dotimothy/TheDoPro/Documentation/Images/Figure for Methodology.png

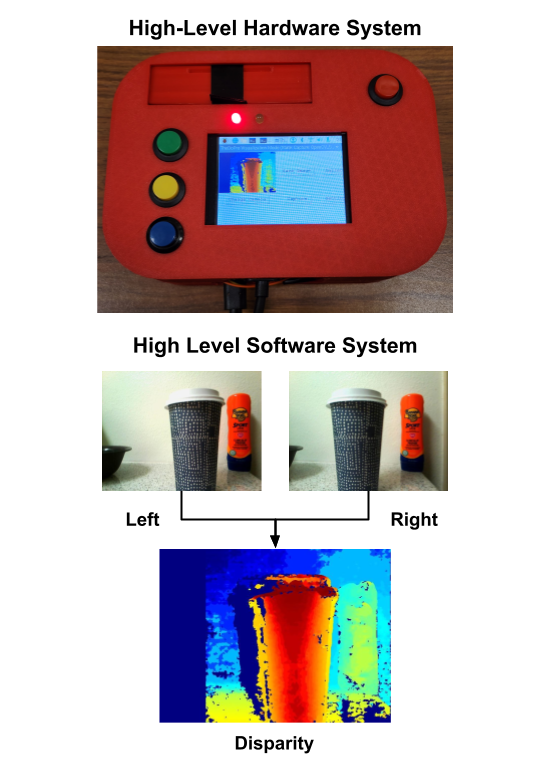
Documentation/Images/Figure for Methodology.png
