dotimothy/TheDoPro/Documentation/Images/pillow.jpg

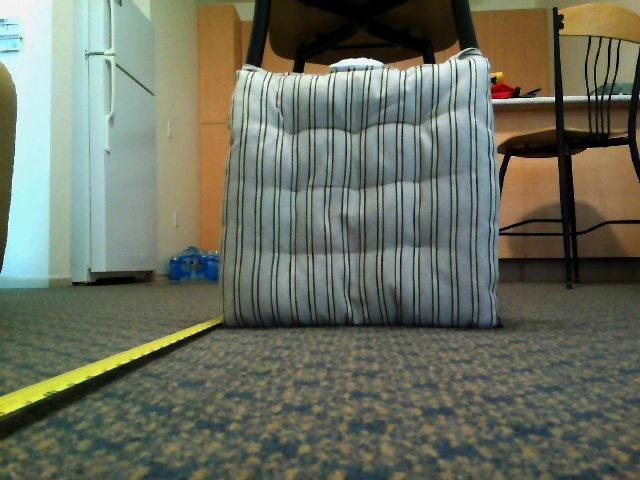
Documentation/Images/pillow.jpg
