dotimothy/TheDoPro/FSM/Stereovision CV FSM.png

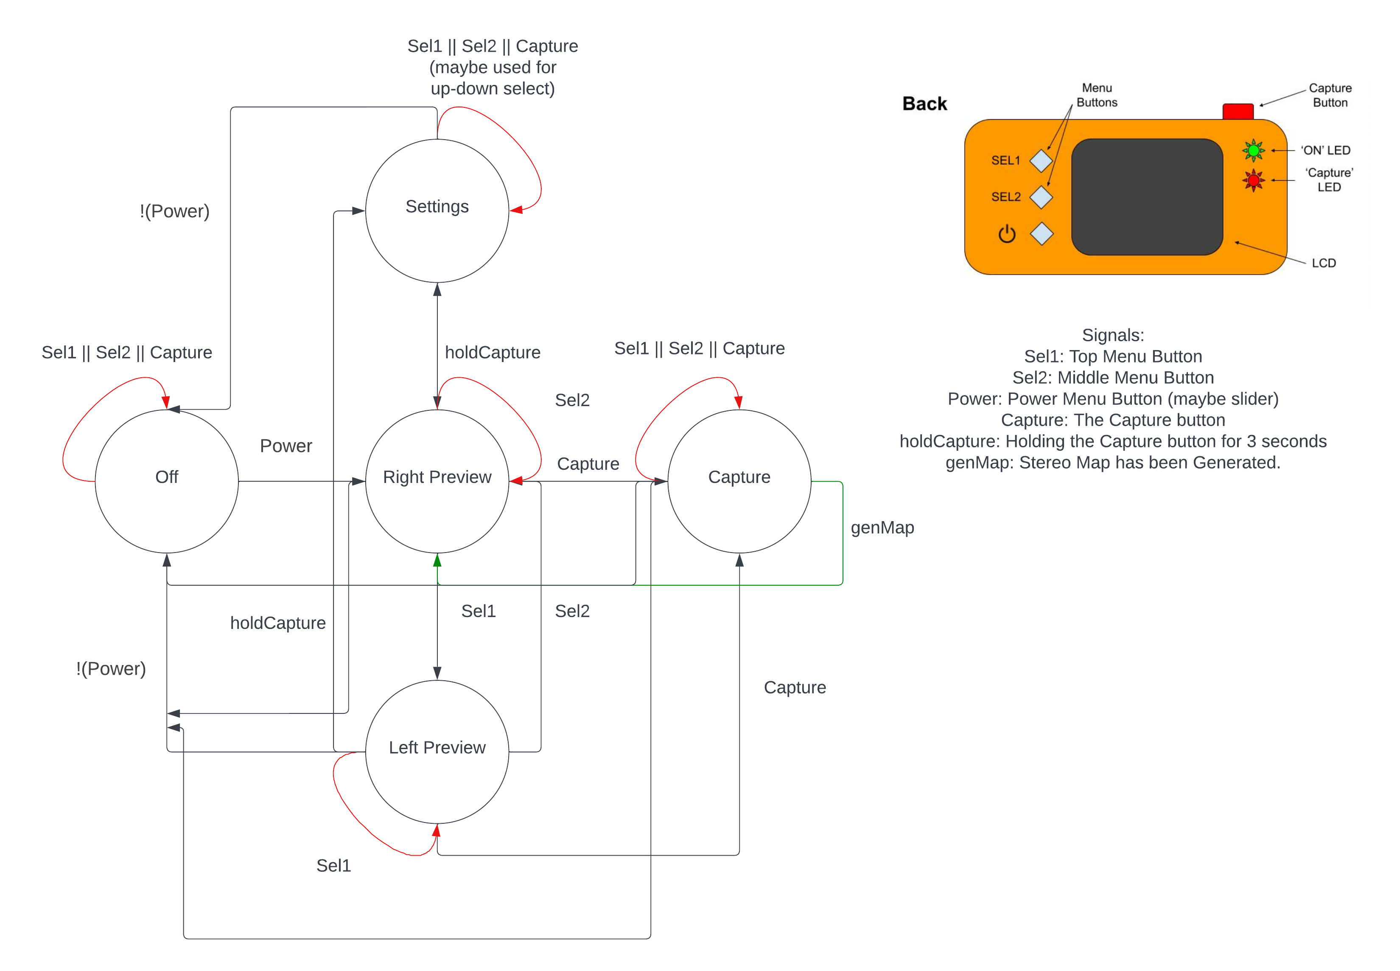
FSM/Stereovision CV FSM.png
