dotimothy/TheDoPro/Images/322023_20_57_38.jpg

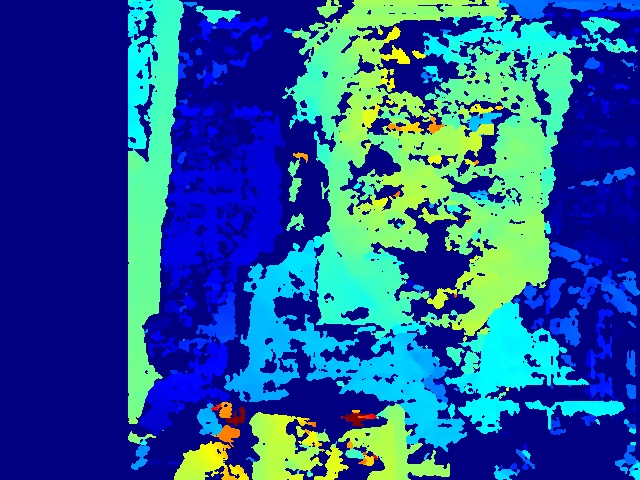
Images/322023_20_57_38.jpg
