dotimothy/TheDoPro/Images/322023_20_57_58.jpg

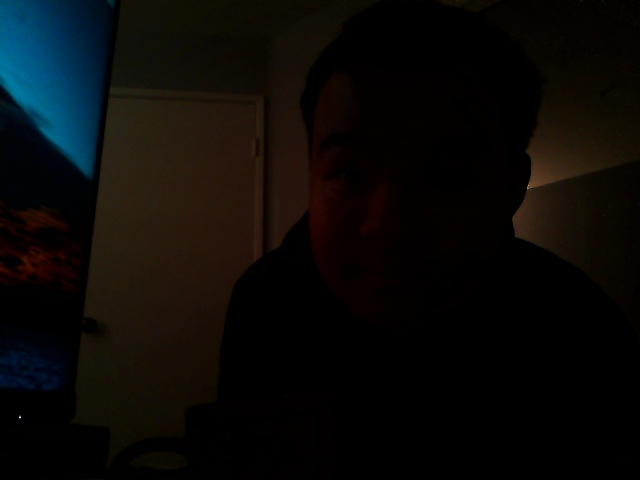
Images/322023_20_57_58.jpg
