dotimothy/TheDoPro/Images/cup_D.jpg

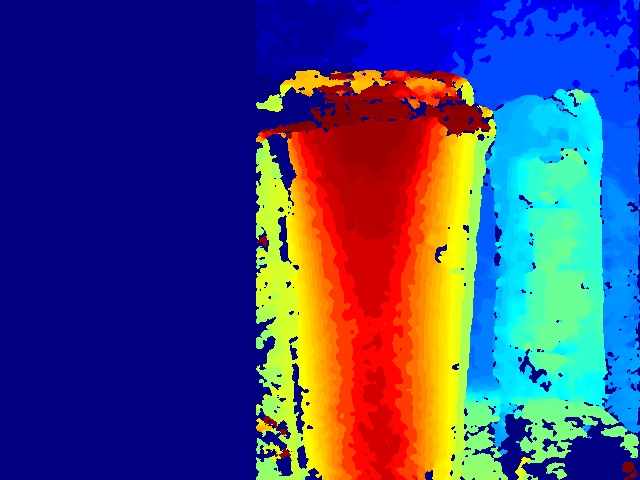
Images/cup_D.jpg
