dotimothy/TheDoPro/Images/cup_L.jpg

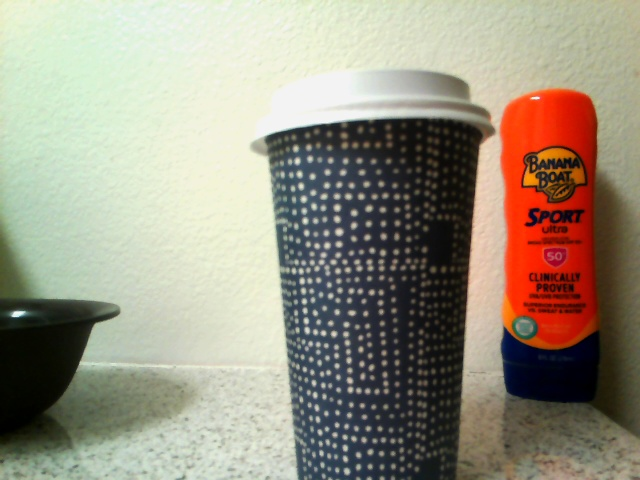
Images/cup_L.jpg
