dotimothy/TheDoPro/Images/cup_R.jpg

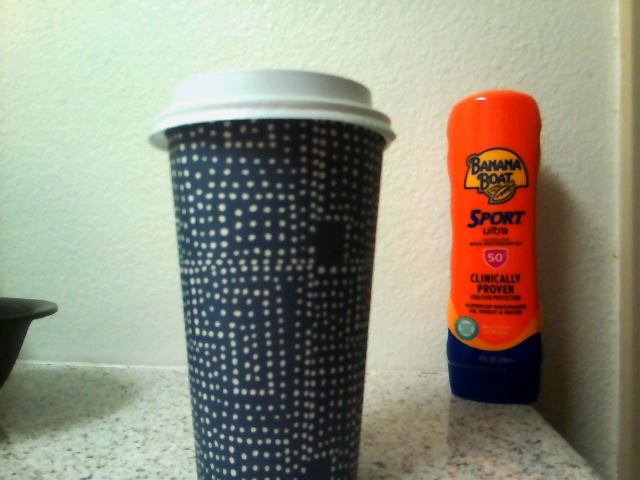
Images/cup_R.jpg
