dotimothy/TheDoPro/Images/cupandsalt_D.jpg

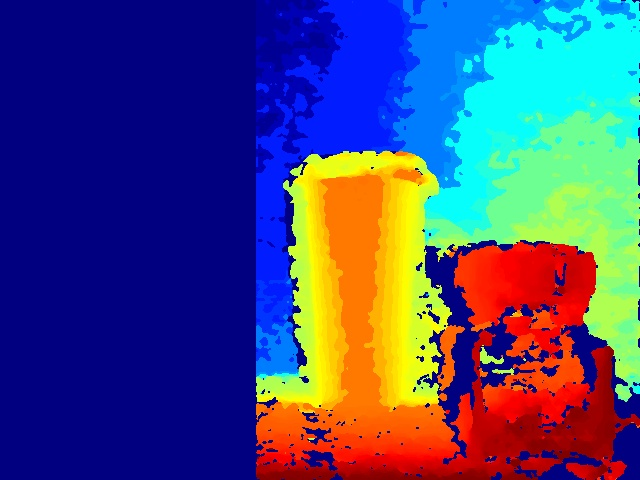
Images/cupandsalt_D.jpg
