dotimothy/TheDoPro/Images/cupandsalt_L.jpg

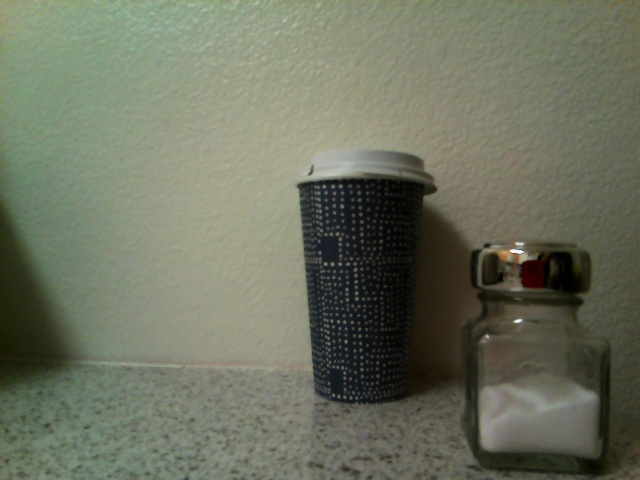
Images/cupandsalt_L.jpg
