dotimothy/TheDoPro/Images/cupandsalt_R.jpg

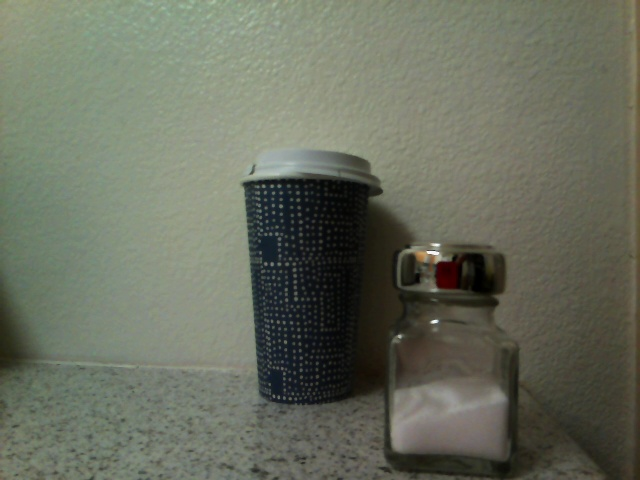
Images/cupandsalt_R.jpg
