dotimothy/TheDoPro/Images/daniel2_D.jpg

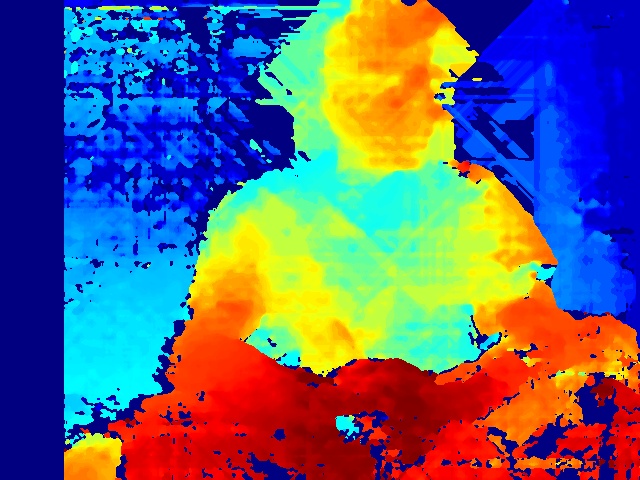
Images/daniel2_D.jpg
