dotimothy/TheDoPro/Images/daniel2_L.jpg

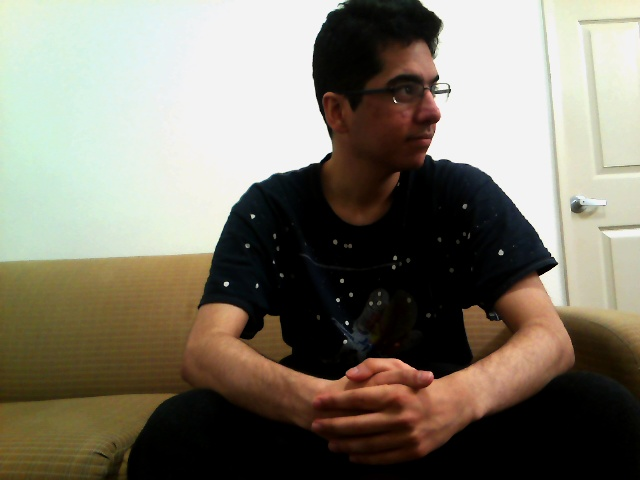
Images/daniel2_L.jpg
