dotimothy/TheDoPro/Images/daniel2_R.jpg

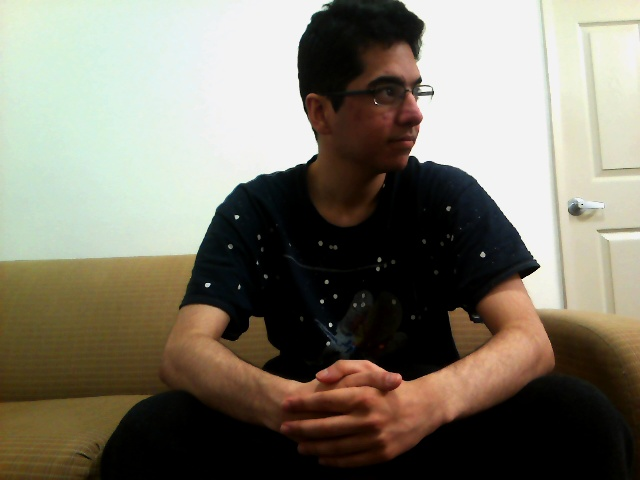
Images/daniel2_R.jpg
