dotimothy/TheDoPro/Images/daniel_D.jpg

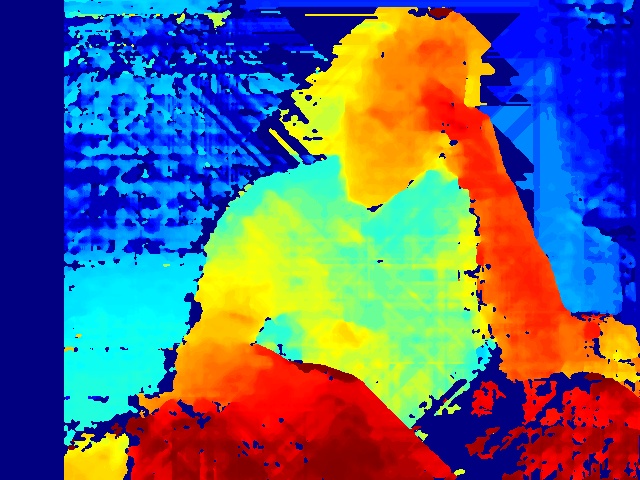
Images/daniel_D.jpg
