dotimothy/TheDoPro/Images/daniel_L.jpg

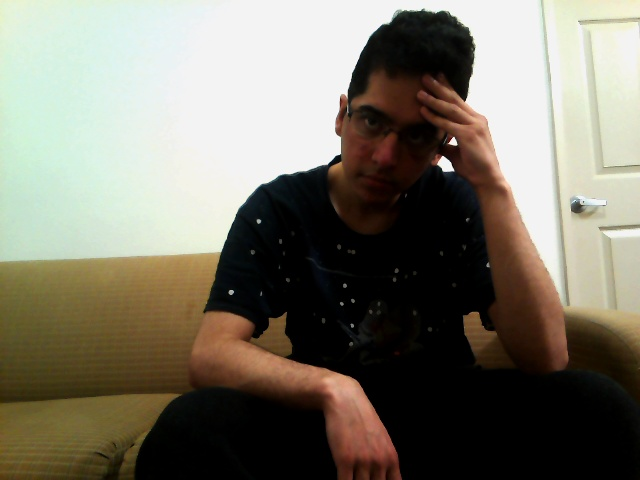
Images/daniel_L.jpg
