dotimothy/TheDoPro/Images/daniel_R.jpg

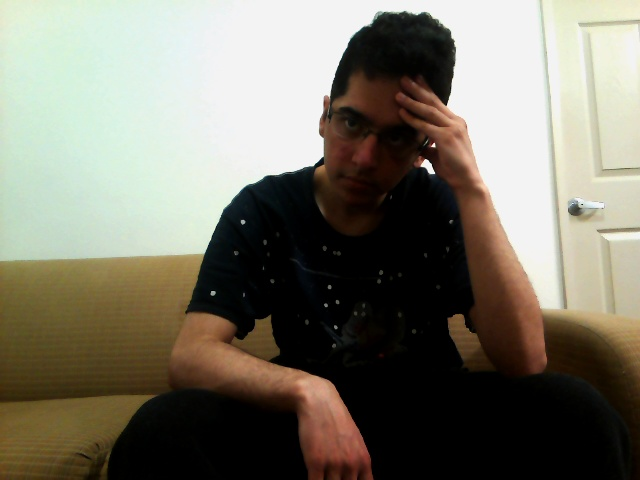
Images/daniel_R.jpg
