dotimothy/TheDoPro/Images/face_D.jpg

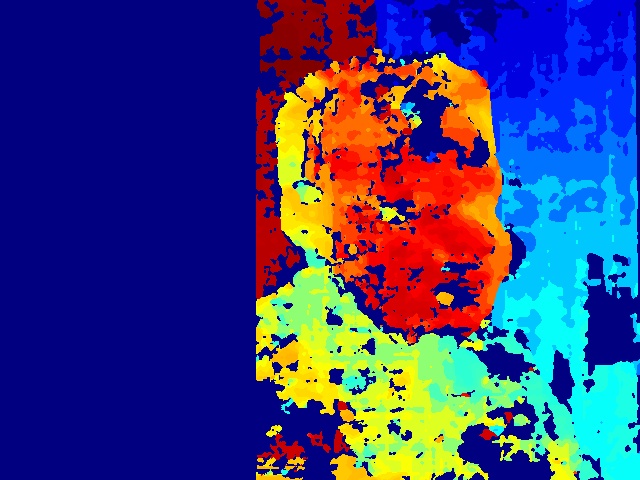
Images/face_D.jpg
