dotimothy/TheDoPro/Images/face_L.jpg

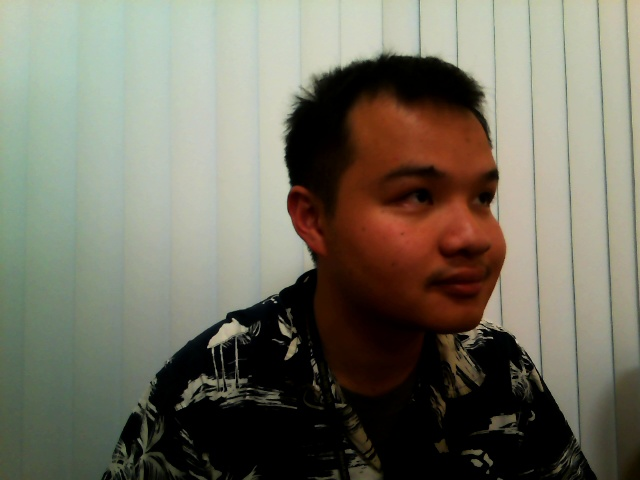
Images/face_L.jpg
