dotimothy/TheDoPro/Images/face_R.jpg

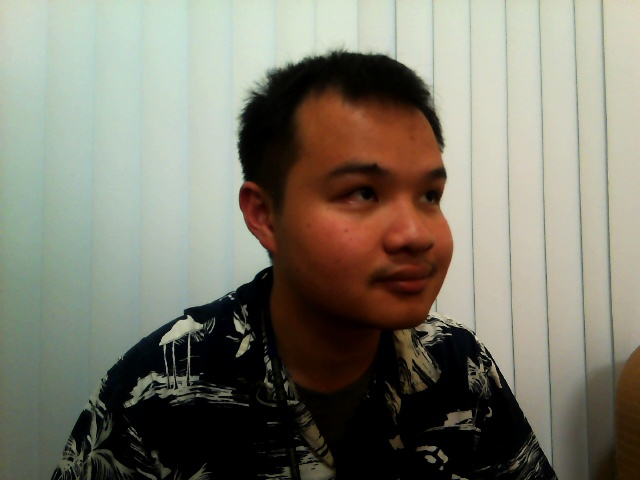
Images/face_R.jpg
