dotimothy/TheDoPro/Images/L_25.png

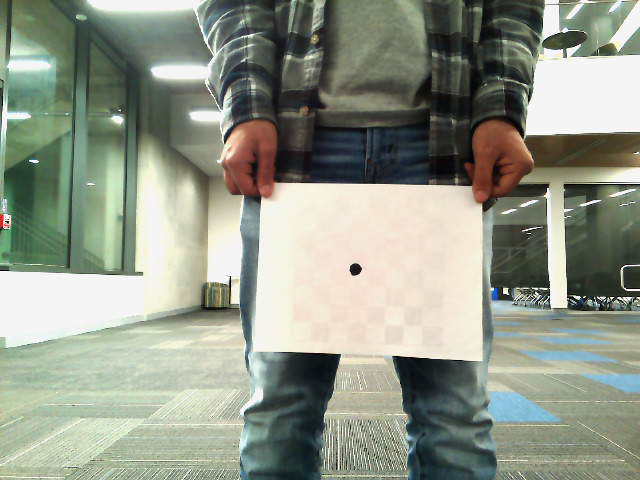
Images/L_25.png
