dotimothy/TheDoPro/Images/L_50.png

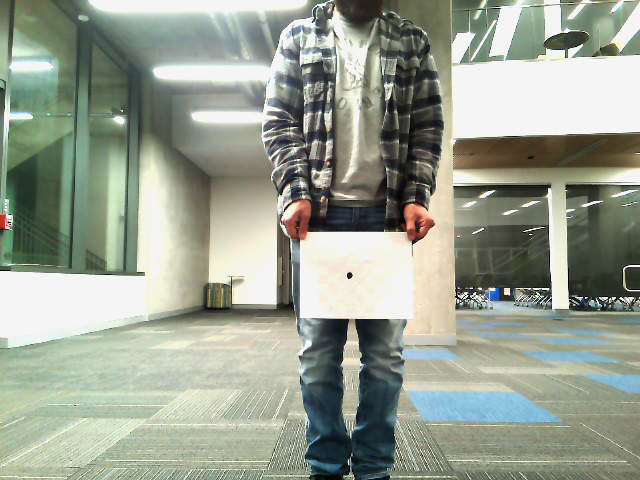
Images/L_50.png
