dotimothy/TheDoPro/Images/L_75.png

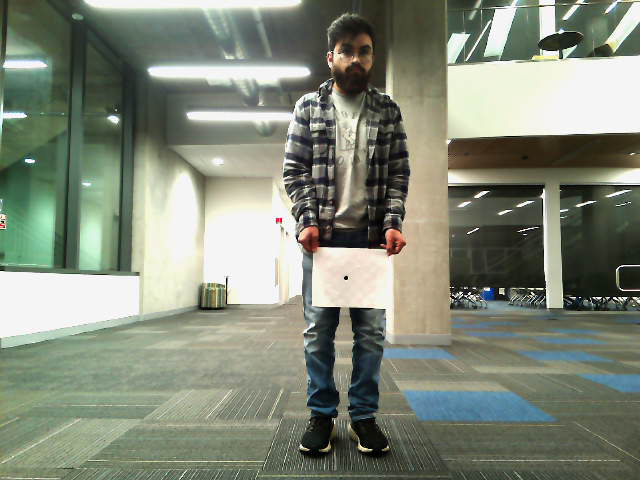
Images/L_75.png
