dotimothy/TheDoPro/Images/L_100.png

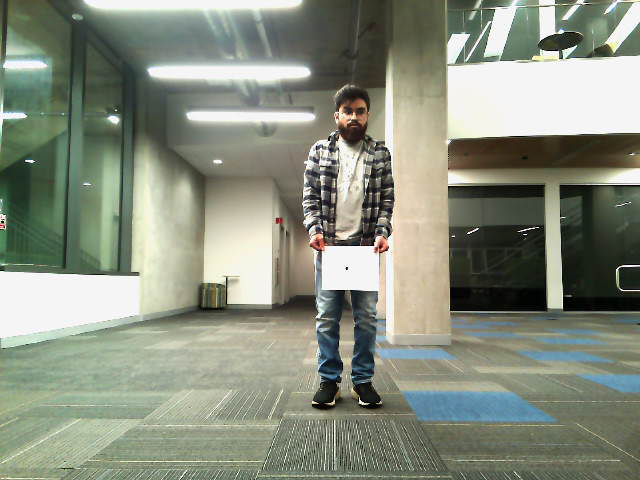
Images/L_100.png
