dotimothy/TheDoPro/Images/L_200.png

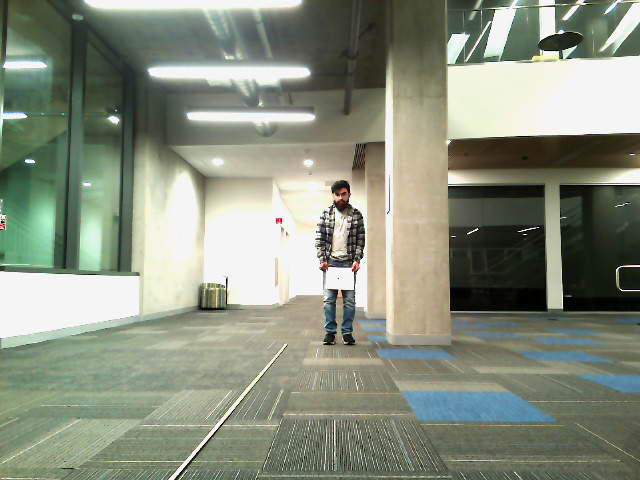
Images/L_200.png
