dotimothy/TheDoPro/Images/L_v2_25.png

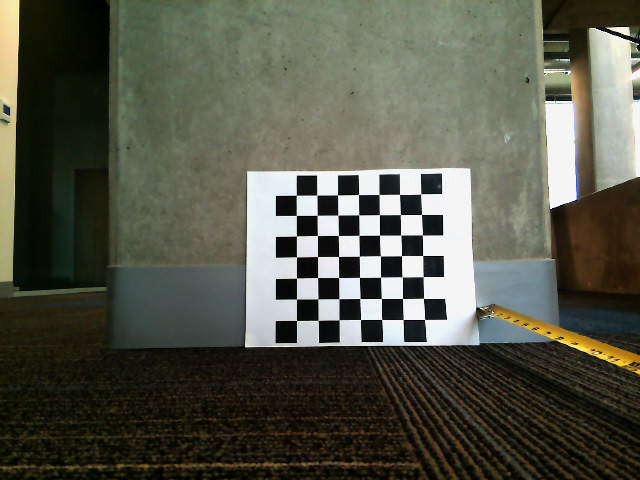
Images/L_v2_25.png
