dotimothy/TheDoPro/Images/L_v2_50.png

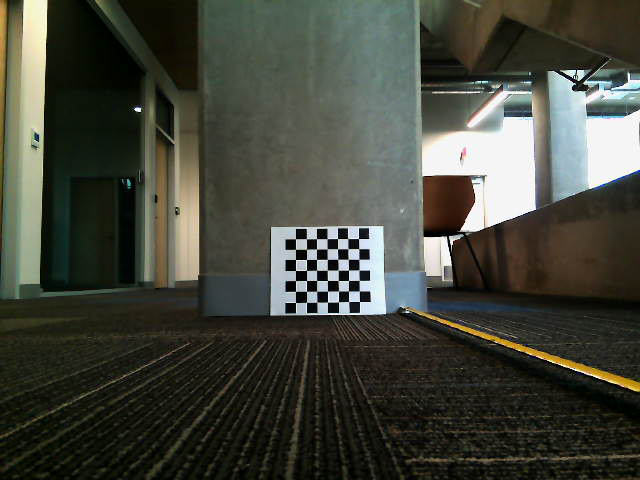
Images/L_v2_50.png
