dotimothy/TheDoPro/Images/L_v2_75.png

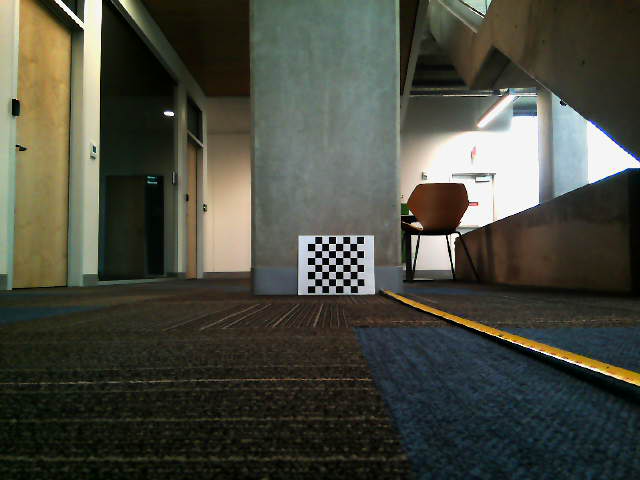
Images/L_v2_75.png
