dotimothy/TheDoPro/Images/L_v2_100.png

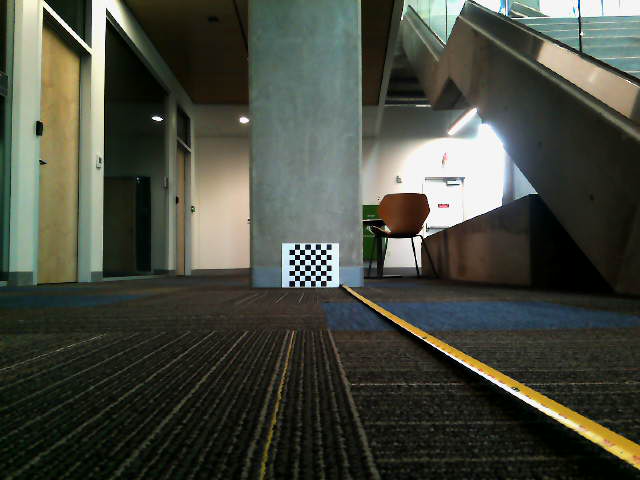
Images/L_v2_100.png
