dotimothy/TheDoPro/Images/left_piano_GT.jpg

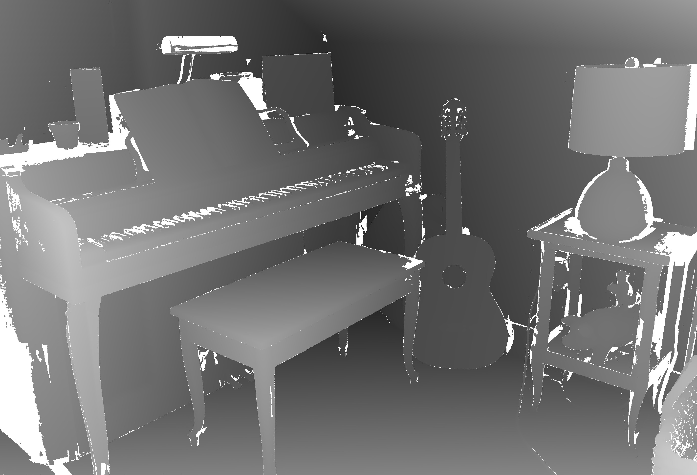
Images/left_piano_GT.jpg
