dotimothy/TheDoPro/Images/Mug_L_18.png

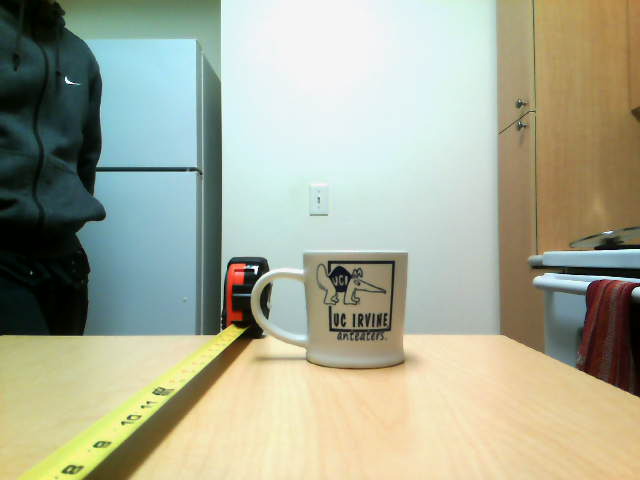
Images/Mug_L_18.png
