dotimothy/TheDoPro/Images/Mug_L_20.png

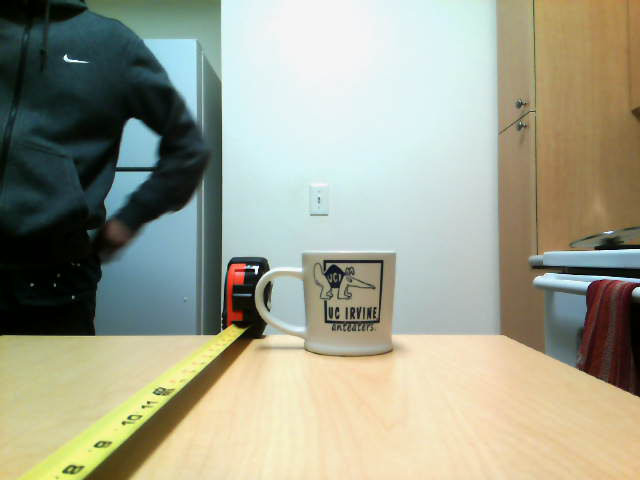
Images/Mug_L_20.png
