dotimothy/TheDoPro/Images/Mug_L_21.png

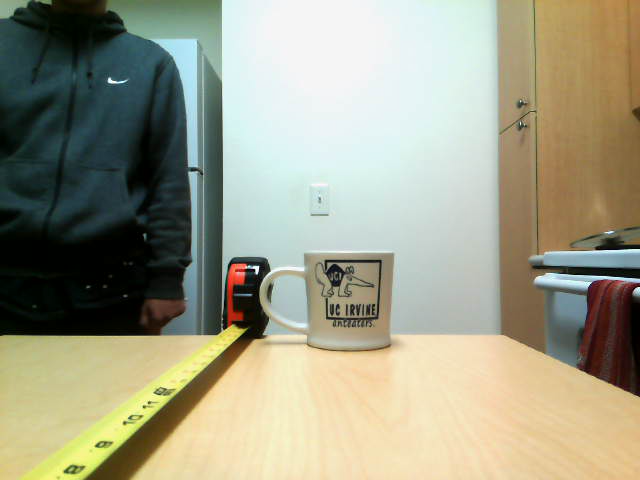
Images/Mug_L_21.png
