dotimothy/TheDoPro/Images/Mug_R_18.png

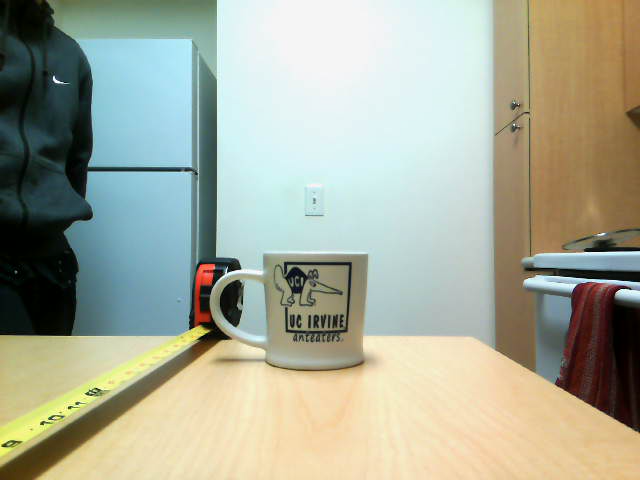
Images/Mug_R_18.png
