dotimothy/TheDoPro/Images/Mug_R_21.png

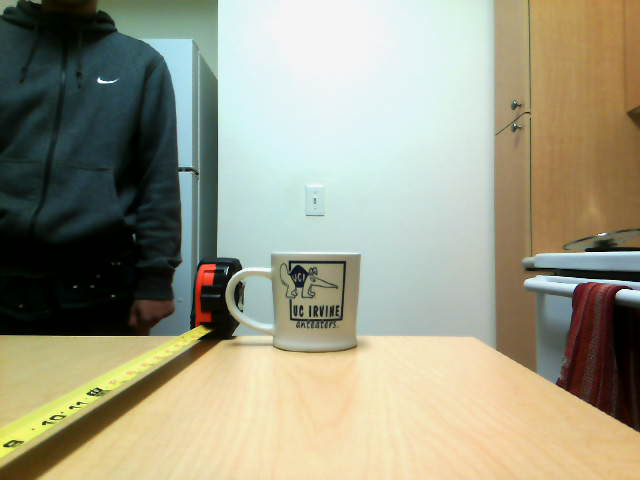
Images/Mug_R_21.png
