dotimothy/TheDoPro/Images/Mug_R_22.png

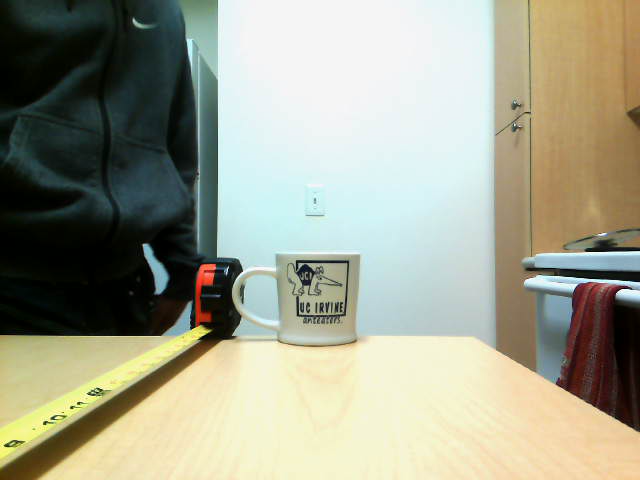
Images/Mug_R_22.png
