dotimothy/TheDoPro/Images/openCV.png

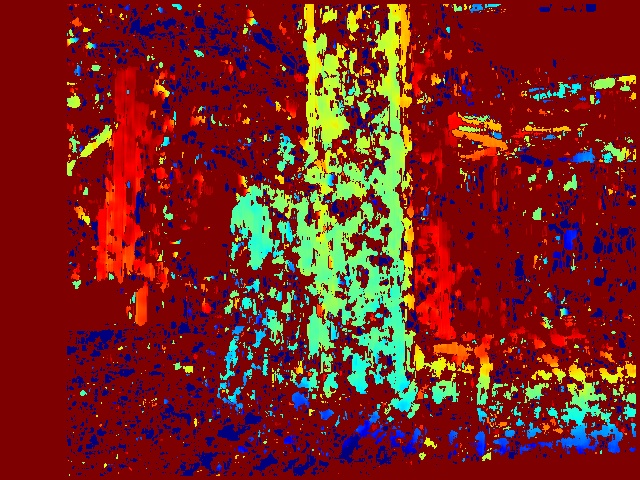
Images/openCV.png
