dotimothy/TheDoPro/Images/Pillow/ADAS_64/D_BM_3.jpg

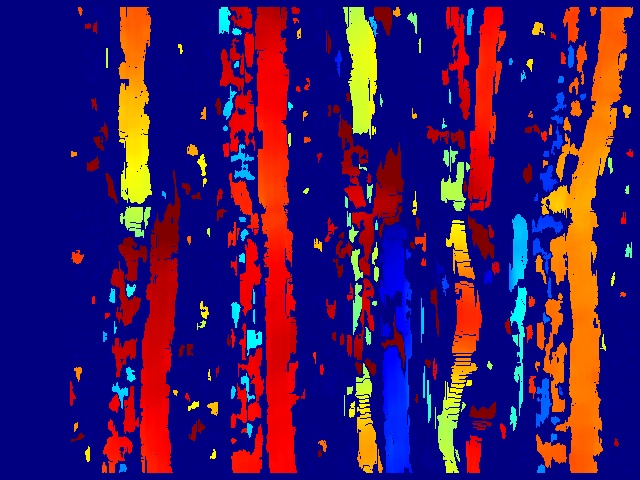
Images/Pillow/ADAS_64/D_BM_3.jpg
