dotimothy/TheDoPro/Images/Pillow/ADAS_64/D_BM_6.jpg

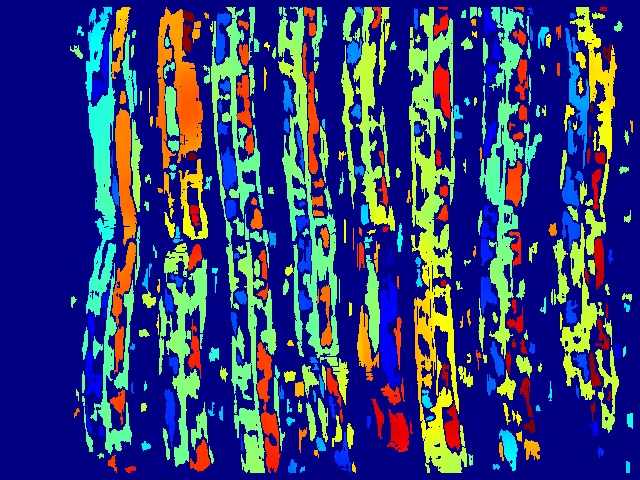
Images/Pillow/ADAS_64/D_BM_6.jpg
