dotimothy/TheDoPro/Images/Pillow/ADAS_64/D_BM_9.jpg

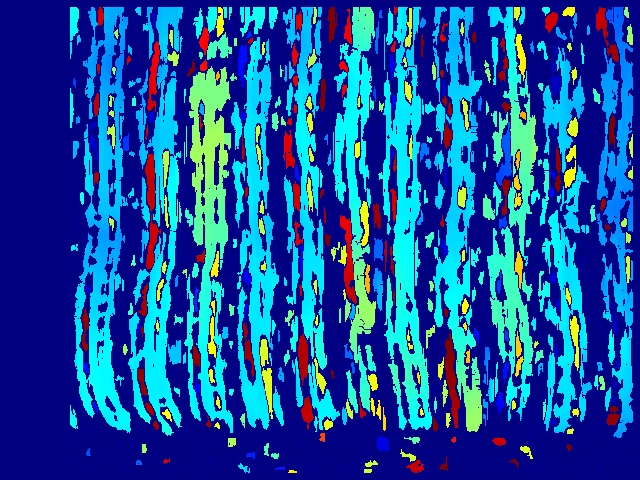
Images/Pillow/ADAS_64/D_BM_9.jpg
