dotimothy/TheDoPro/Images/Pillow/ADAS_64/D_BM_12.jpg

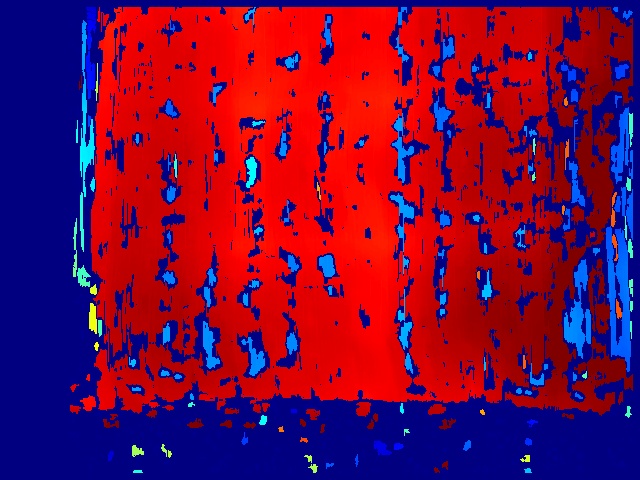
Images/Pillow/ADAS_64/D_BM_12.jpg
