dotimothy/TheDoPro/Images/Pillow/ADAS_64/D_BM_15.jpg

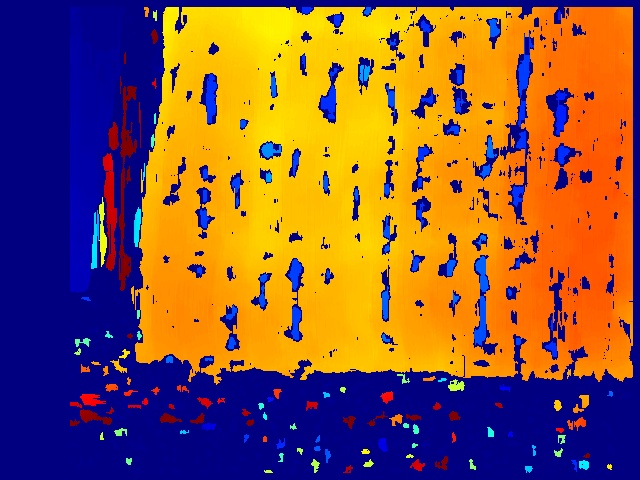
Images/Pillow/ADAS_64/D_BM_15.jpg
