dotimothy/TheDoPro/Images/Pillow/ADAS_64/D_BM_18.jpg

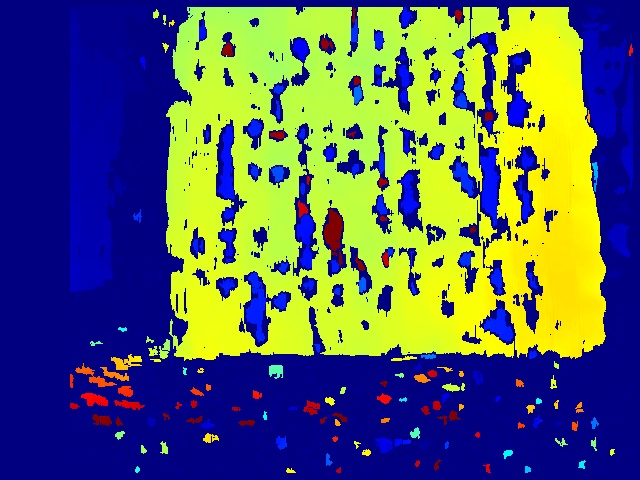
Images/Pillow/ADAS_64/D_BM_18.jpg
