dotimothy/TheDoPro/Images/Pillow/ADAS_64/D_BM_21.jpg

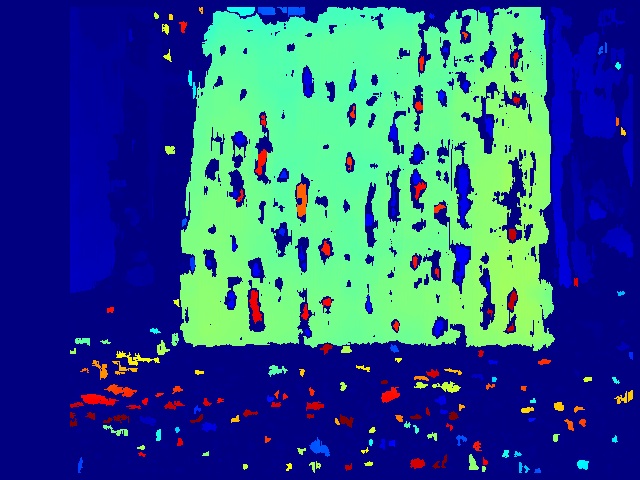
Images/Pillow/ADAS_64/D_BM_21.jpg
