dotimothy/TheDoPro/Images/Pillow/ADAS_64/D_BM_24.jpg

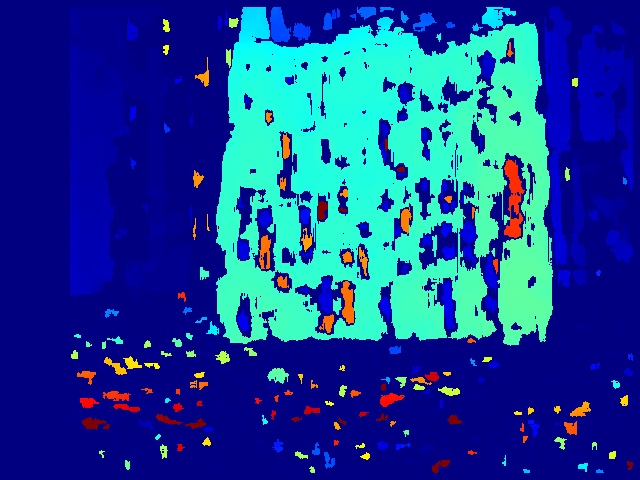
Images/Pillow/ADAS_64/D_BM_24.jpg
