dotimothy/TheDoPro/Images/Pillow/ADAS_64/D_BM_27.jpg

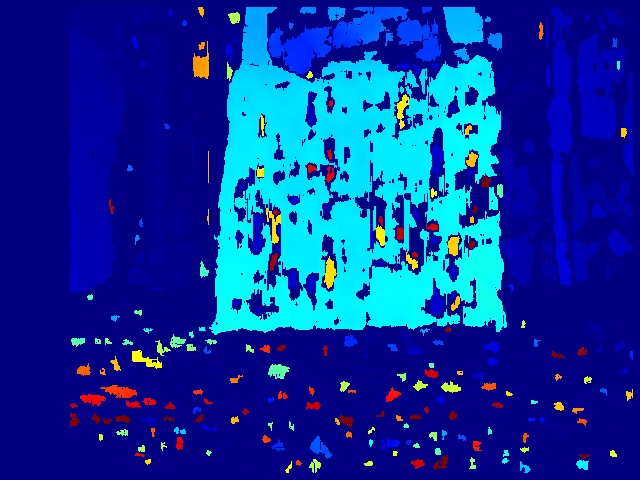
Images/Pillow/ADAS_64/D_BM_27.jpg
