dotimothy/TheDoPro/Images/Pillow/ADAS_64/D_BM_30.jpg

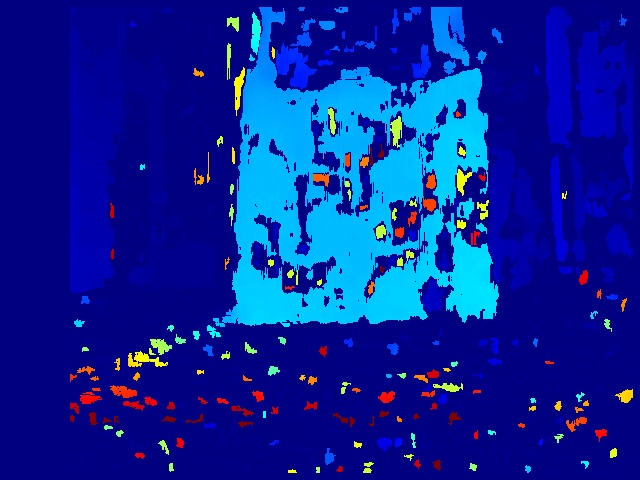
Images/Pillow/ADAS_64/D_BM_30.jpg
