dotimothy/TheDoPro/Images/Pillow/ADAS_64/D_BM_33.jpg

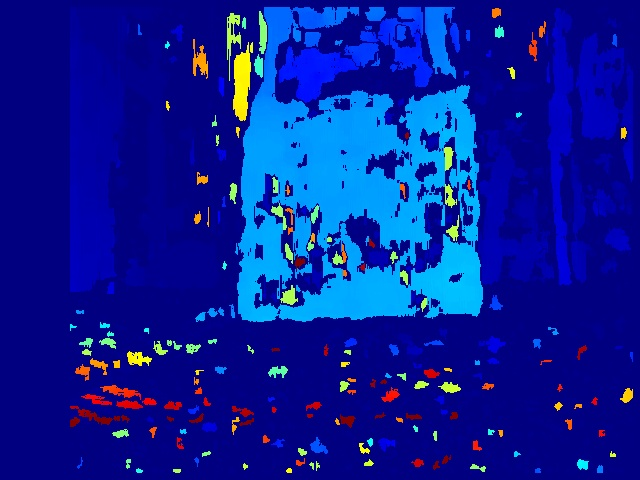
Images/Pillow/ADAS_64/D_BM_33.jpg
