dotimothy/TheDoPro/Images/Pillow/ADAS_64/D_BM_36.jpg

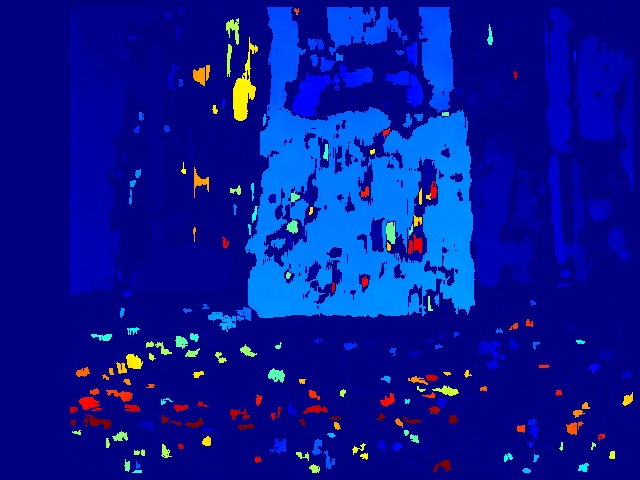
Images/Pillow/ADAS_64/D_BM_36.jpg
