dotimothy/TheDoPro/Images/Pillow/ADAS_64/D_BM_39.jpg

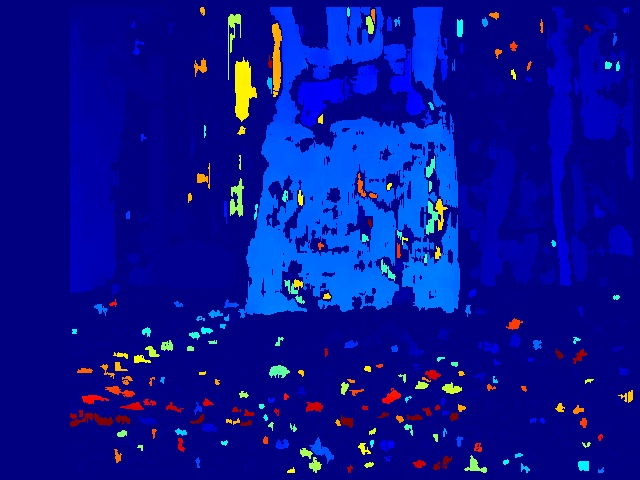
Images/Pillow/ADAS_64/D_BM_39.jpg
