dotimothy/TheDoPro/Images/Pillow/ADAS_64/D_BM_42.jpg

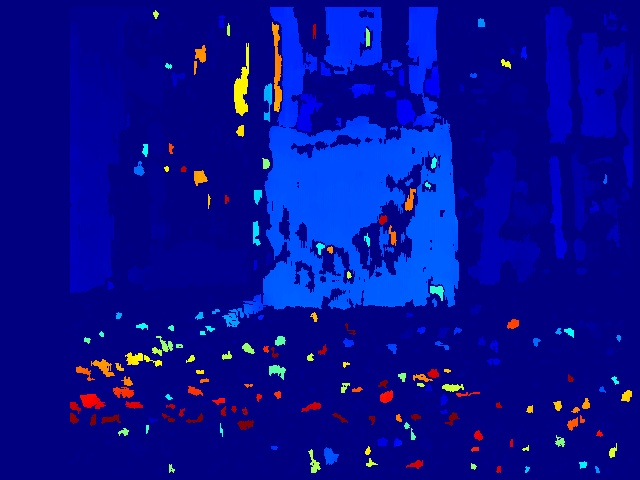
Images/Pillow/ADAS_64/D_BM_42.jpg
