dotimothy/TheDoPro/Images/Pillow/ADAS_64/D_BM_45.jpg

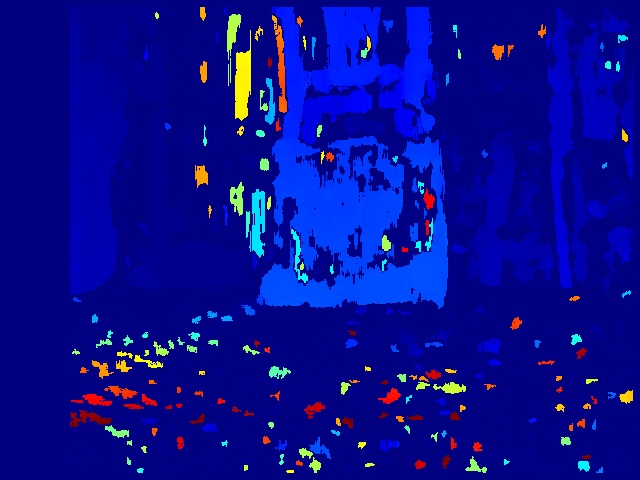
Images/Pillow/ADAS_64/D_BM_45.jpg
