dotimothy/TheDoPro/Images/Pillow/ADAS_64/D_BM_48.jpg

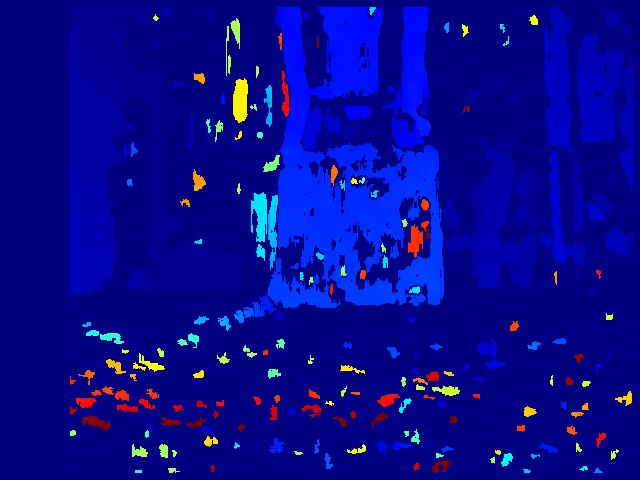
Images/Pillow/ADAS_64/D_BM_48.jpg
