dotimothy/TheDoPro/Images/Pillow/ADAS_64/D_BM_54.jpg

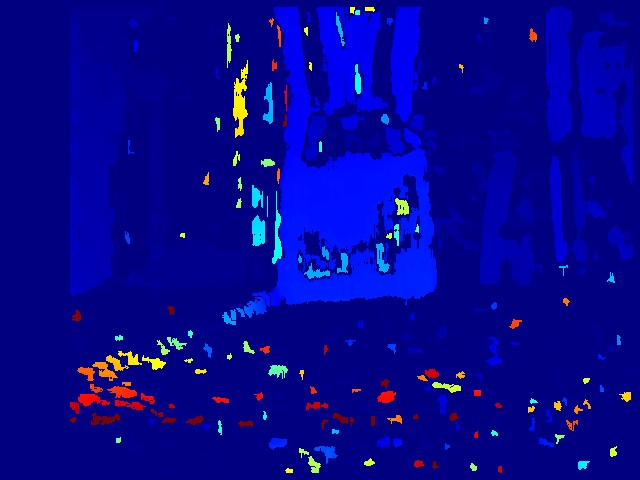
Images/Pillow/ADAS_64/D_BM_54.jpg
