dotimothy/TheDoPro/Images/Pillow/ADAS_64/D_BM_60.jpg

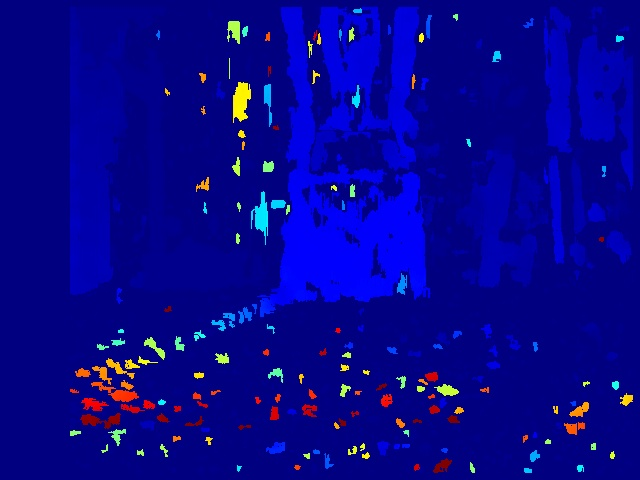
Images/Pillow/ADAS_64/D_BM_60.jpg
