dotimothy/TheDoPro/Images/Pillow/ADAS_64/D_BM_66.jpg

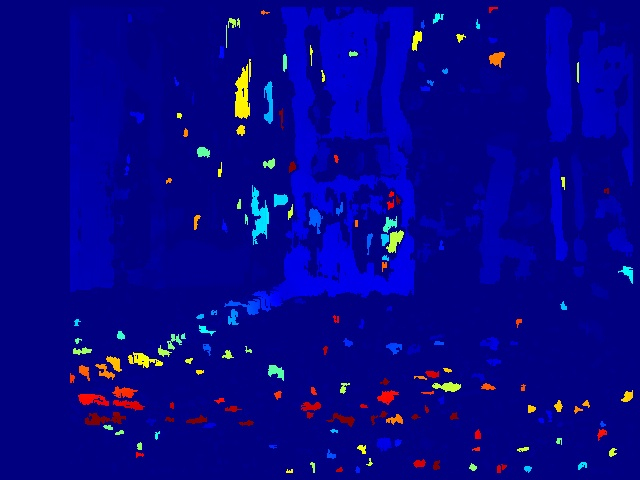
Images/Pillow/ADAS_64/D_BM_66.jpg
