dotimothy/TheDoPro/Images/Pillow/ADAS_64/D_BM_72.jpg

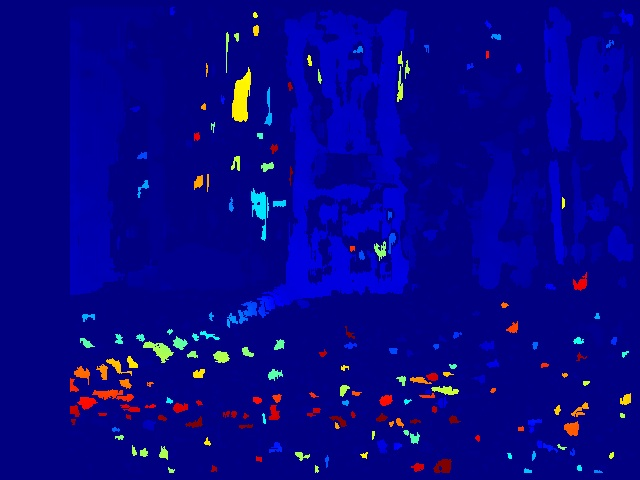
Images/Pillow/ADAS_64/D_BM_72.jpg
