dotimothy/TheDoPro/Images/Pillow/ADAS_64/D_SGBM_3.jpg

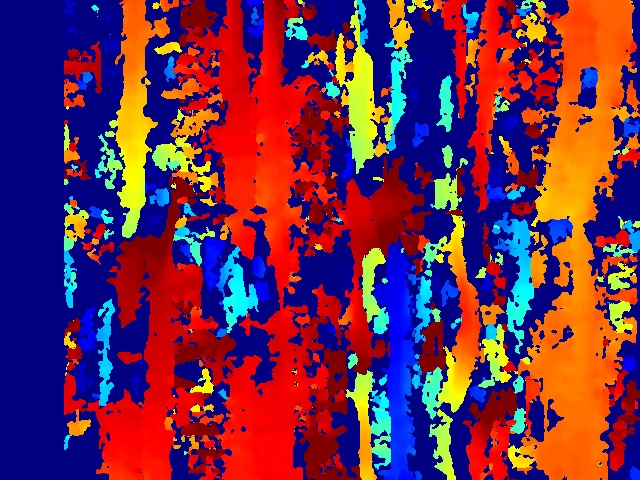
Images/Pillow/ADAS_64/D_SGBM_3.jpg
