dotimothy/TheDoPro/Images/Pillow/ADAS_64/D_SGBM_6.jpg

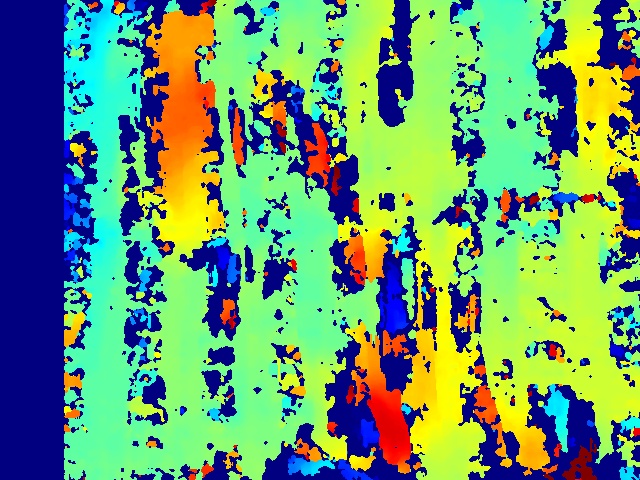
Images/Pillow/ADAS_64/D_SGBM_6.jpg
