dotimothy/TheDoPro/Images/Pillow/ADAS_64/D_SGBM_9.jpg

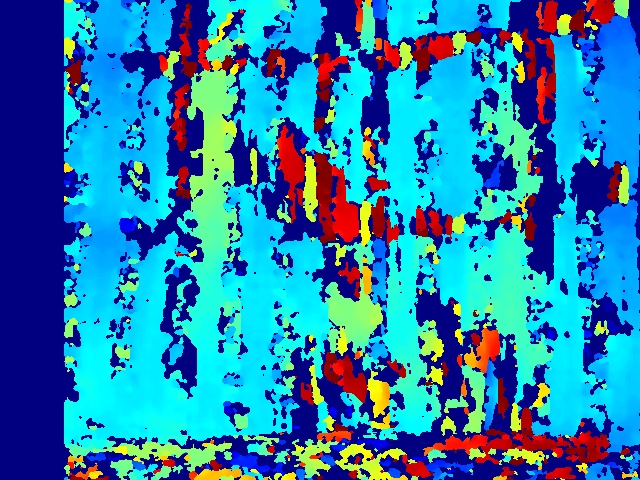
Images/Pillow/ADAS_64/D_SGBM_9.jpg
