dotimothy/TheDoPro/Images/Pillow/ADAS_64/D_SGBM_12.jpg

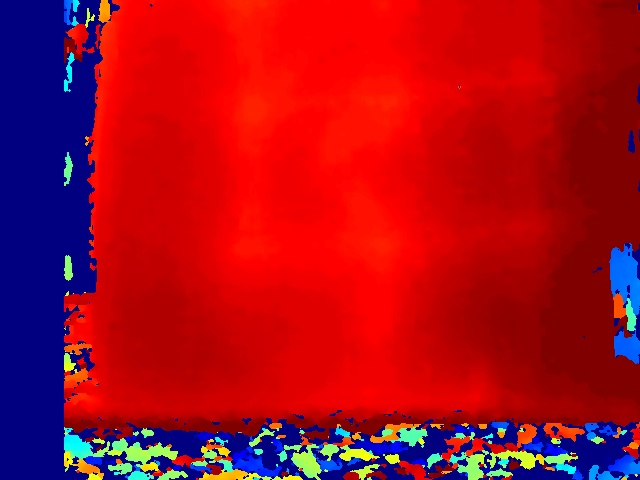
Images/Pillow/ADAS_64/D_SGBM_12.jpg
