dotimothy/TheDoPro/Images/Pillow/ADAS_64/D_SGBM_15.jpg

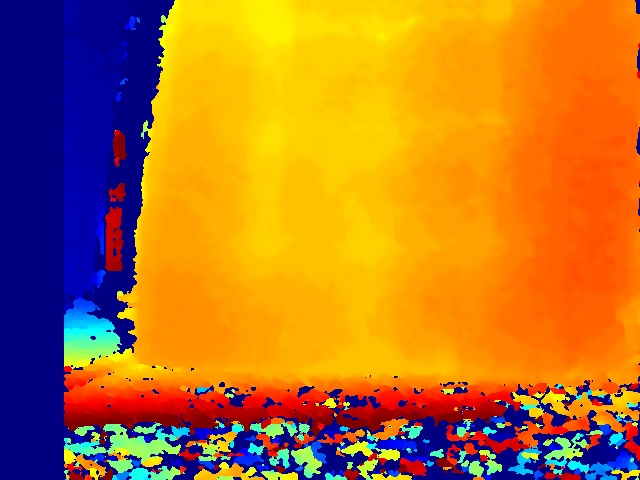
Images/Pillow/ADAS_64/D_SGBM_15.jpg
