dotimothy/TheDoPro/Images/Pillow/ADAS_64/D_SGBM_18.jpg

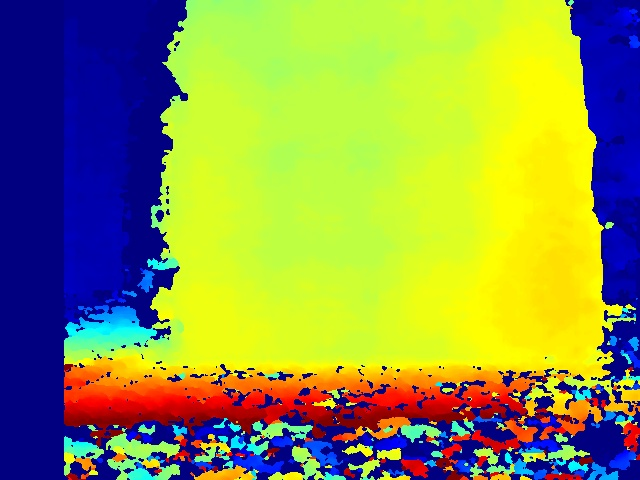
Images/Pillow/ADAS_64/D_SGBM_18.jpg
