dotimothy/TheDoPro/Images/Pillow/ADAS_64/D_SGBM_21.jpg

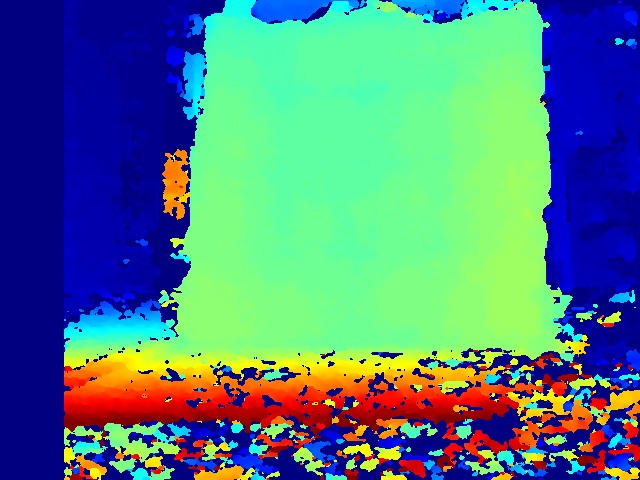
Images/Pillow/ADAS_64/D_SGBM_21.jpg
