dotimothy/TheDoPro/Images/Pillow/ADAS_64/D_SGBM_24.jpg

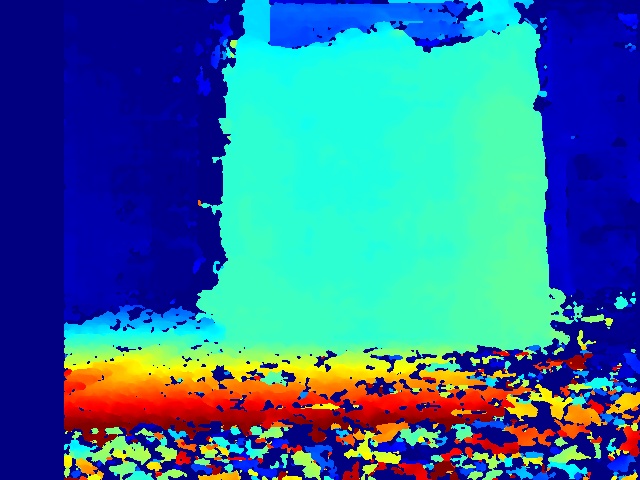
Images/Pillow/ADAS_64/D_SGBM_24.jpg
