dotimothy/TheDoPro/Images/Pillow/ADAS_64/D_SGBM_27.jpg

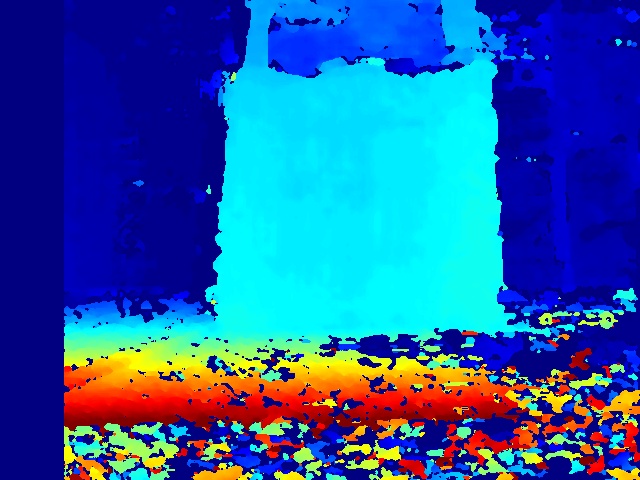
Images/Pillow/ADAS_64/D_SGBM_27.jpg
