dotimothy/TheDoPro/Images/Pillow/ADAS_64/D_SGBM_30.jpg

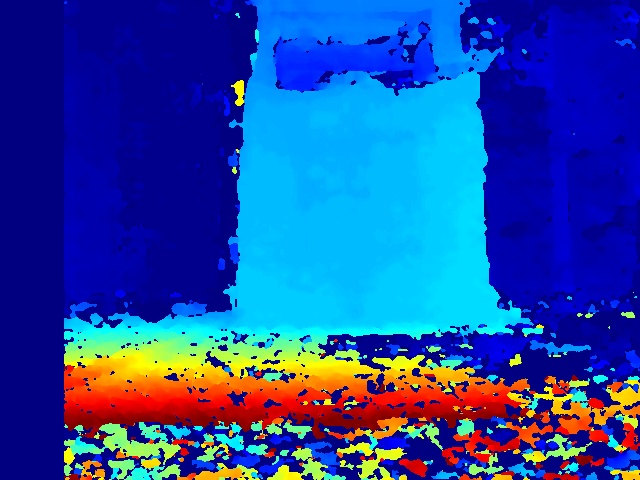
Images/Pillow/ADAS_64/D_SGBM_30.jpg
