dotimothy/TheDoPro/Images/Pillow/ADAS_64/D_SGBM_36.jpg

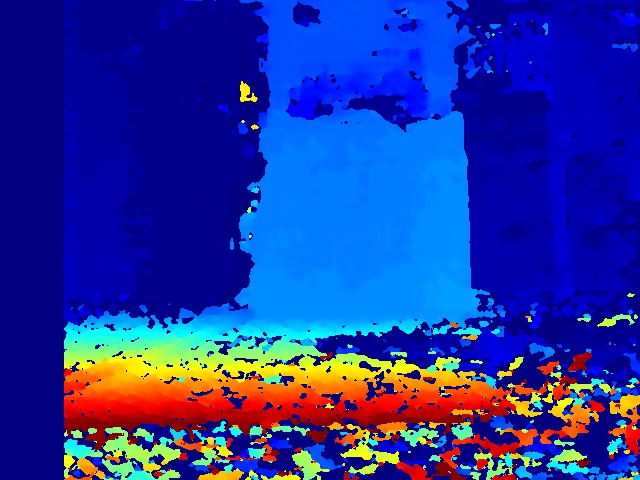
Images/Pillow/ADAS_64/D_SGBM_36.jpg
