dotimothy/TheDoPro/Images/Pillow/ADAS_64/D_SGBM_39.jpg

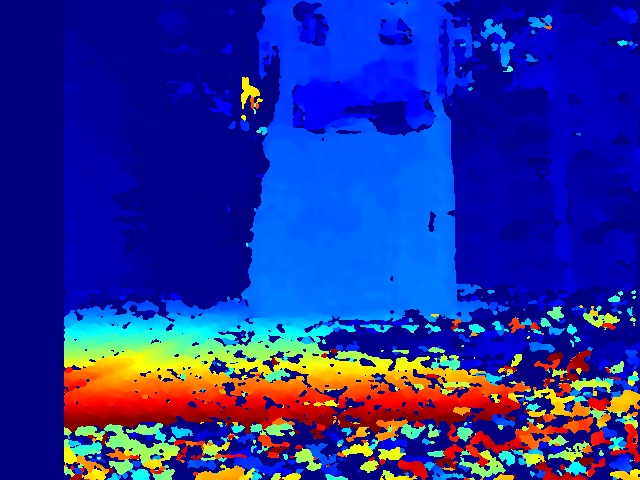
Images/Pillow/ADAS_64/D_SGBM_39.jpg
