dotimothy/TheDoPro/Images/Pillow/ADAS_64/D_SGBM_42.jpg

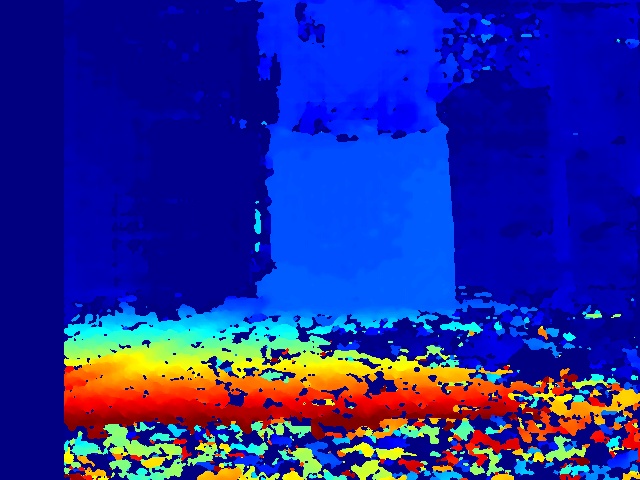
Images/Pillow/ADAS_64/D_SGBM_42.jpg
