dotimothy/TheDoPro/Images/Pillow/ADAS_64/D_SGBM_48.jpg

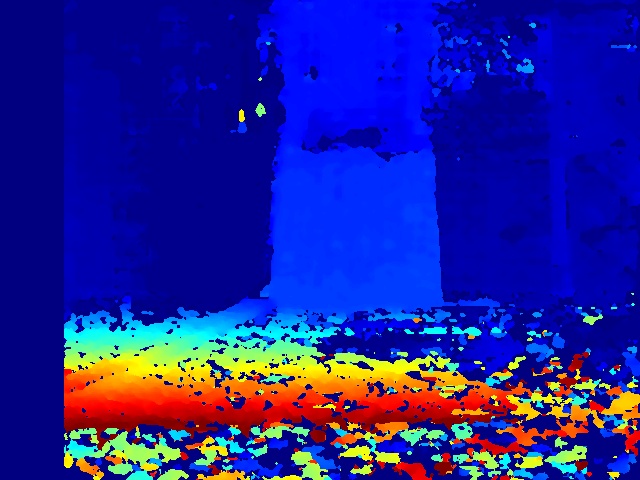
Images/Pillow/ADAS_64/D_SGBM_48.jpg
