dotimothy/TheDoPro/Images/Pillow/ADAS_64/D_SGBM_54.jpg

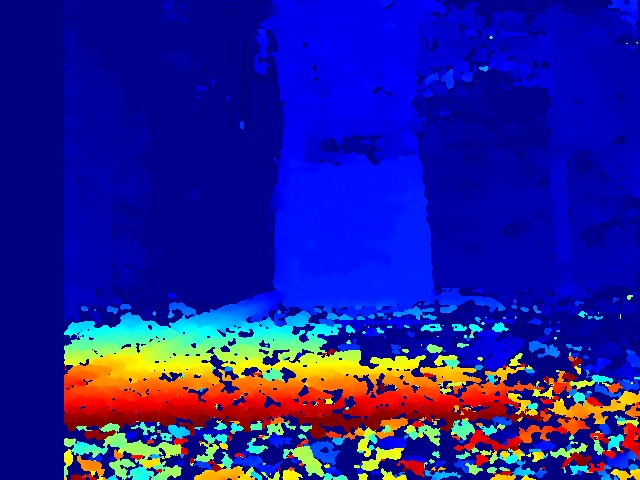
Images/Pillow/ADAS_64/D_SGBM_54.jpg
