dotimothy/TheDoPro/Images/Pillow/ADAS_64/D_SGBM_60.jpg

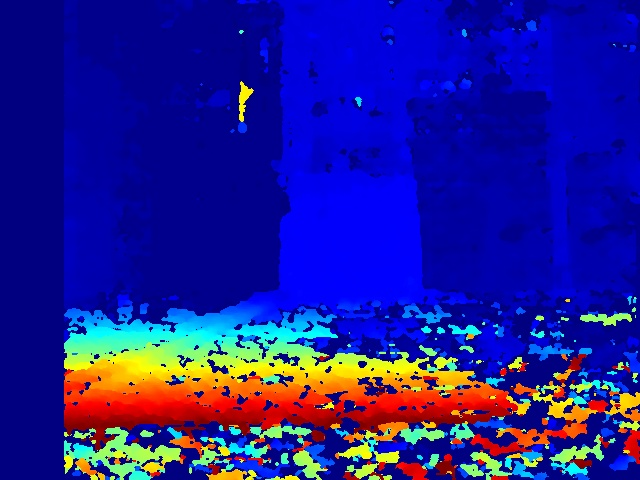
Images/Pillow/ADAS_64/D_SGBM_60.jpg
