dotimothy/TheDoPro/Images/Pillow/ADAS_64/D_SGBM_66.jpg

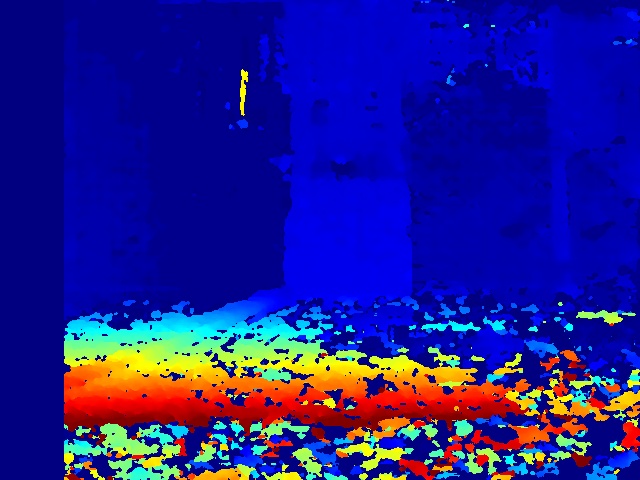
Images/Pillow/ADAS_64/D_SGBM_66.jpg
