dotimothy/TheDoPro/Images/Pillow/ADAS_64/D_SGBM_72.jpg

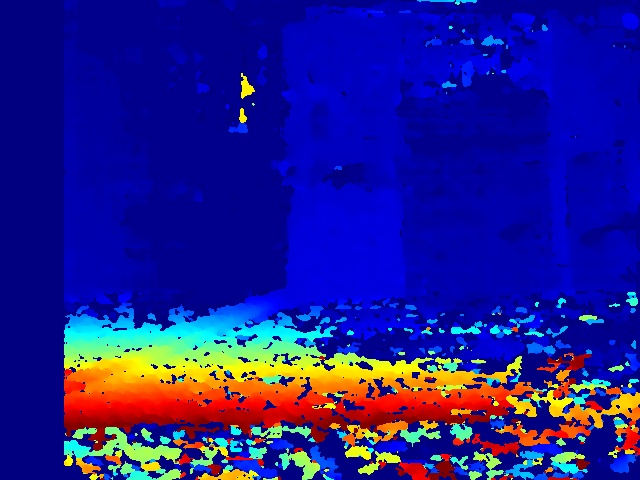
Images/Pillow/ADAS_64/D_SGBM_72.jpg
