dotimothy/TheDoPro/Images/Pillow/dispvsdepth.png

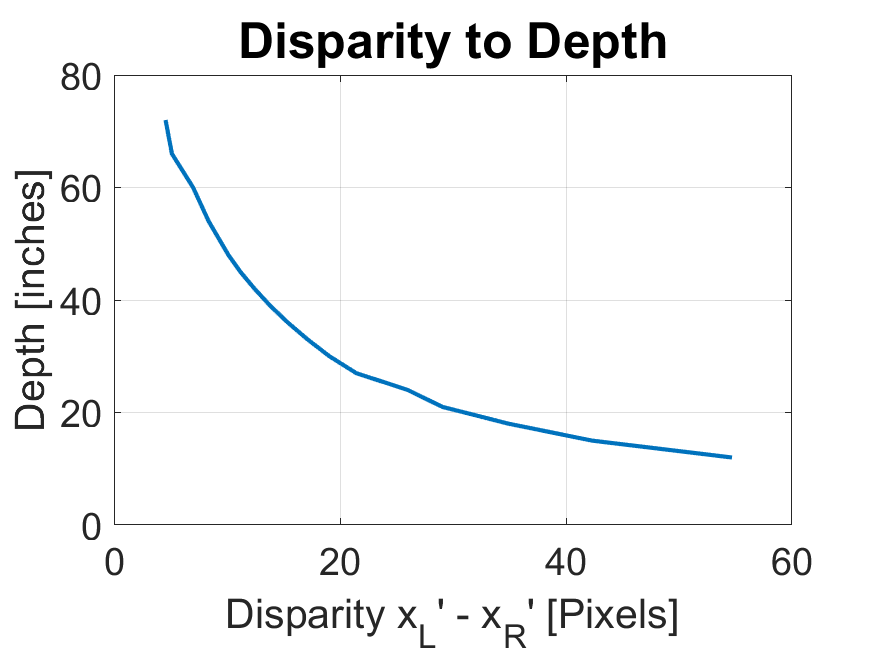
Images/Pillow/dispvsdepth.png
