dotimothy/TheDoPro/Images/Pillow/L_3.jpg

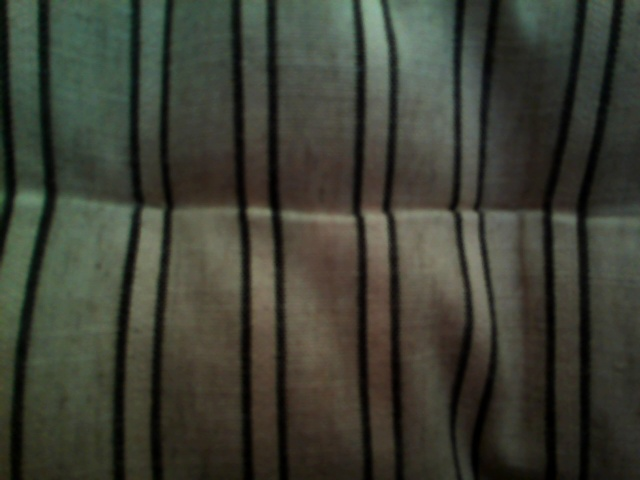
Images/Pillow/L_3.jpg
