dotimothy/TheDoPro/Images/Pillow/L_6.jpg

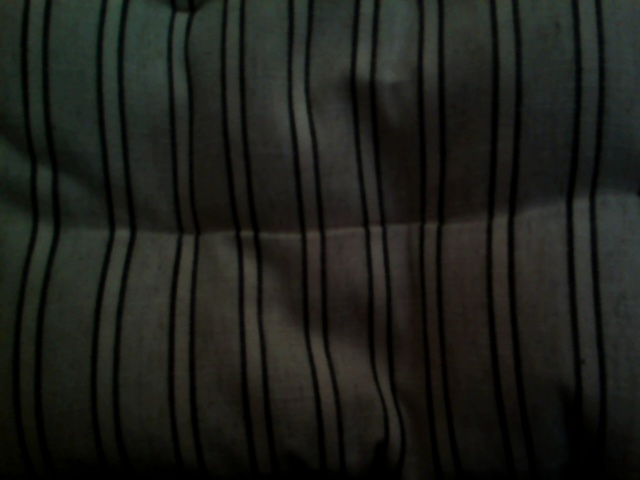
Images/Pillow/L_6.jpg
