dotimothy/TheDoPro/Images/Pillow/L_9.jpg

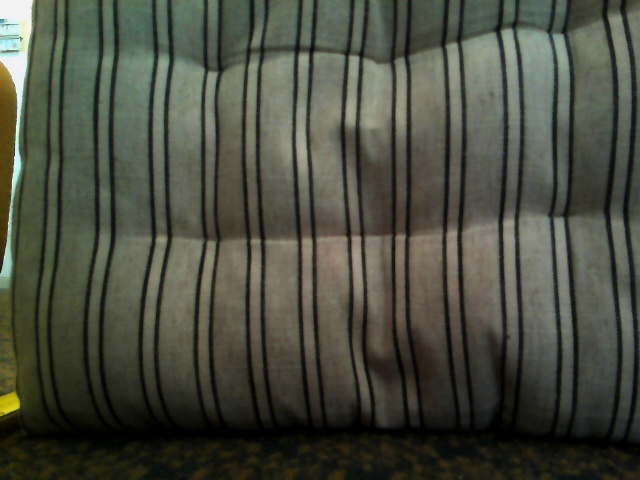
Images/Pillow/L_9.jpg
