dotimothy/TheDoPro/Images/Pillow/L_12.jpg

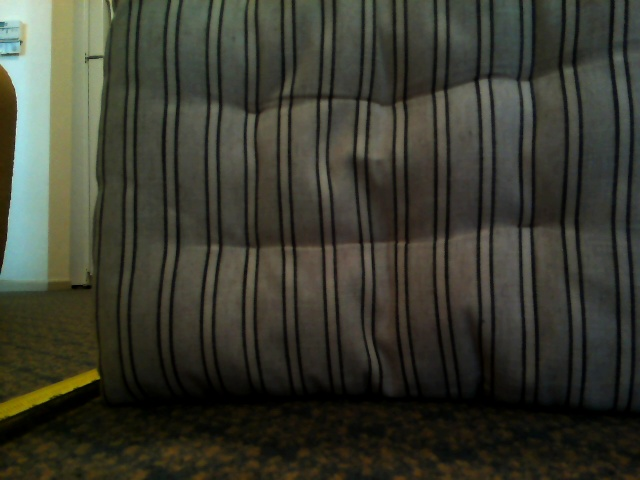
Images/Pillow/L_12.jpg
