dotimothy/TheDoPro/Images/Pillow/L_15.jpg

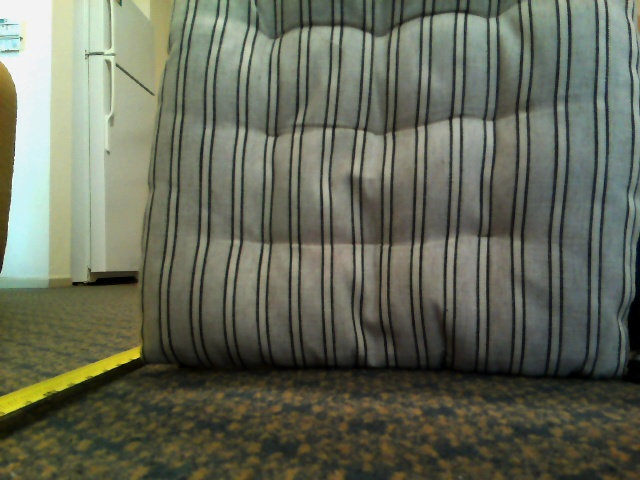
Images/Pillow/L_15.jpg
