dotimothy/TheDoPro/Images/Pillow/L_18.jpg

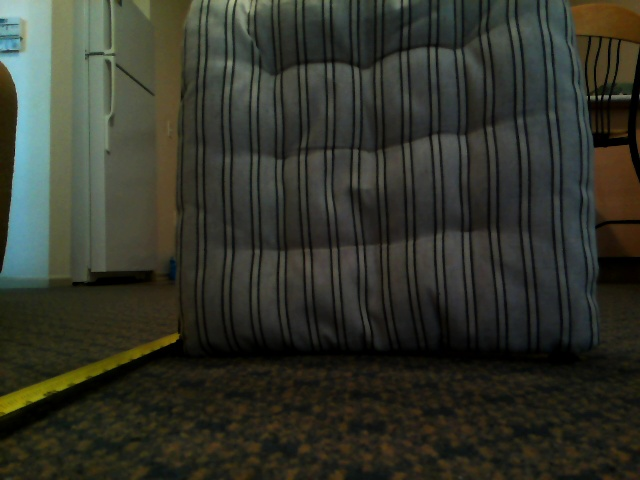
Images/Pillow/L_18.jpg
