dotimothy/TheDoPro/Images/Pillow/L_21.jpg

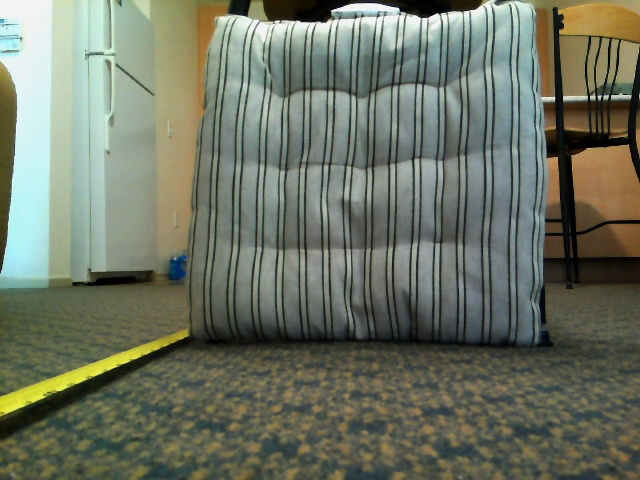
Images/Pillow/L_21.jpg
