dotimothy/TheDoPro/Images/Pillow/L_24.jpg

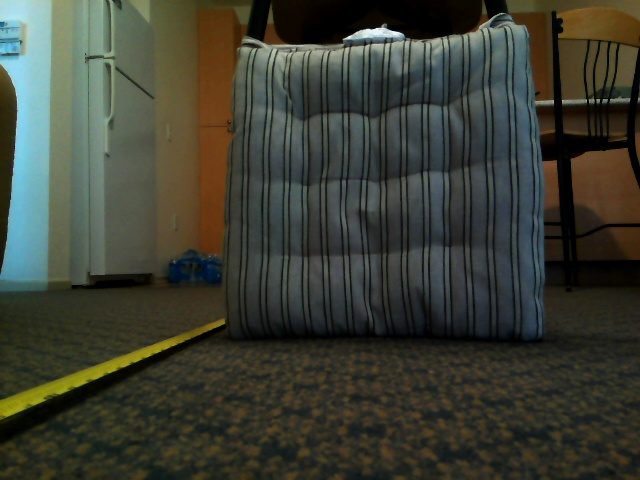
Images/Pillow/L_24.jpg
