dotimothy/TheDoPro/Images/Pillow/L_30.jpg

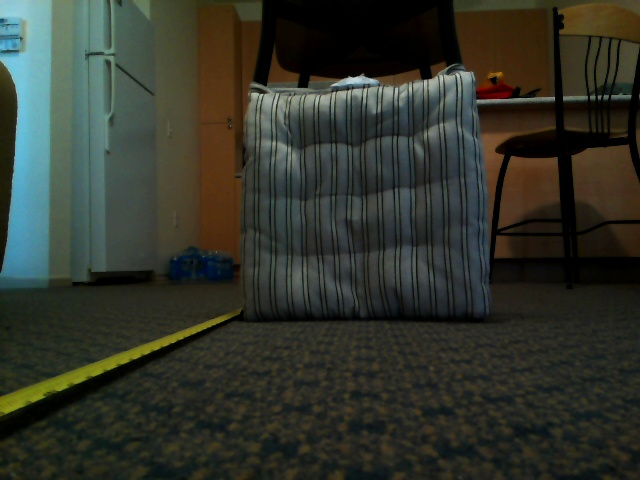
Images/Pillow/L_30.jpg
