dotimothy/TheDoPro/Images/Pillow/L_33.jpg

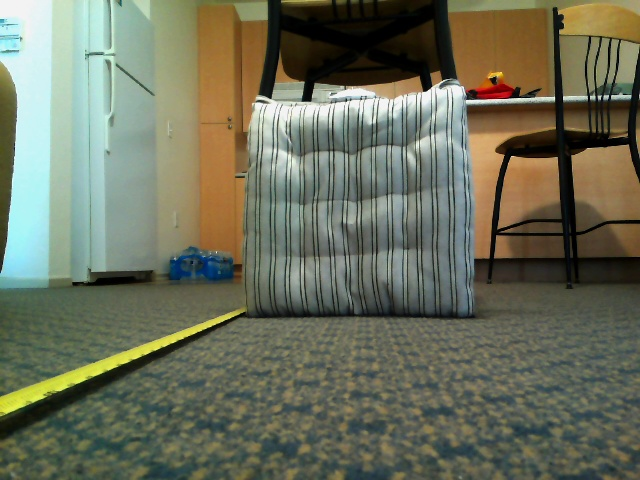
Images/Pillow/L_33.jpg
