dotimothy/TheDoPro/Images/Pillow/L_36.jpg

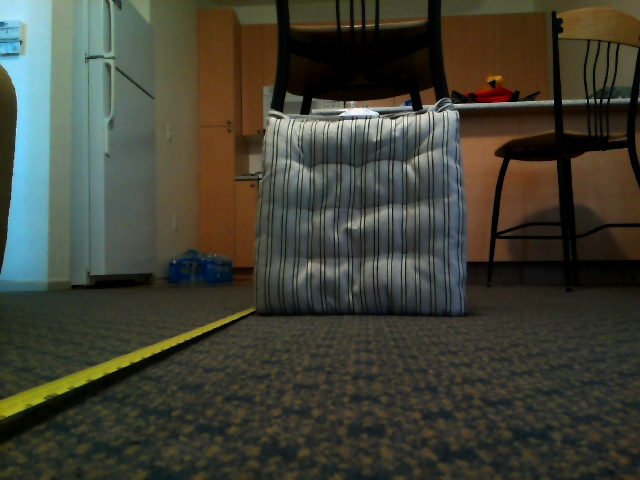
Images/Pillow/L_36.jpg
