dotimothy/TheDoPro/Images/Pillow/L_39.jpg

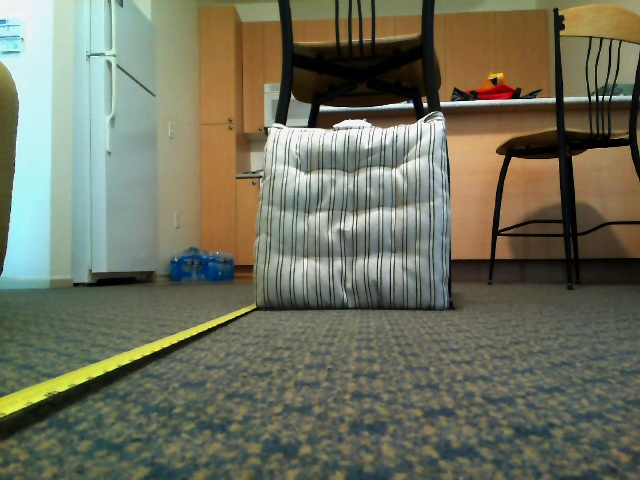
Images/Pillow/L_39.jpg
