dotimothy/TheDoPro/Images/Pillow/L_42.jpg

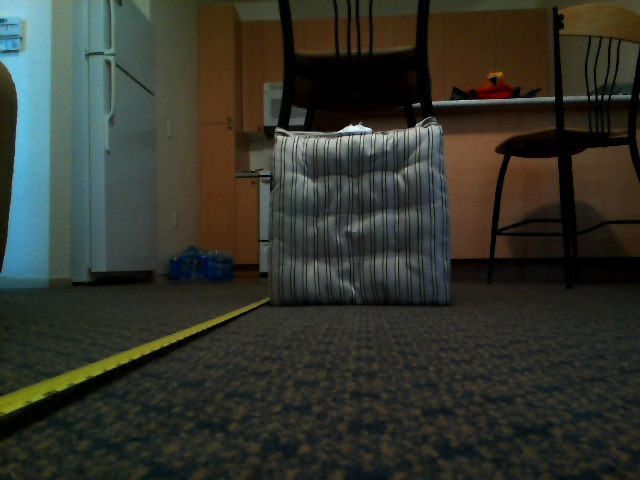
Images/Pillow/L_42.jpg
