dotimothy/TheDoPro/Images/Pillow/L_48.jpg

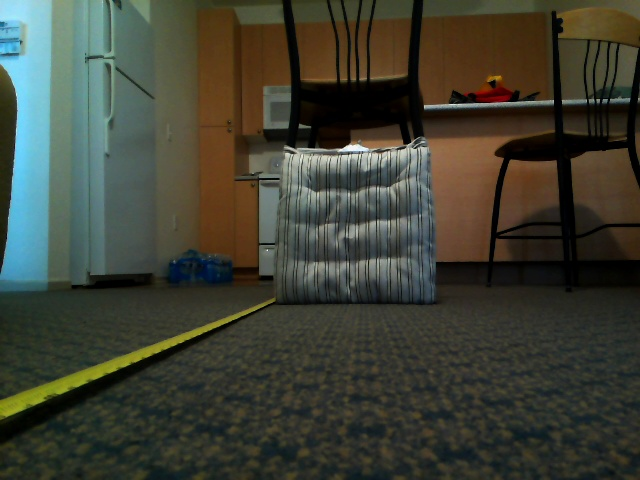
Images/Pillow/L_48.jpg
