dotimothy/TheDoPro/Images/Pillow/L_54.jpg

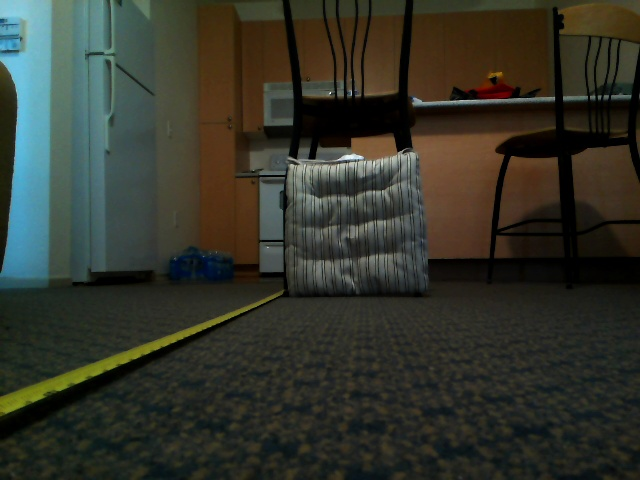
Images/Pillow/L_54.jpg
