dotimothy/TheDoPro/Images/Pillow/L_60.jpg

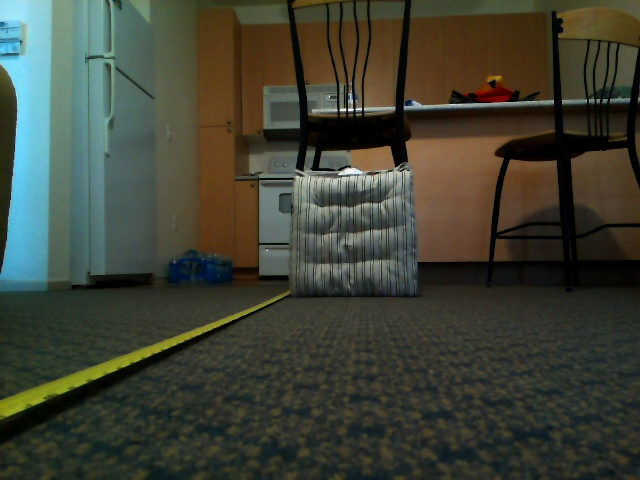
Images/Pillow/L_60.jpg
