dotimothy/TheDoPro/Images/Pillow/L_66.jpg

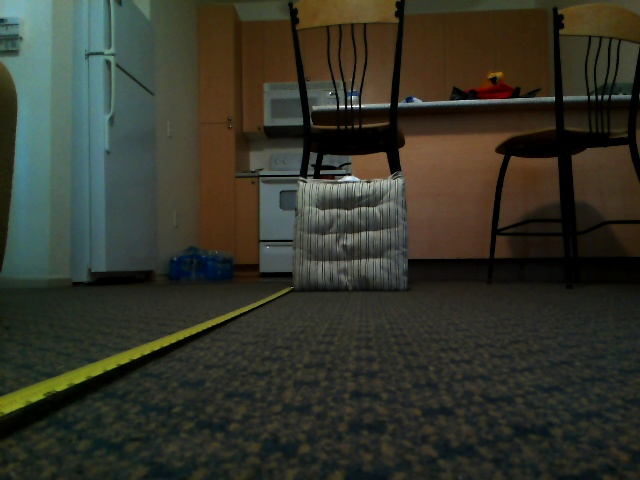
Images/Pillow/L_66.jpg
