dotimothy/TheDoPro/Images/Pillow/L_72.jpg

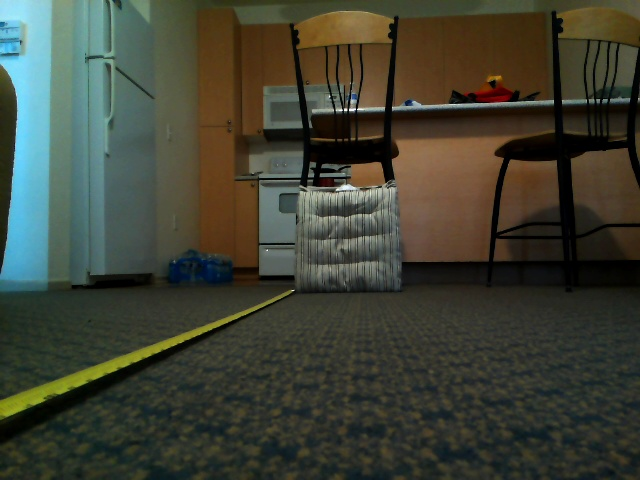
Images/Pillow/L_72.jpg
