dotimothy/TheDoPro/Images/Pillow/R_3.jpg

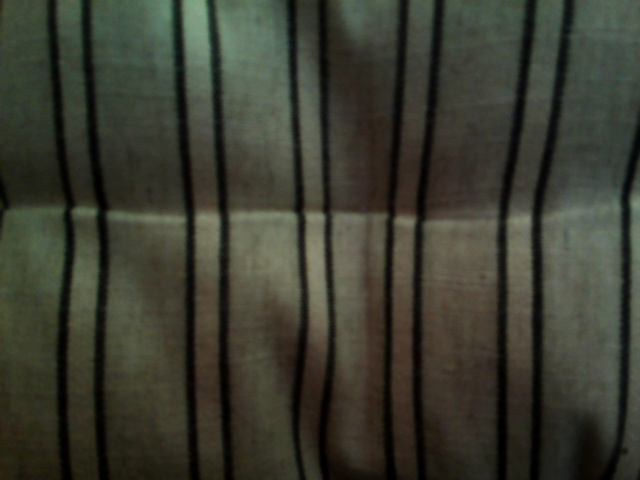
Images/Pillow/R_3.jpg
