dotimothy/TheDoPro/Images/Pillow/R_6.jpg

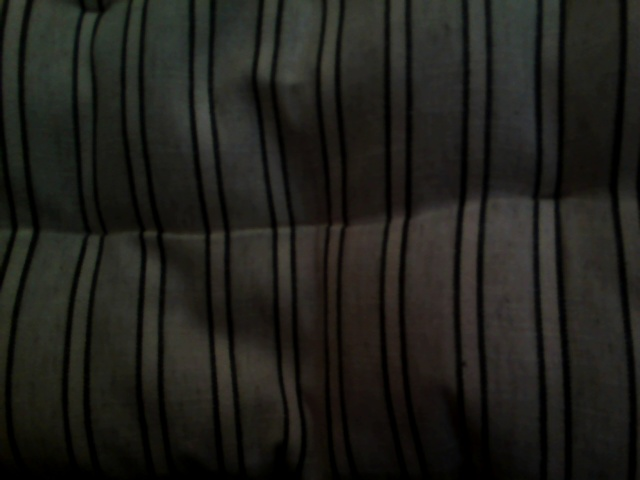
Images/Pillow/R_6.jpg
