dotimothy/TheDoPro/Images/Pillow/R_9.jpg

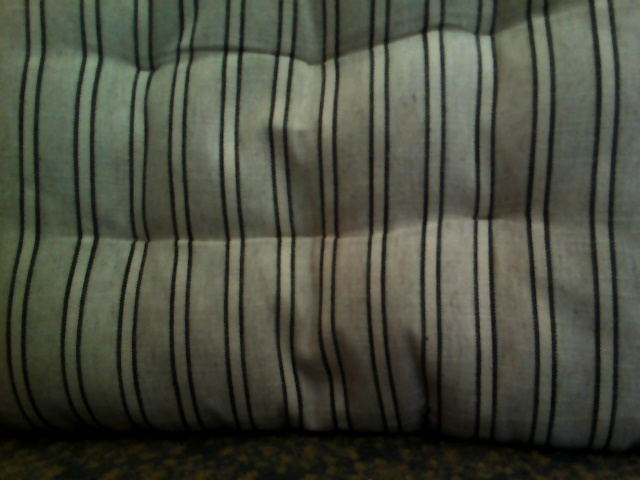
Images/Pillow/R_9.jpg
