dotimothy/TheDoPro/Images/Pillow/R_12.jpg

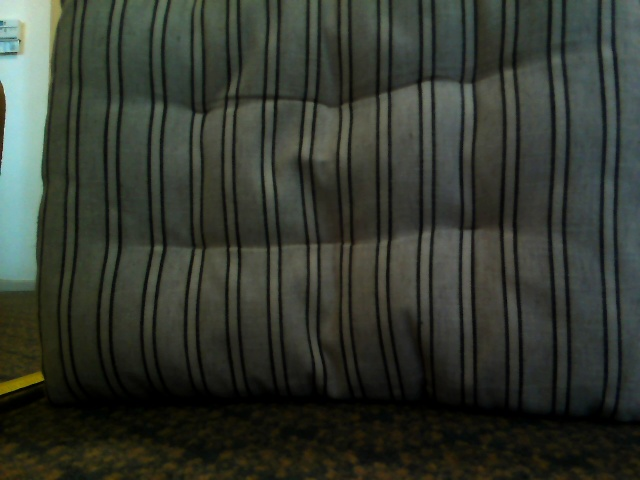
Images/Pillow/R_12.jpg
