dotimothy/TheDoPro/Images/Pillow/R_15.jpg

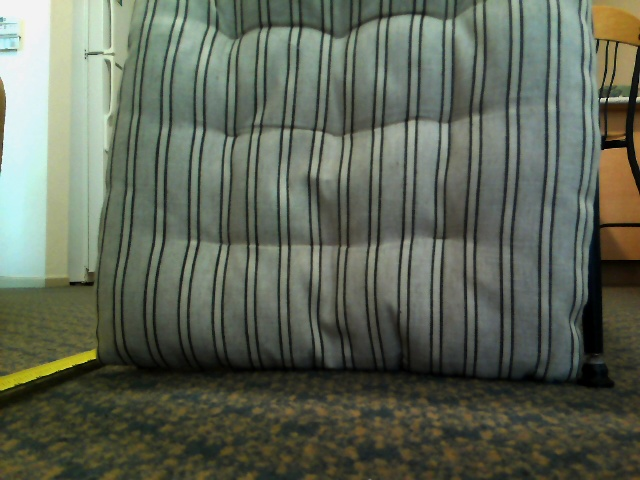
Images/Pillow/R_15.jpg
