dotimothy/TheDoPro/Images/Pillow/R_18.jpg

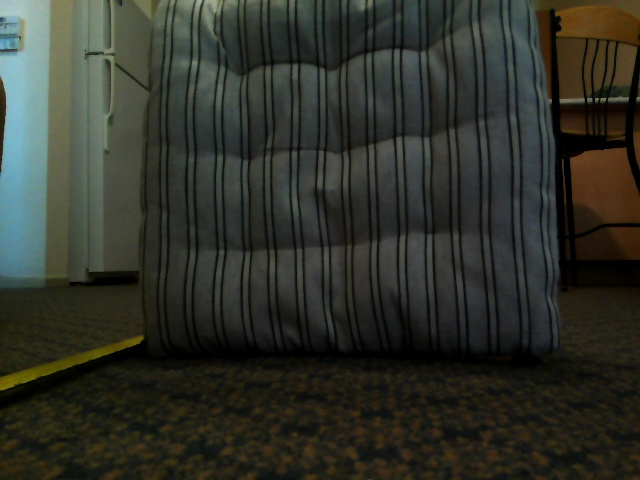
Images/Pillow/R_18.jpg
