dotimothy/TheDoPro/Images/Pillow/R_21.jpg

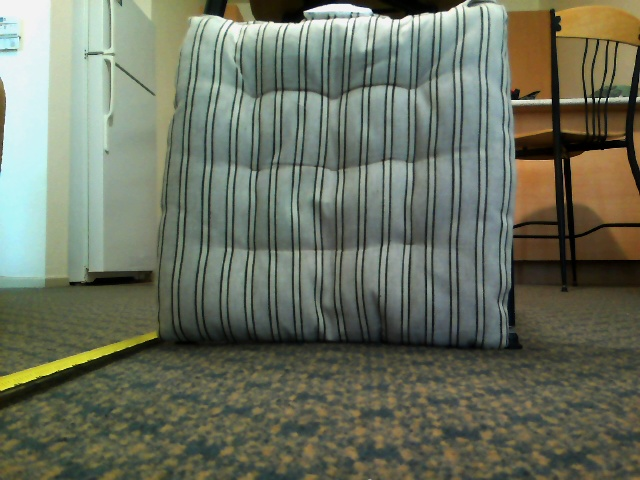
Images/Pillow/R_21.jpg
