dotimothy/TheDoPro/Images/Pillow/R_24.jpg

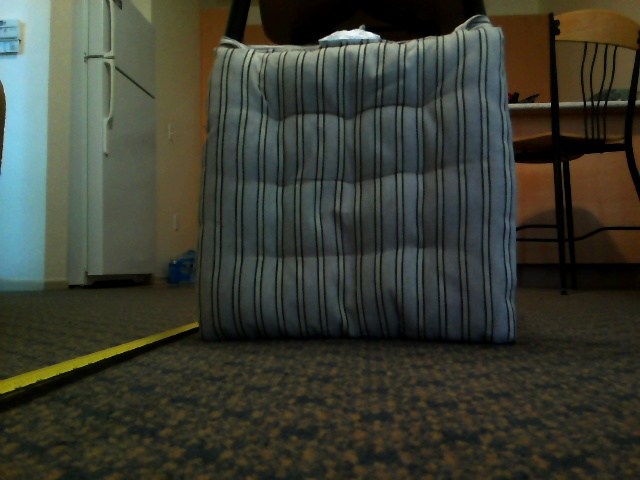
Images/Pillow/R_24.jpg
