dotimothy/TheDoPro/Images/Pillow/R_27.jpg

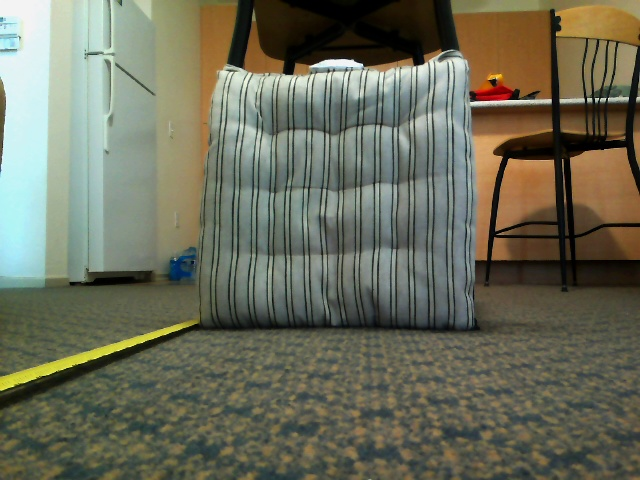
Images/Pillow/R_27.jpg
