dotimothy/TheDoPro/Images/Pillow/R_30.jpg

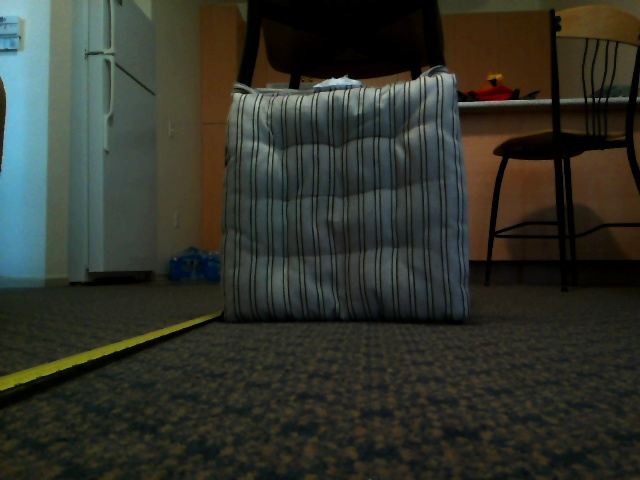
Images/Pillow/R_30.jpg
