dotimothy/TheDoPro/Images/Pillow/R_33.jpg

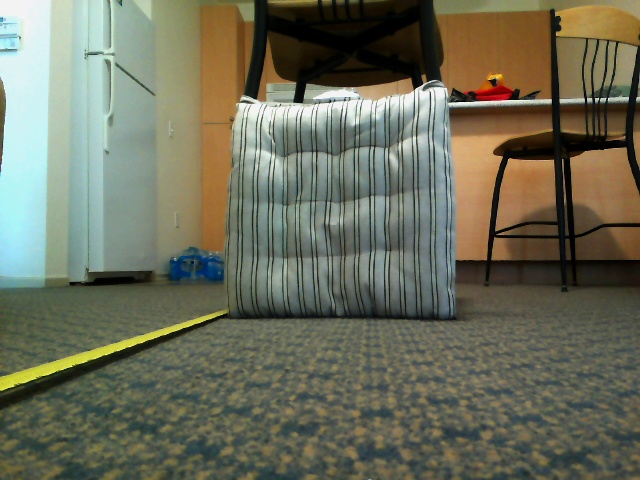
Images/Pillow/R_33.jpg
