dotimothy/TheDoPro/Images/Pillow/R_36.jpg

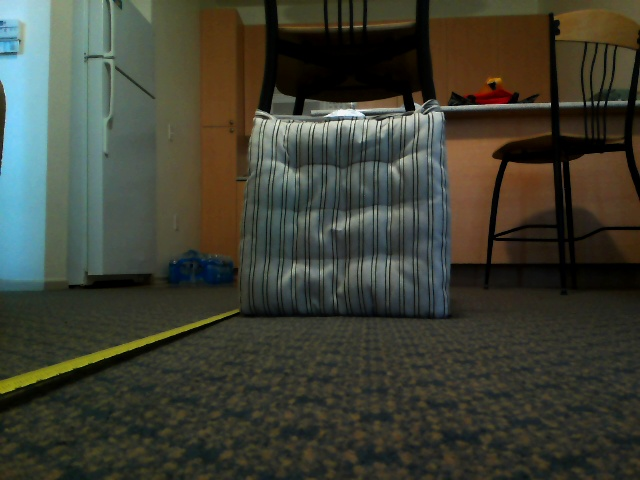
Images/Pillow/R_36.jpg
