dotimothy/TheDoPro/Images/Pillow/R_39.jpg

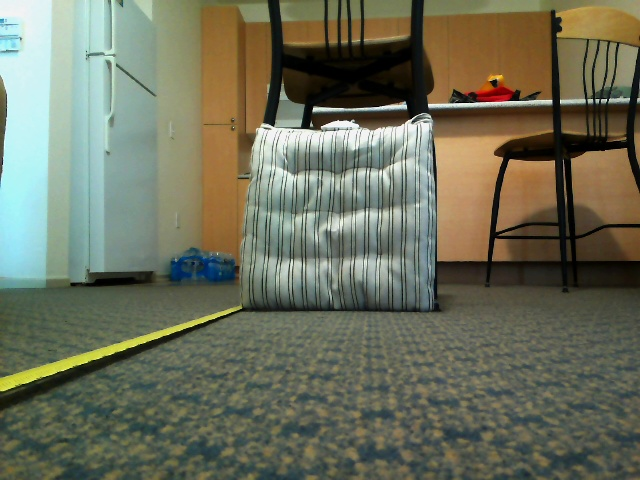
Images/Pillow/R_39.jpg
