dotimothy/TheDoPro/Images/Pillow/R_42.jpg

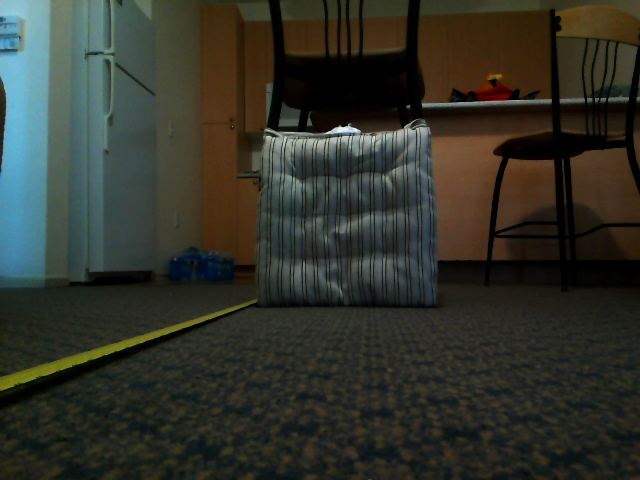
Images/Pillow/R_42.jpg
