dotimothy/TheDoPro/Images/Pillow/R_45.jpg

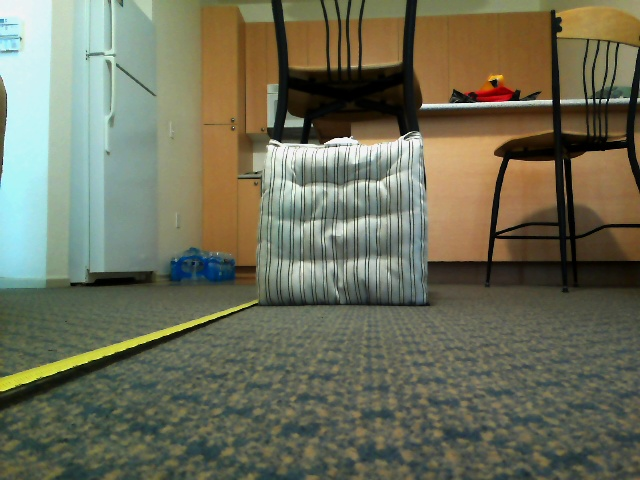
Images/Pillow/R_45.jpg
