dotimothy/TheDoPro/Images/Pillow/R_48.jpg

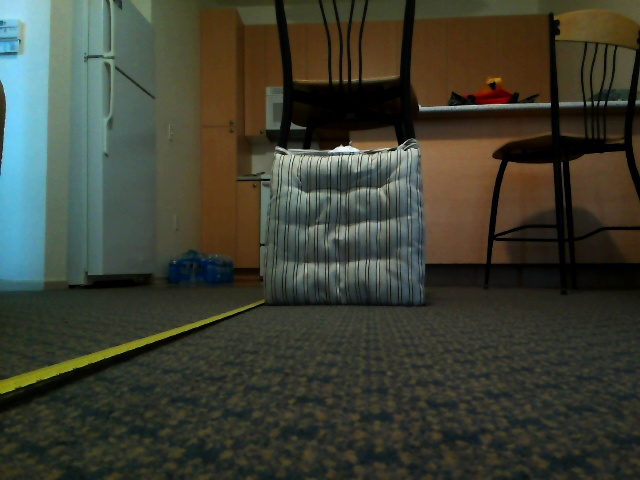
Images/Pillow/R_48.jpg
