dotimothy/TheDoPro/Images/Pillow/R_54.jpg

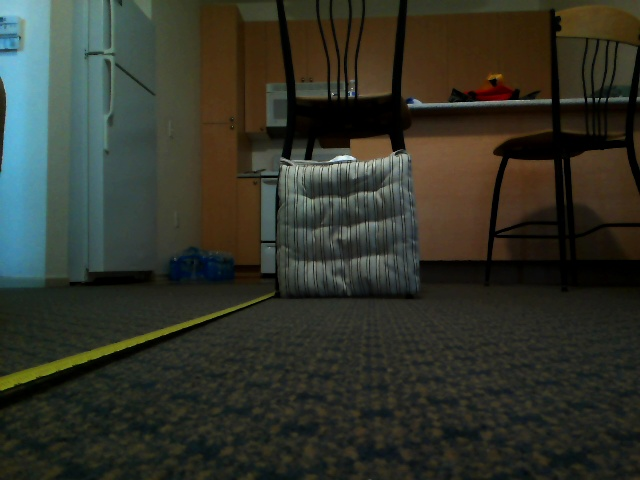
Images/Pillow/R_54.jpg
