dotimothy/TheDoPro/Images/Pillow/R_60.jpg

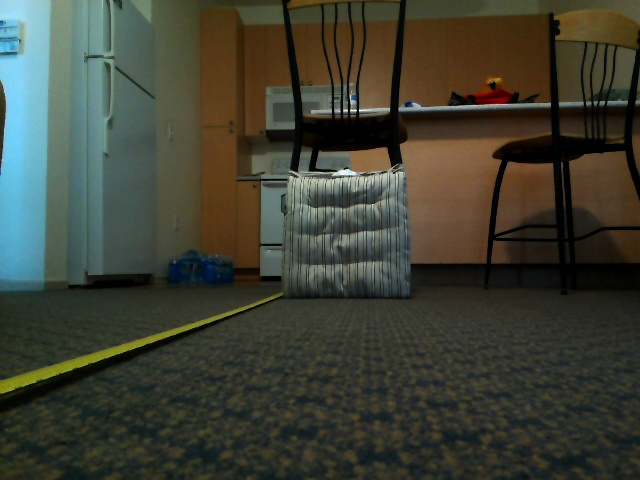
Images/Pillow/R_60.jpg
