dotimothy/TheDoPro/Images/Pillow/R_66.jpg

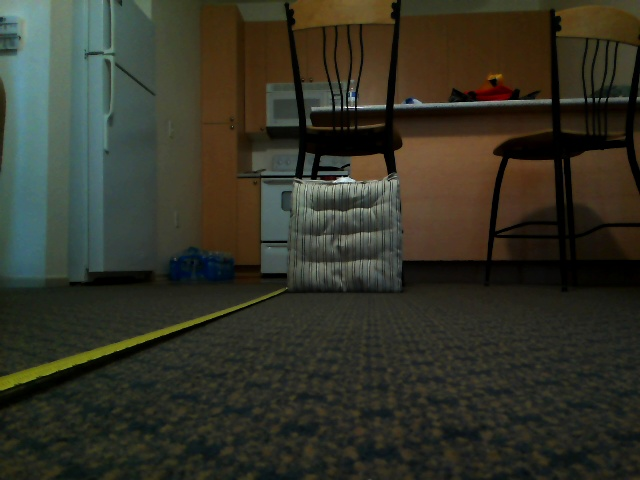
Images/Pillow/R_66.jpg
