dotimothy/TheDoPro/Images/Pillow/R_72.jpg

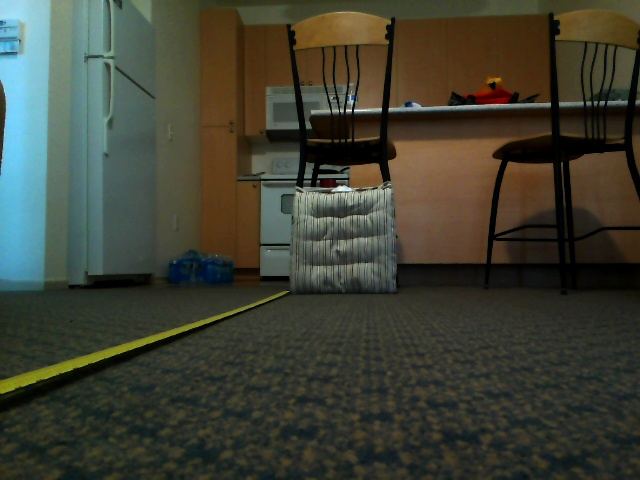
Images/Pillow/R_72.jpg
