dotimothy/TheDoPro/Images/Pillow/Scan_256/D_3.jpg

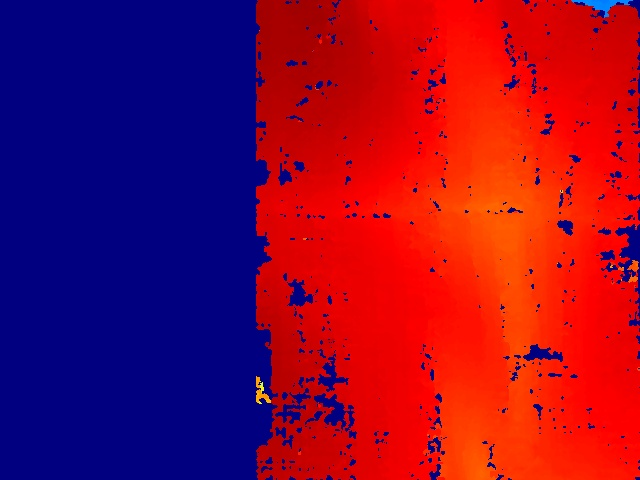
Images/Pillow/Scan_256/D_3.jpg
