dotimothy/TheDoPro/Images/Pillow/Scan_256/D_6.jpg

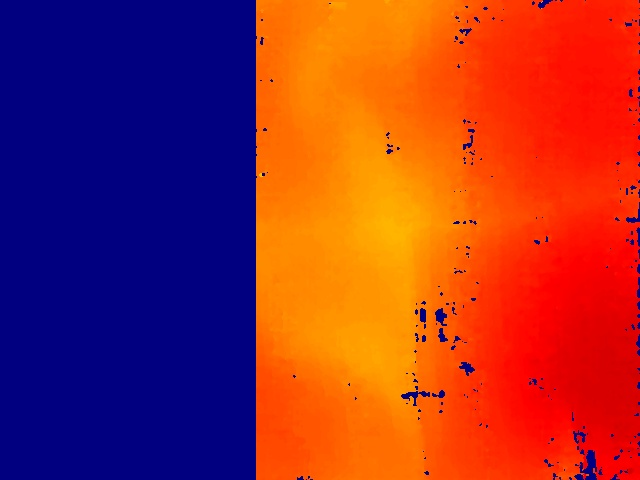
Images/Pillow/Scan_256/D_6.jpg
