dotimothy/TheDoPro/Images/Pillow/Scan_256/D_9.jpg

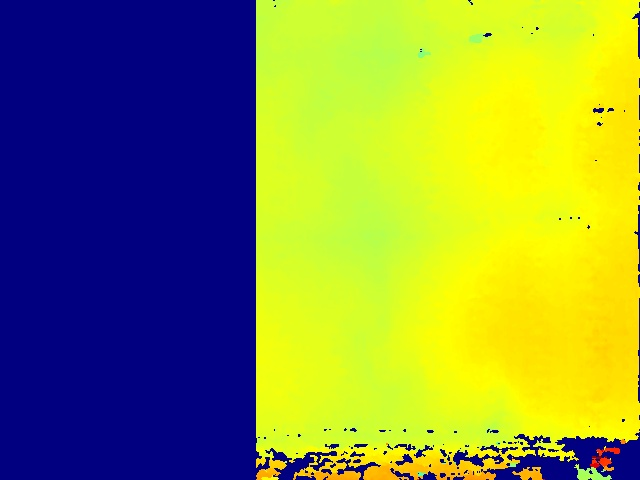
Images/Pillow/Scan_256/D_9.jpg
