dotimothy/TheDoPro/Images/Pillow/Scan_256/D_15.jpg

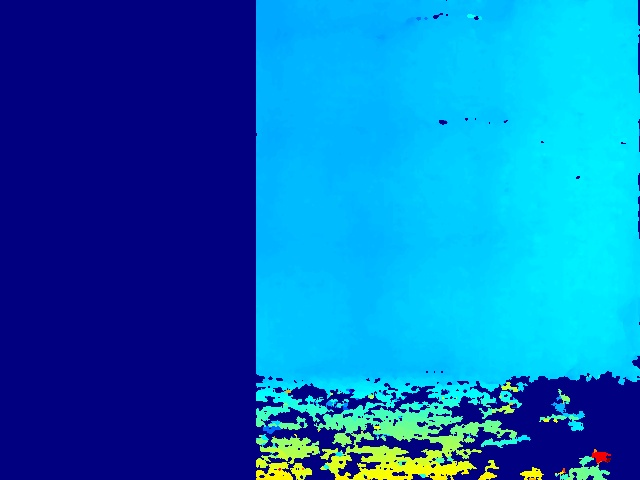
Images/Pillow/Scan_256/D_15.jpg
