dotimothy/TheDoPro/Images/Pillow/Scan_256/D_18.jpg

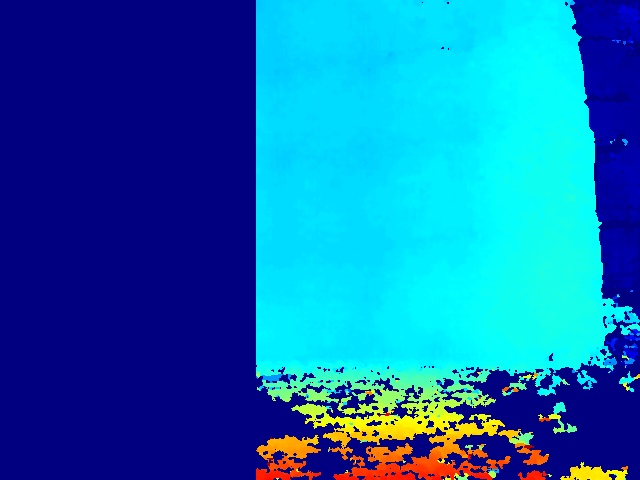
Images/Pillow/Scan_256/D_18.jpg
