dotimothy/TheDoPro/Images/Pillow/Scan_256/D_21.jpg

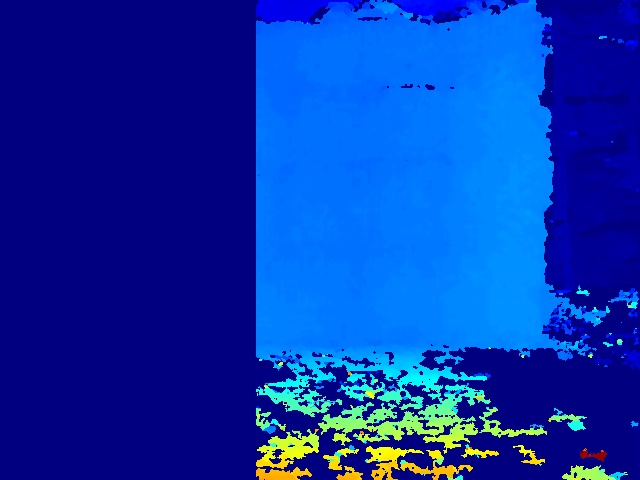
Images/Pillow/Scan_256/D_21.jpg
