dotimothy/TheDoPro/Images/Pillow/Scan_256/D_27.jpg

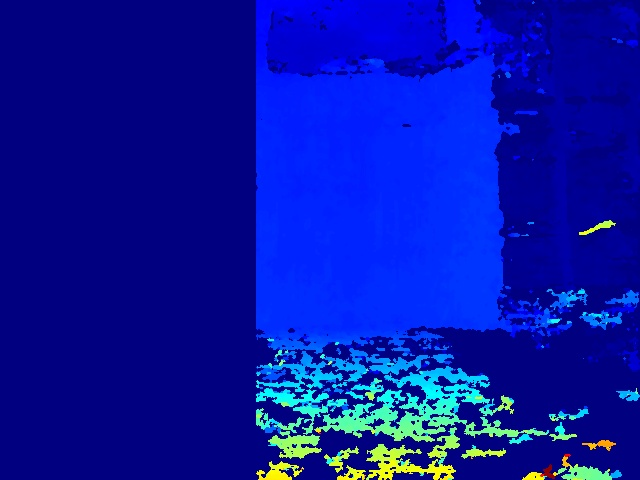
Images/Pillow/Scan_256/D_27.jpg
