dotimothy/TheDoPro/Images/Pillow/Scan_256/D_30.jpg

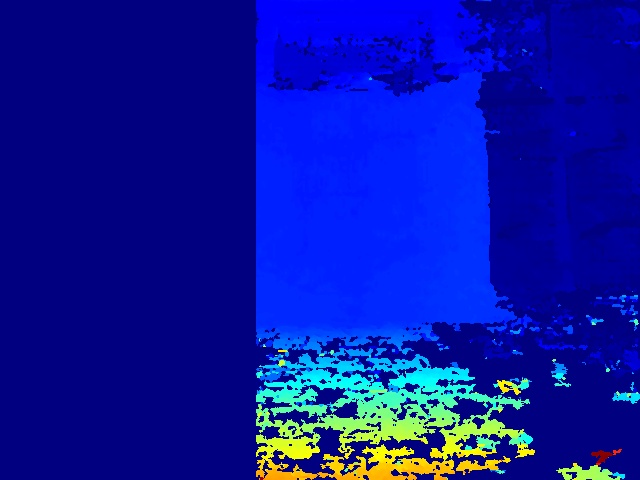
Images/Pillow/Scan_256/D_30.jpg
