dotimothy/TheDoPro/Images/Pillow/Scan_256/D_33.jpg

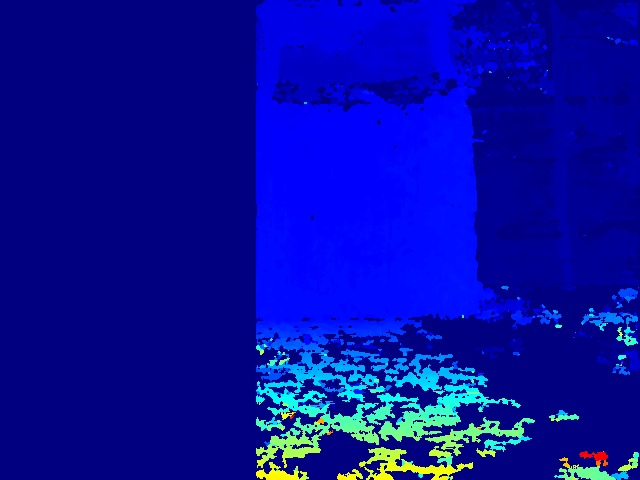
Images/Pillow/Scan_256/D_33.jpg
