dotimothy/TheDoPro/Images/Pillow/Scan_256/D_36.jpg

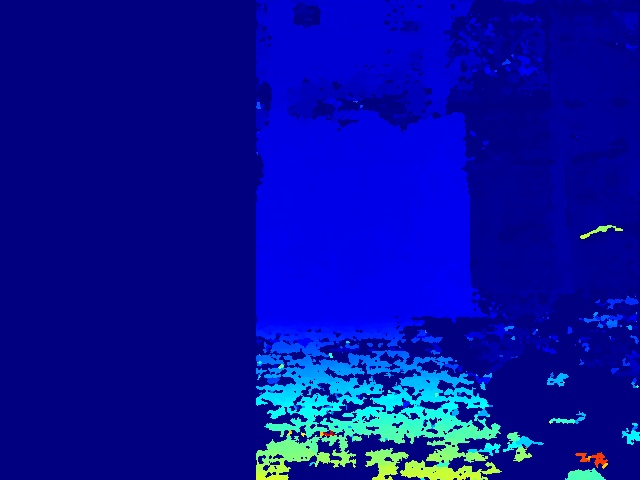
Images/Pillow/Scan_256/D_36.jpg
