dotimothy/TheDoPro/Images/Pillow/Scan_256/D_45.jpg

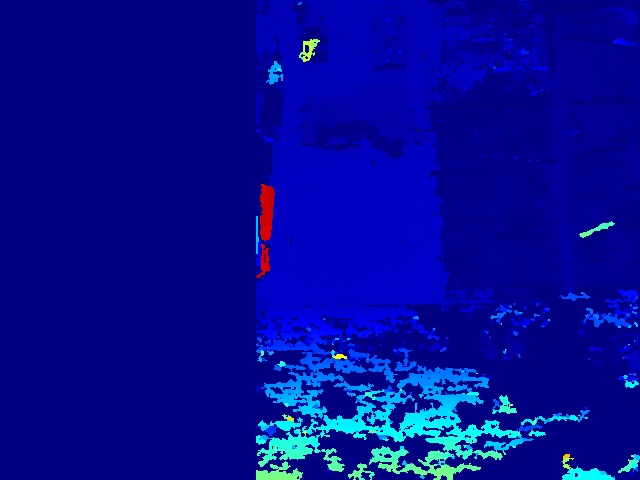
Images/Pillow/Scan_256/D_45.jpg
