dotimothy/TheDoPro/Images/Pillow/Scan_256/D_54.jpg

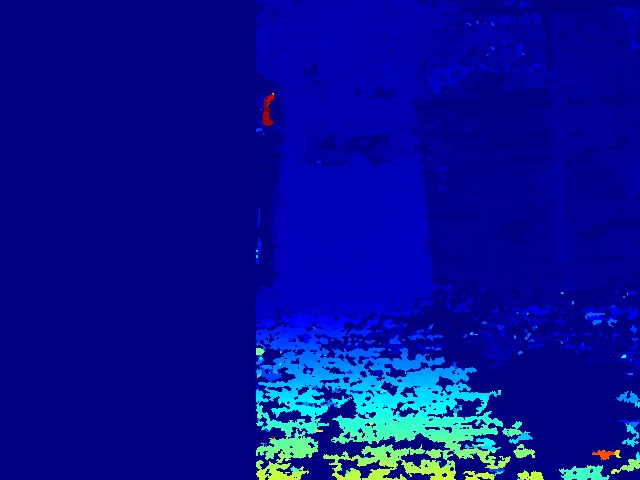
Images/Pillow/Scan_256/D_54.jpg
