dotimothy/TheDoPro/Images/Pillow/Scan_256/D_BM_3.jpg

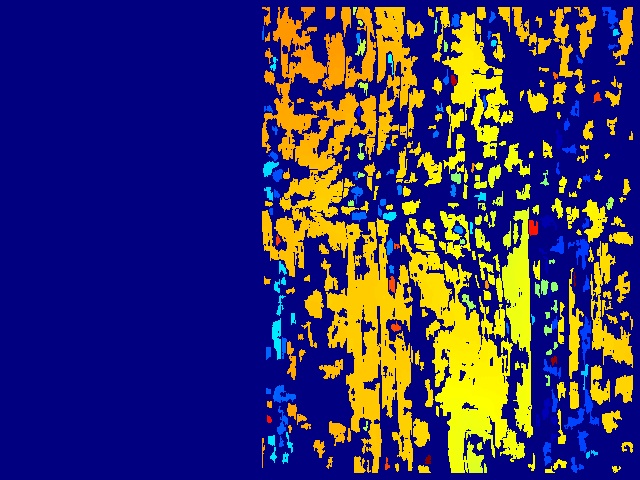
Images/Pillow/Scan_256/D_BM_3.jpg
