dotimothy/TheDoPro/Images/Pillow/Scan_256/D_BM_9.jpg

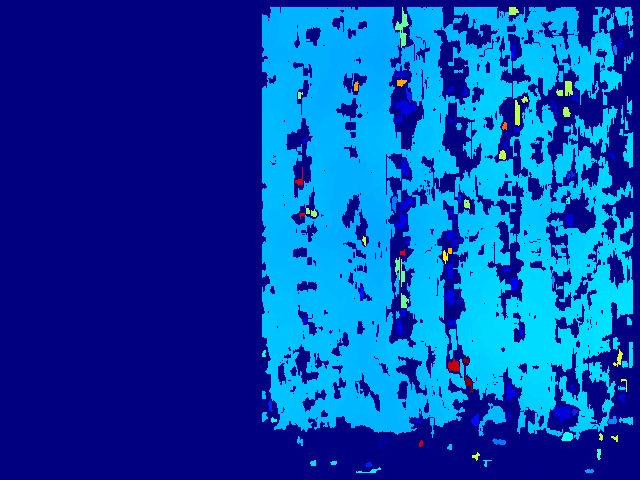
Images/Pillow/Scan_256/D_BM_9.jpg
