dotimothy/TheDoPro/Images/Pillow/Scan_256/D_BM_12.jpg

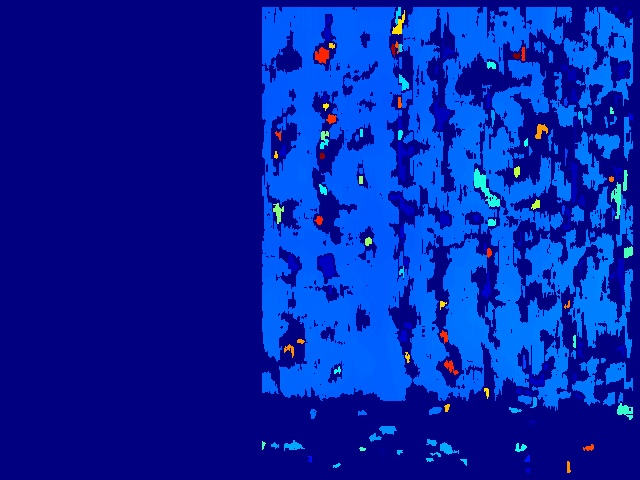
Images/Pillow/Scan_256/D_BM_12.jpg
