dotimothy/TheDoPro/Images/Pillow/Scan_256/D_BM_18.jpg

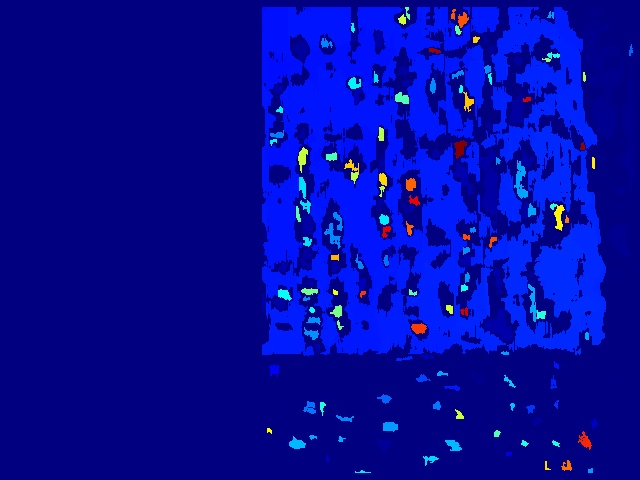
Images/Pillow/Scan_256/D_BM_18.jpg
