dotimothy/TheDoPro/Images/Pillow/Scan_256/D_BM_24.jpg

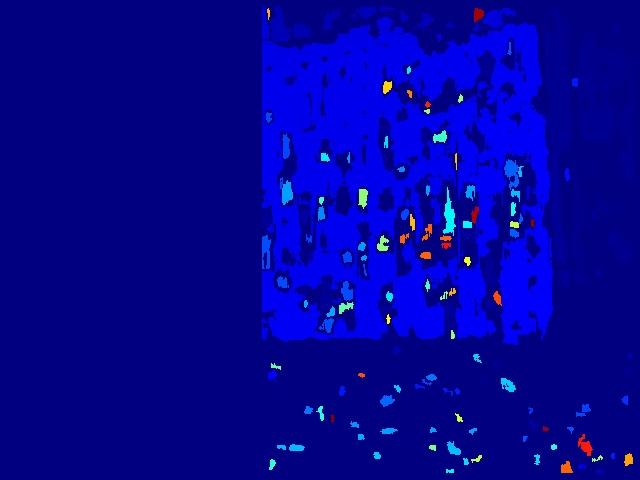
Images/Pillow/Scan_256/D_BM_24.jpg
