dotimothy/TheDoPro/Images/Pillow/Scan_256/D_BM_30.jpg

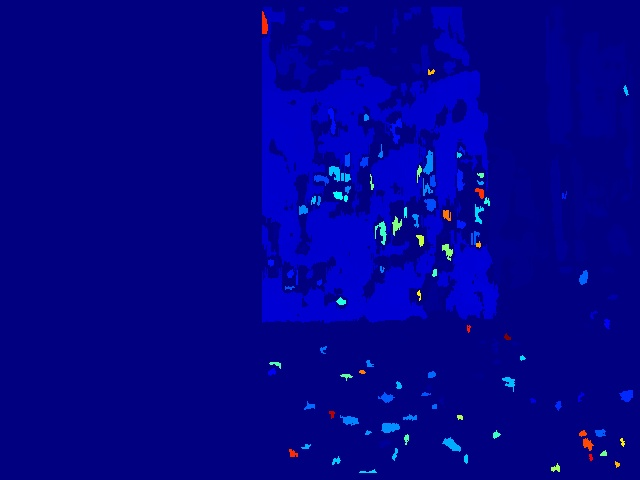
Images/Pillow/Scan_256/D_BM_30.jpg
