dotimothy/TheDoPro/Images/Pillow/Scan_256/D_BM_33.jpg

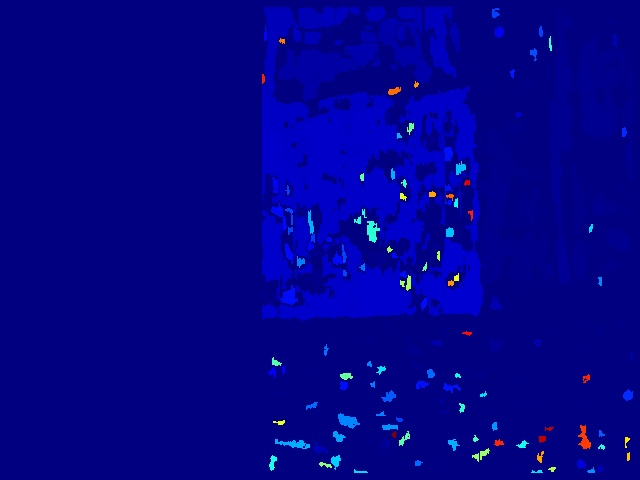
Images/Pillow/Scan_256/D_BM_33.jpg
