dotimothy/TheDoPro/Images/Pillow/Scan_256/D_BM_36.jpg

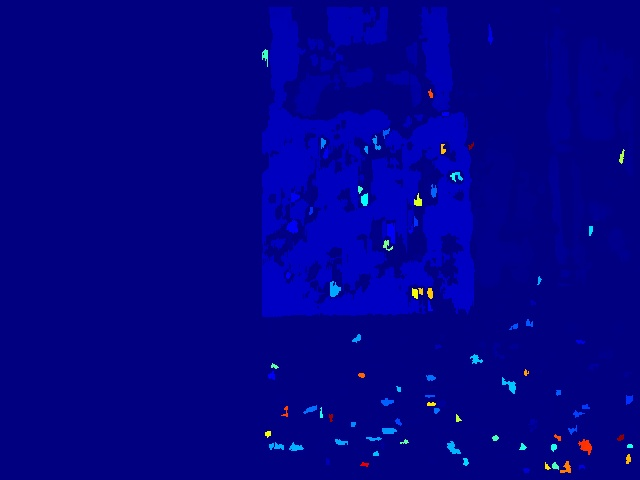
Images/Pillow/Scan_256/D_BM_36.jpg
