dotimothy/TheDoPro/Images/Pillow/Scan_256/D_BM_39.jpg

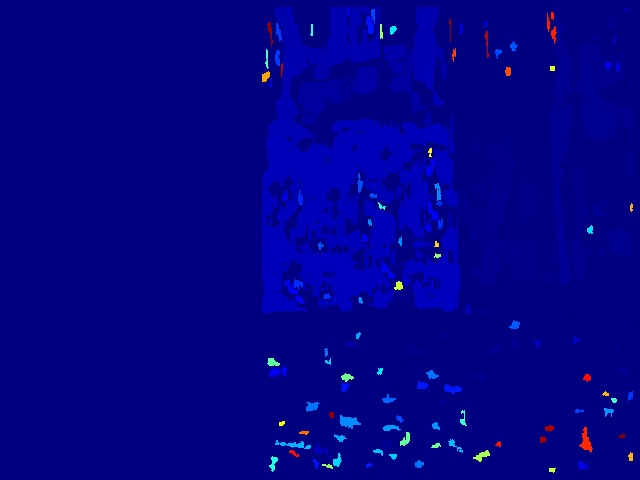
Images/Pillow/Scan_256/D_BM_39.jpg
