dotimothy/TheDoPro/Images/Pillow/Scan_256/D_BM_42.jpg

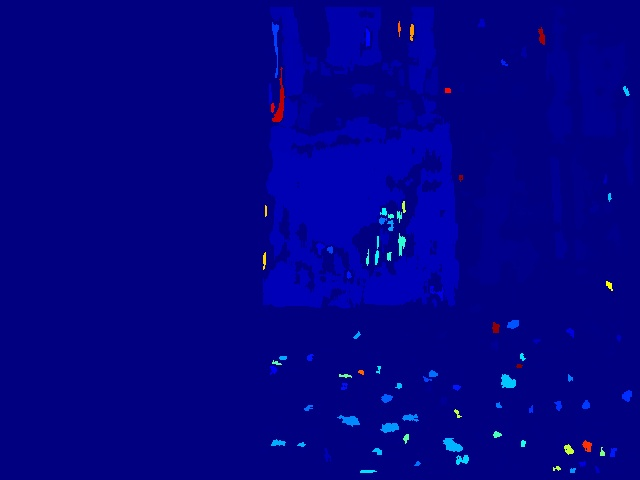
Images/Pillow/Scan_256/D_BM_42.jpg
