dotimothy/TheDoPro/Images/Pillow/Scan_256/D_BM_45.jpg

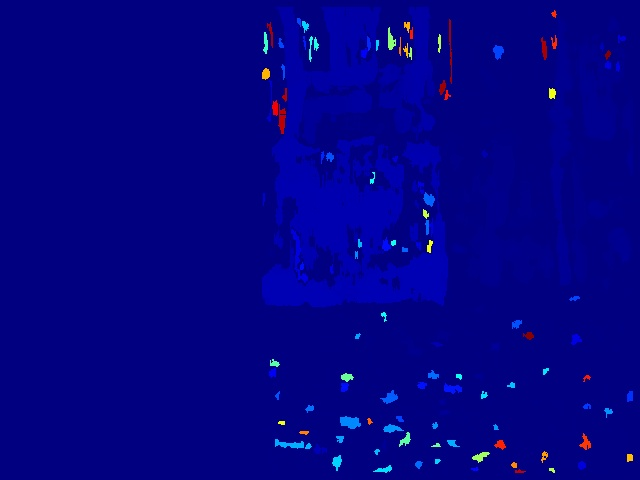
Images/Pillow/Scan_256/D_BM_45.jpg
