dotimothy/TheDoPro/Images/Pillow/Scan_256/D_BM_48.jpg

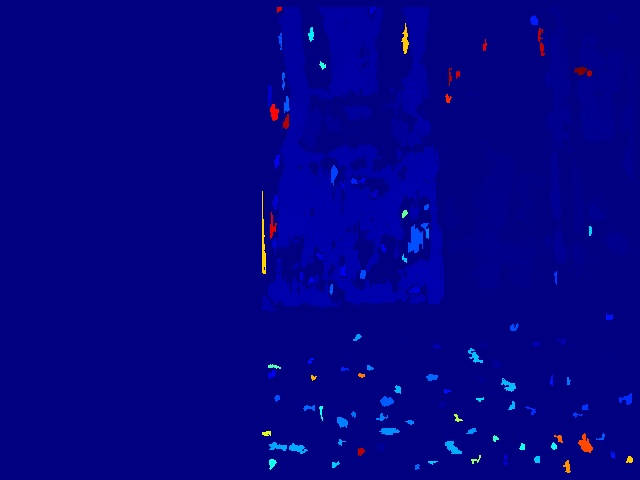
Images/Pillow/Scan_256/D_BM_48.jpg
