dotimothy/TheDoPro/Images/Pillow/Scan_256/D_BM_54.jpg

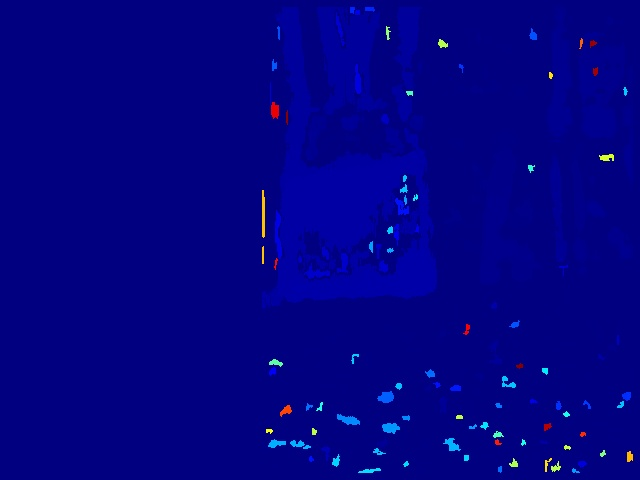
Images/Pillow/Scan_256/D_BM_54.jpg
