dotimothy/TheDoPro/Images/Pillow/Scan_256/D_BM_60.jpg

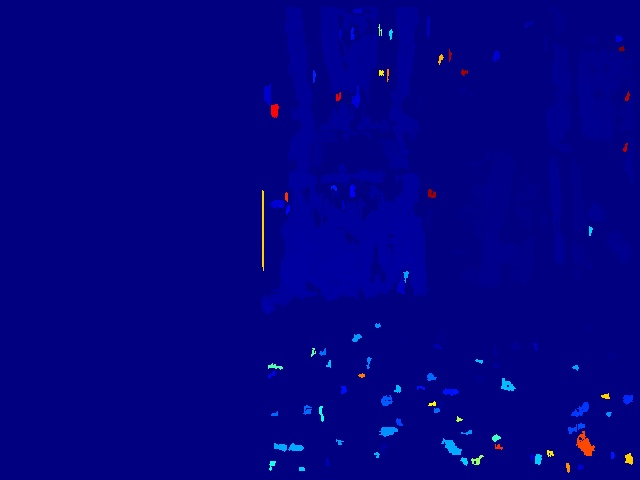
Images/Pillow/Scan_256/D_BM_60.jpg
