dotimothy/TheDoPro/Images/Pillow/Scan_256/D_BM_66.jpg

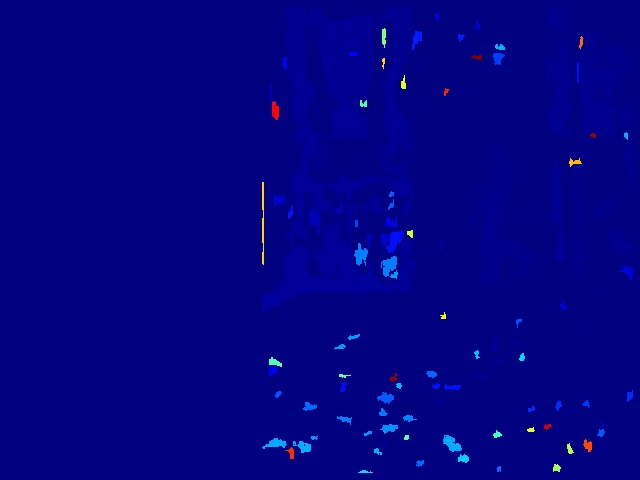
Images/Pillow/Scan_256/D_BM_66.jpg
