dotimothy/TheDoPro/Images/Pillow/Scan_256/D_BM_72.jpg

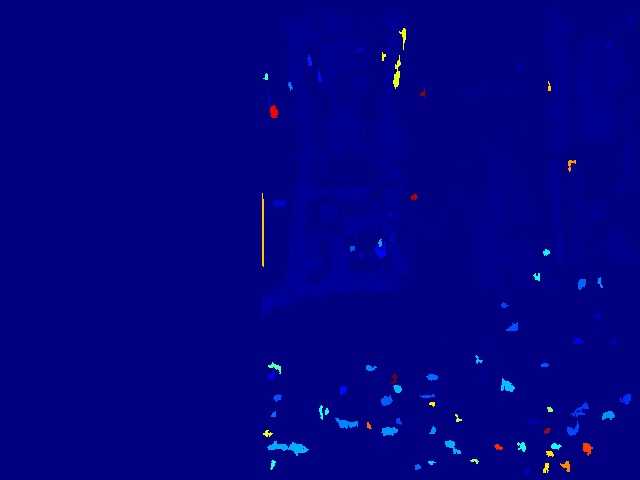
Images/Pillow/Scan_256/D_BM_72.jpg
