dotimothy/TheDoPro/Images/Pillow/Scan_256/D_SGBM_21.jpg

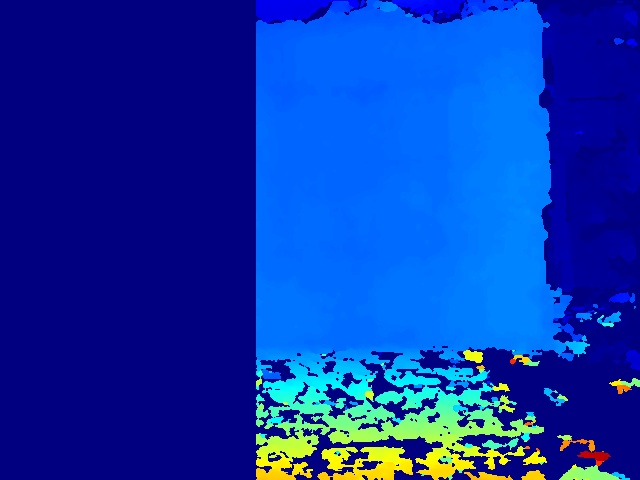
Images/Pillow/Scan_256/D_SGBM_21.jpg
