dotimothy/TheDoPro/Images/Pillow/Scan_256/D_SGBM_30.jpg

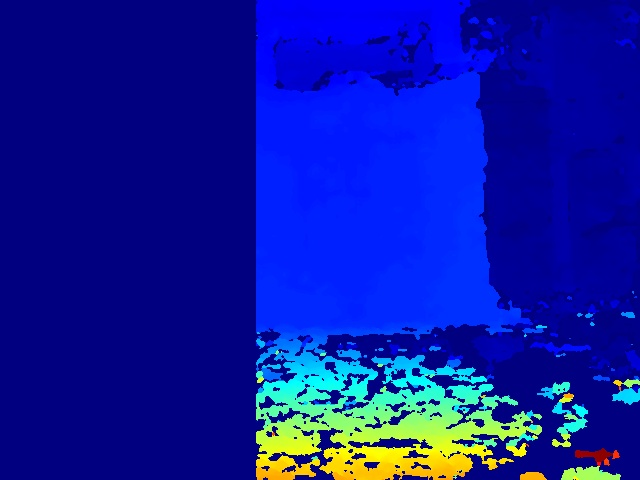
Images/Pillow/Scan_256/D_SGBM_30.jpg
