dotimothy/TheDoPro/Images/Pillow/Scan_256/D_SGBM_33.jpg

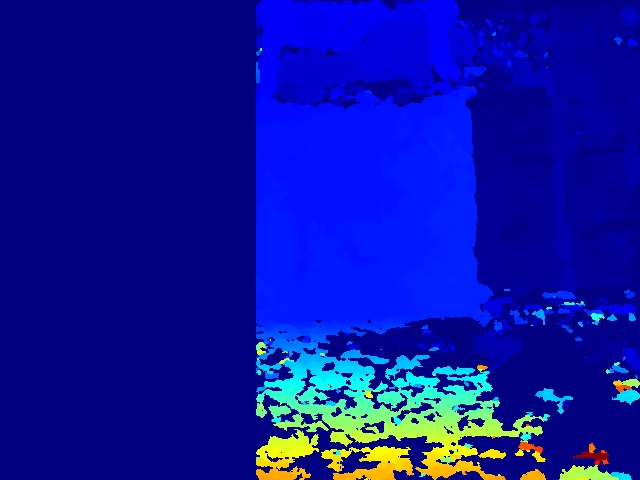
Images/Pillow/Scan_256/D_SGBM_33.jpg
