dotimothy/TheDoPro/Images/Pillow/Scan_256/D_SGBM_39.jpg

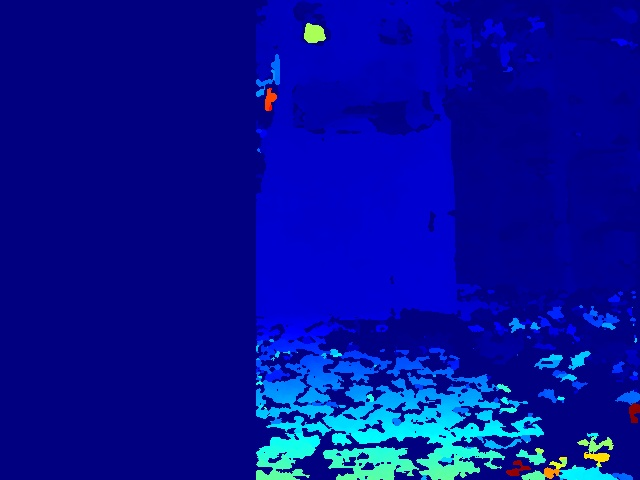
Images/Pillow/Scan_256/D_SGBM_39.jpg
