dotimothy/TheDoPro/Images/Pillow/Scan_256/D_SGBM_42.jpg

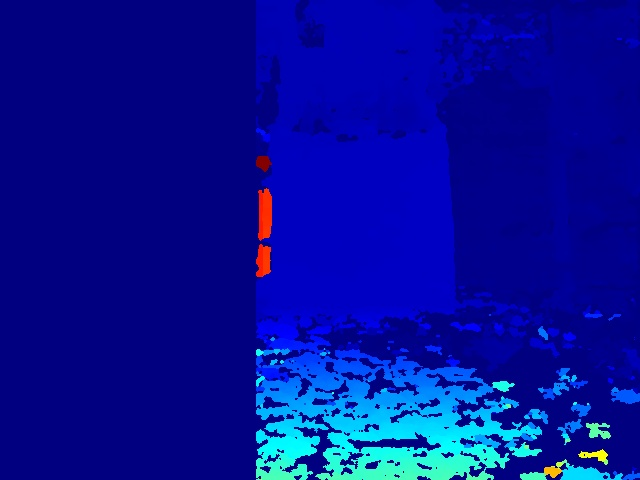
Images/Pillow/Scan_256/D_SGBM_42.jpg
