dotimothy/TheDoPro/Images/Pillow/Scan_256/D_SGBM_45.jpg

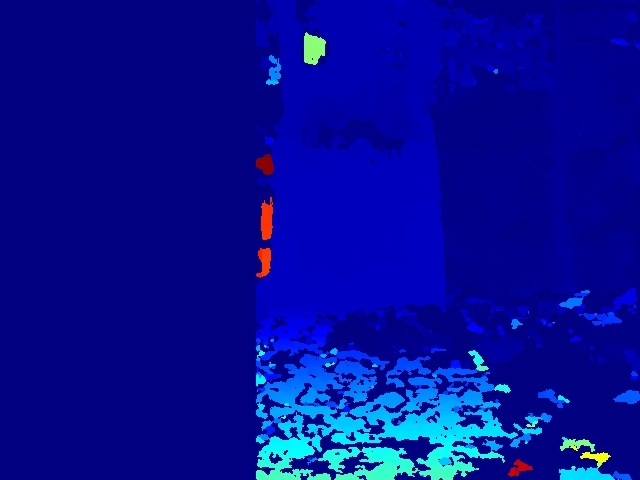
Images/Pillow/Scan_256/D_SGBM_45.jpg
