dotimothy/TheDoPro/Images/Pillow/Scan_256/D_SGBM_48.jpg

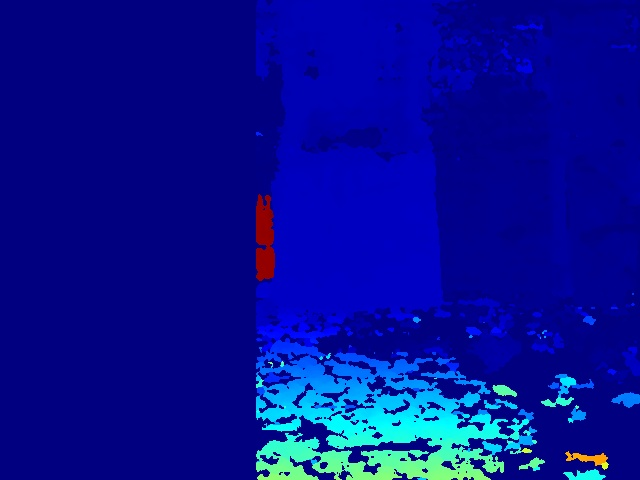
Images/Pillow/Scan_256/D_SGBM_48.jpg
