dotimothy/TheDoPro/Images/Pillow/Scan_256/D_SGBM_60.jpg

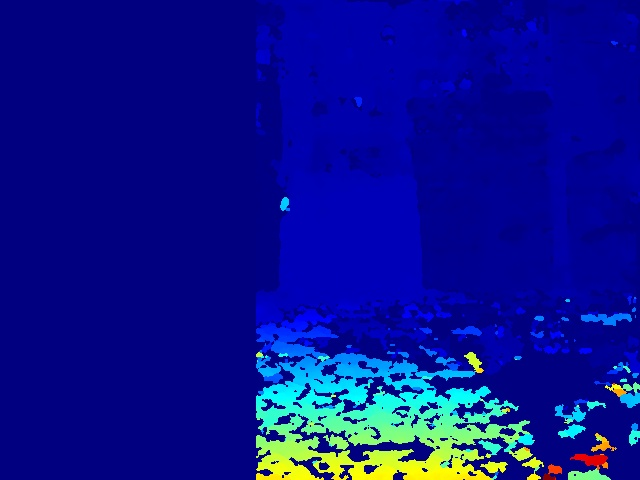
Images/Pillow/Scan_256/D_SGBM_60.jpg
