dotimothy/TheDoPro/Images/Pillow/Scan_256/D_SGBM_66.jpg

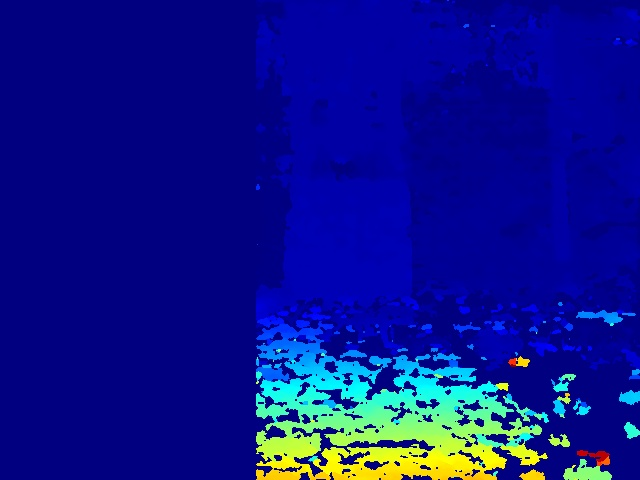
Images/Pillow/Scan_256/D_SGBM_66.jpg
