dotimothy/TheDoPro/Images/Pillow/Scan_256/D_SGBM_72.jpg

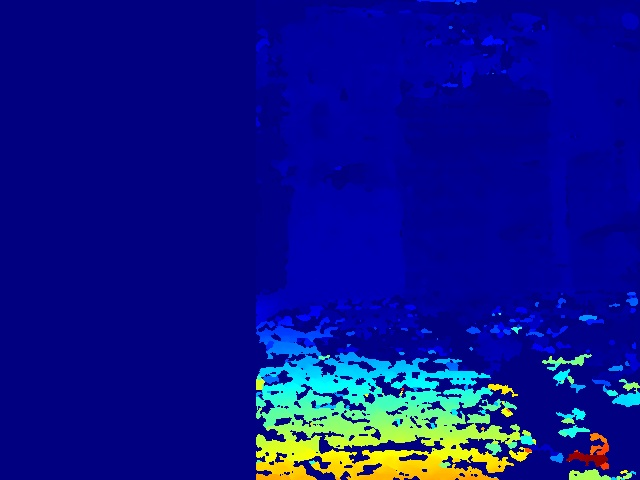
Images/Pillow/Scan_256/D_SGBM_72.jpg
