dotimothy/TheDoPro/Images/R_25.png

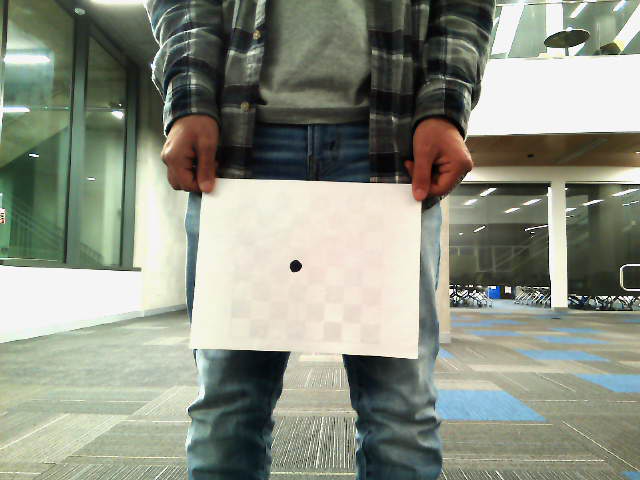
Images/R_25.png
