dotimothy/TheDoPro/Images/R_50.png

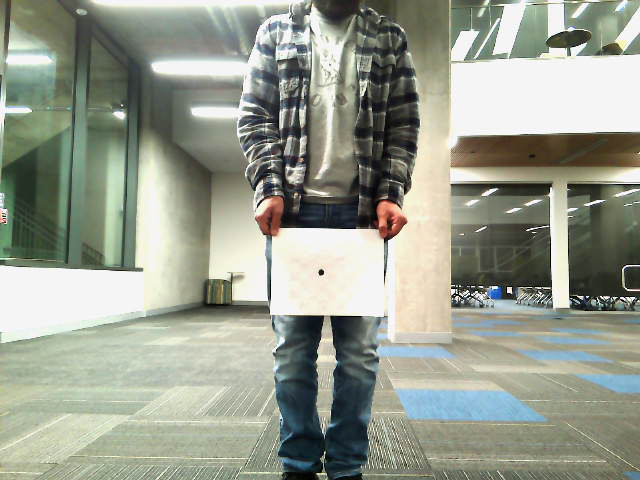
Images/R_50.png
