dotimothy/TheDoPro/Images/R_75.png

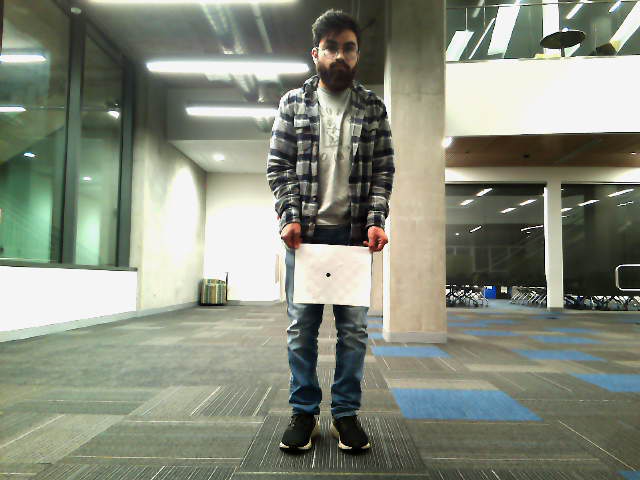
Images/R_75.png
