dotimothy/TheDoPro/Images/R_100.png

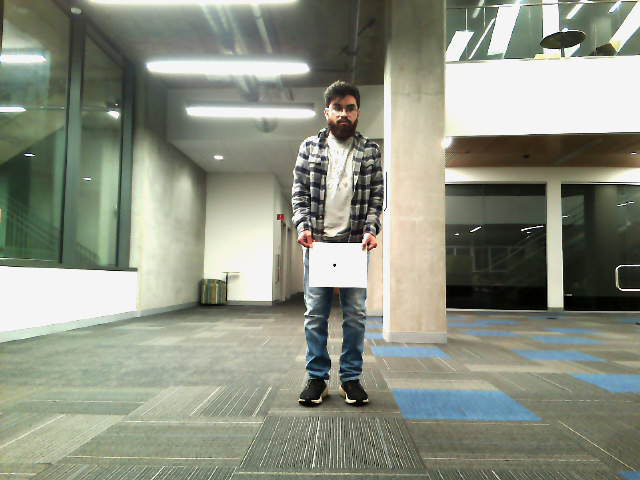
Images/R_100.png
