dotimothy/TheDoPro/Images/R_200.png

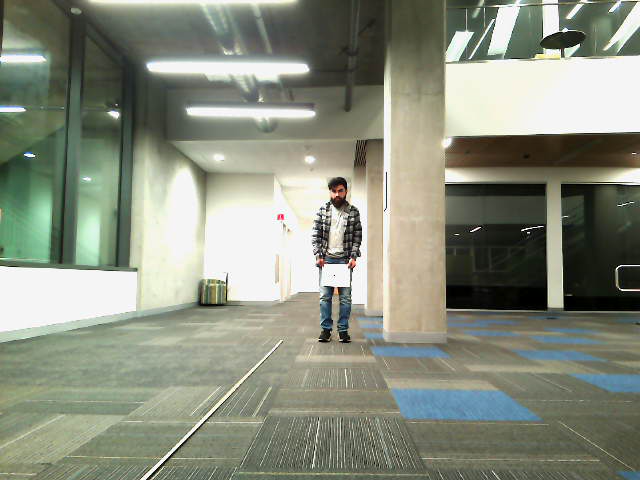
Images/R_200.png
