dotimothy/TheDoPro/Images/R_v2_25.png

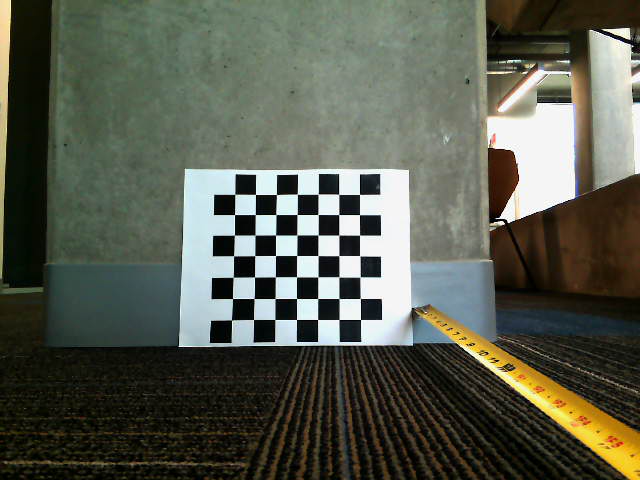
Images/R_v2_25.png
