dotimothy/TheDoPro/Images/R_v2_50.png

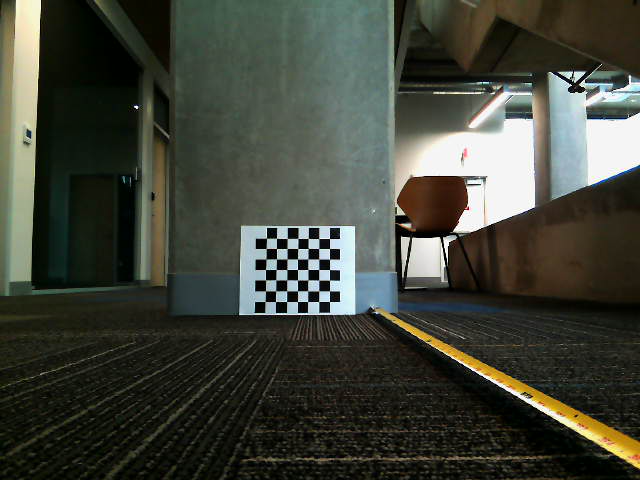
Images/R_v2_50.png
