dotimothy/TheDoPro/Images/R_v2_75.png

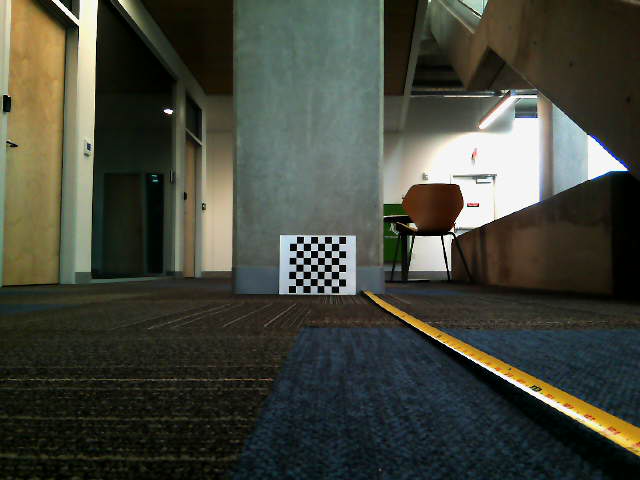
Images/R_v2_75.png
