dotimothy/TheDoPro/Images/R_v2_100.png

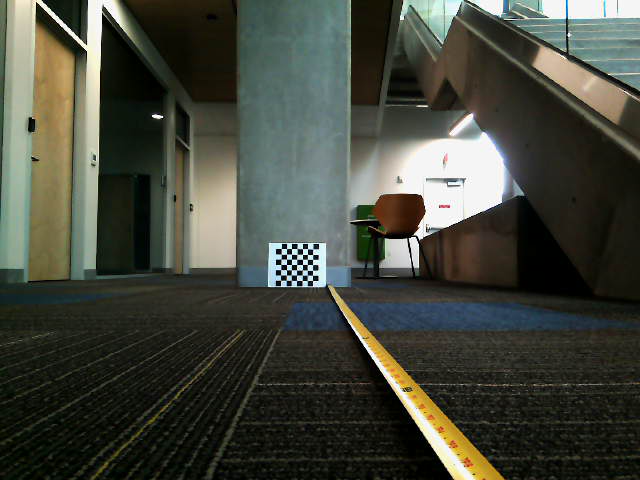
Images/R_v2_100.png
