dotimothy/TheDoPro/Images/right_piano_GT.jpg

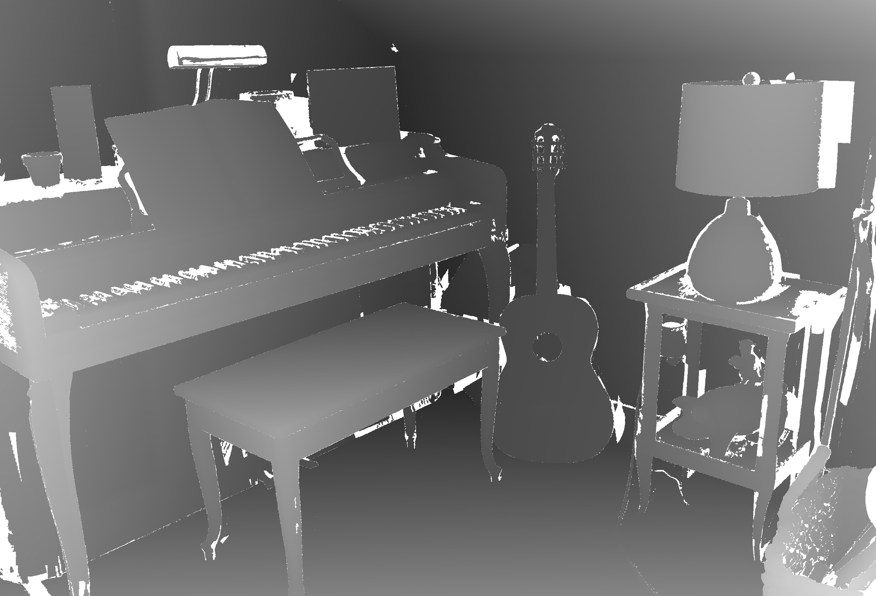
Images/right_piano_GT.jpg
