dotimothy/TheDoPro/Images/TheDoPro.jpg

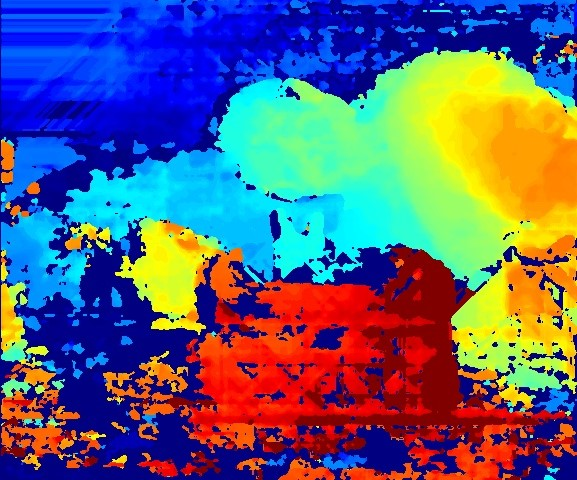
Images/TheDoPro.jpg
