dotimothy/TheDoPro/Vision/cluster.png

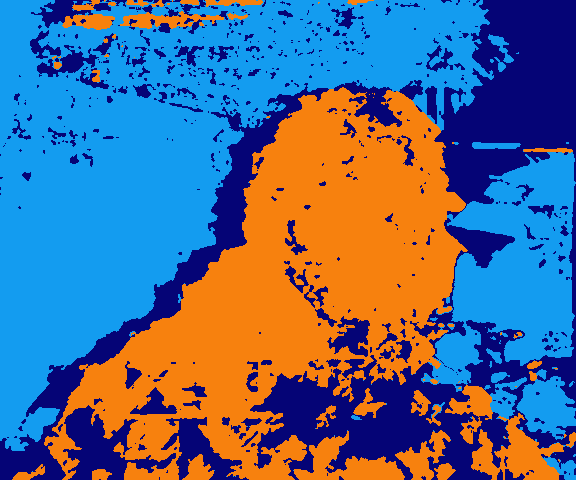
Vision/cluster.png
