dotimothy/TheDoPro/Vision/cropped.png

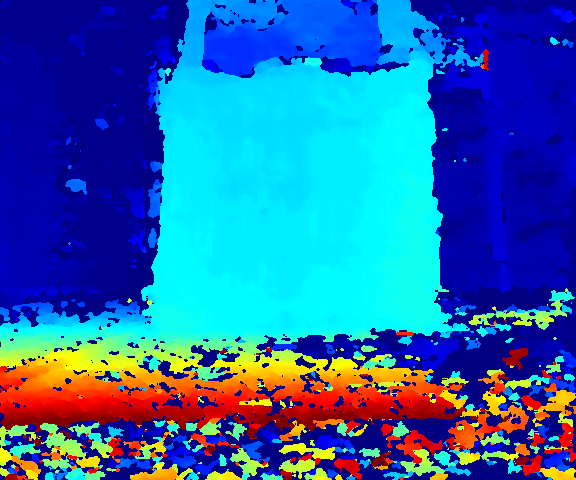
Vision/cropped.png
