dotimothy/TheDoPro/Vision/disp.jpg

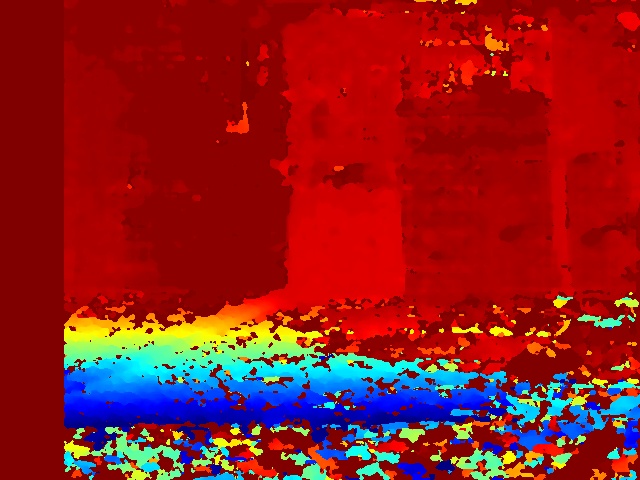
Vision/disp.jpg
