dotimothy/TheDoPro/Vision/left.jpg

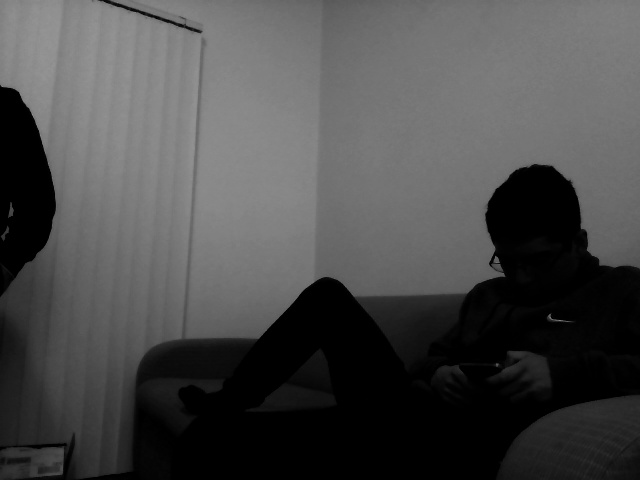
Vision/left.jpg
