dotimothy/TheDoPro/CAD/Winter Quarter/Mid_Plate.stl

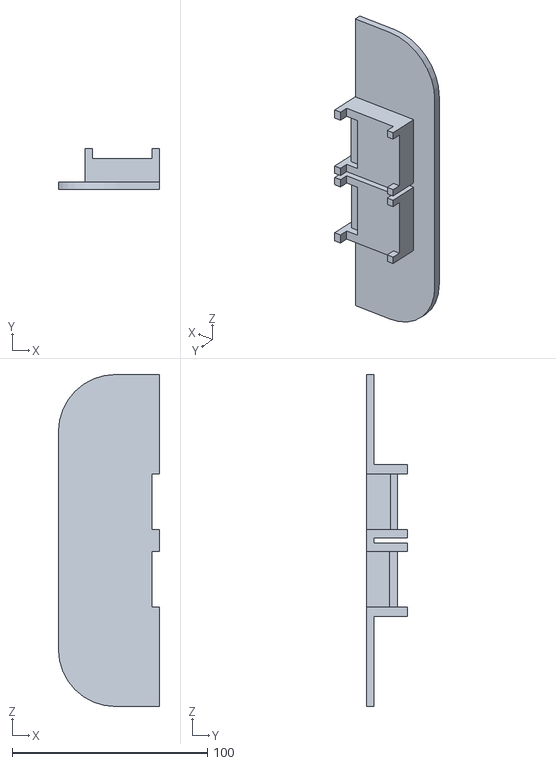
[picture p230: CAD file, 2023-03-17]
CAD/Winter Quarter/Mid_Plate.stl
51.8 x 21.0 x 170.2
