dotimothy/TheDoPro/CAD/Camera_Test.stl

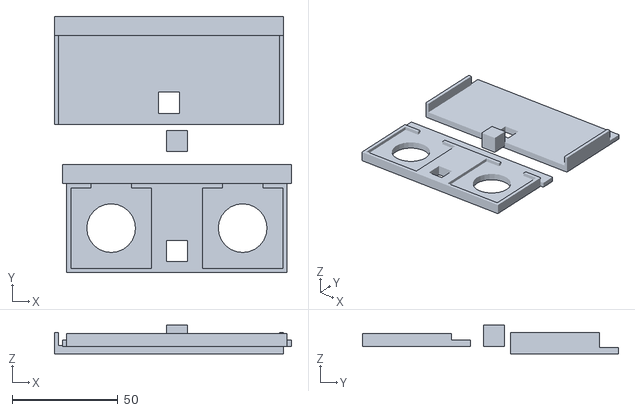
[picture p231: CAD file, 2023-03-17]
CAD/Camera_Test.stl
111.9 x 121.1 x 13.5
