dotimothy/TheDoPro/Calibration/grid.png

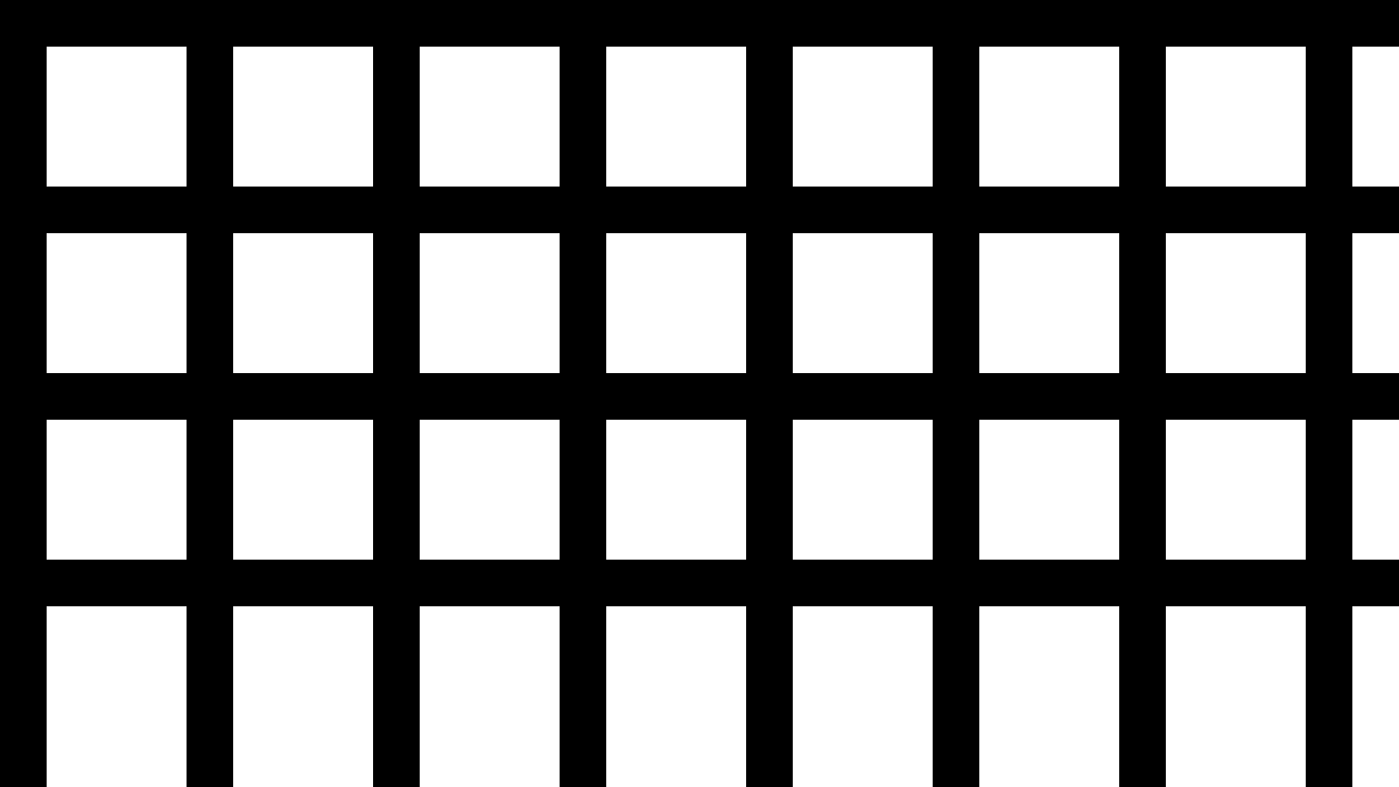
Calibration/grid.png
