dotimothy/TheDoPro/Calibration/left/L_1.png

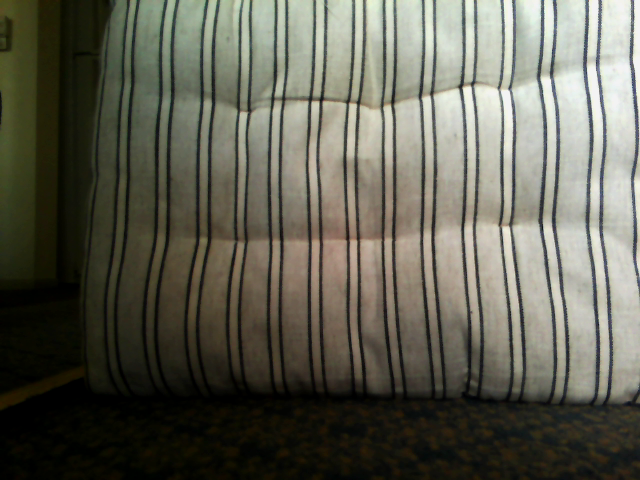
Calibration/left/L_1.png
