dotimothy/TheDoPro/Calibration/left/L_2.png

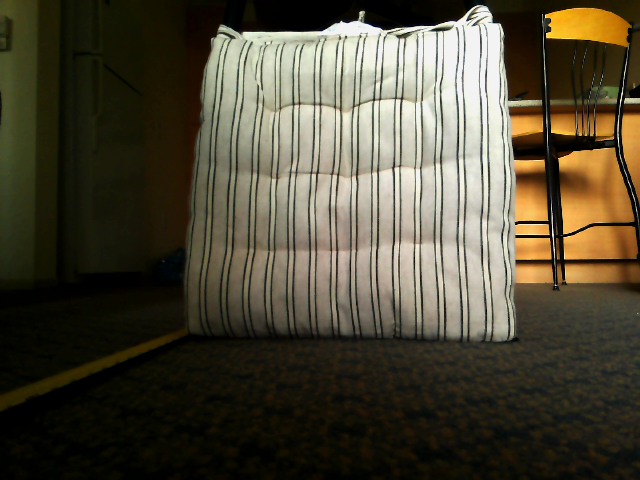
Calibration/left/L_2.png
