dotimothy/TheDoPro/Calibration/left/L_3.png

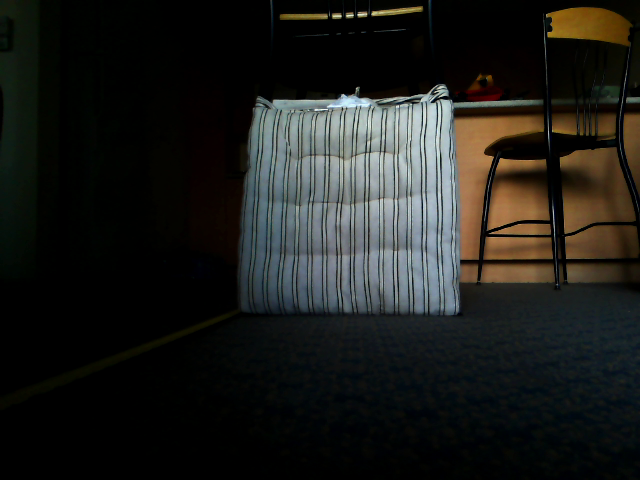
Calibration/left/L_3.png
