dotimothy/TheDoPro/Calibration/left/L_4.png

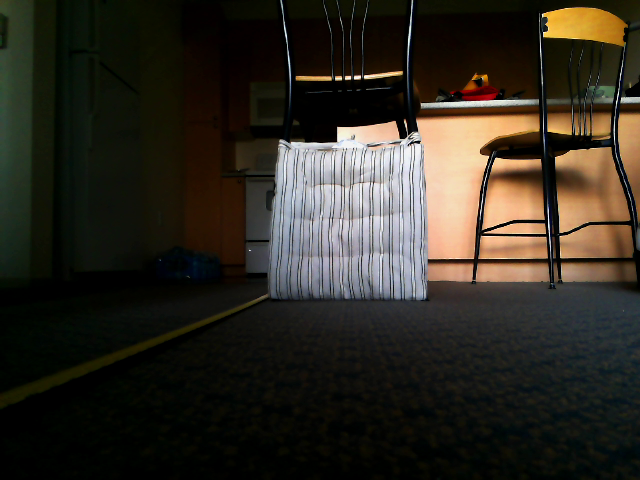
Calibration/left/L_4.png
