dotimothy/TheDoPro/Calibration/left/L_5.png

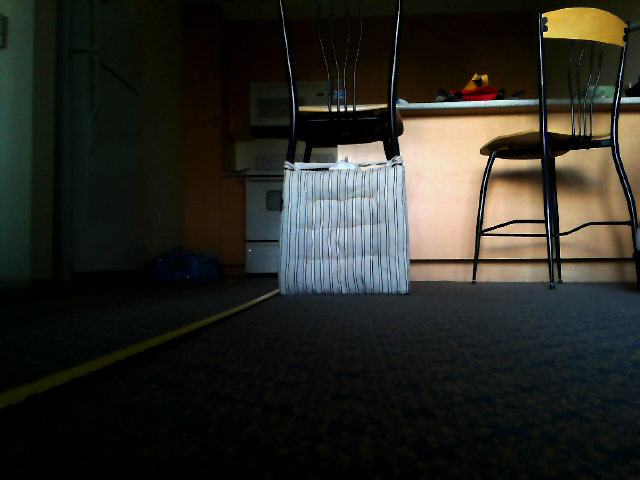
Calibration/left/L_5.png
