dotimothy/TheDoPro/Calibration/left/L_6.png

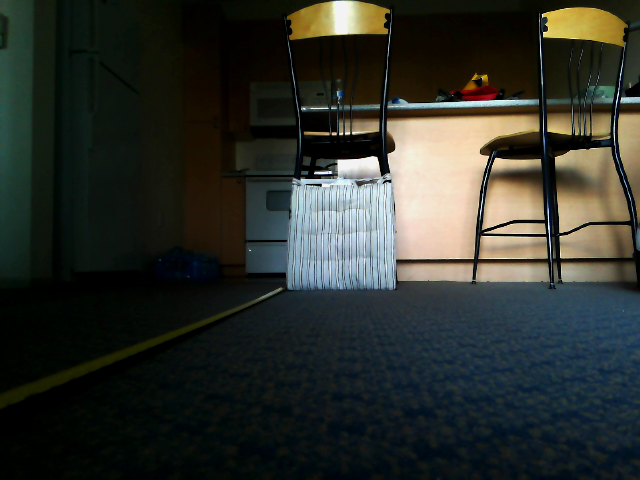
Calibration/left/L_6.png
