dotimothy/TheDoPro/Calibration/right/R_1.png

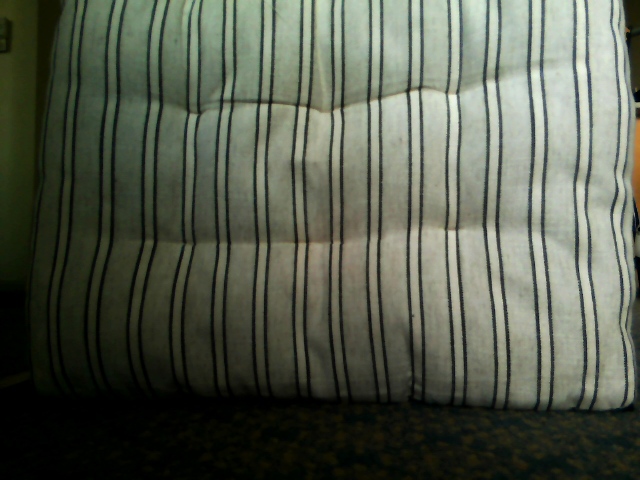
Calibration/right/R_1.png
