dotimothy/TheDoPro/Calibration/right/R_2.png

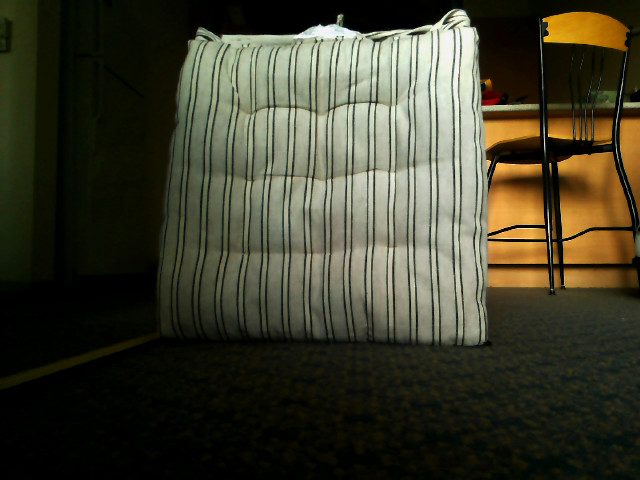
Calibration/right/R_2.png
