dotimothy/TheDoPro/Calibration/right/R_3.png

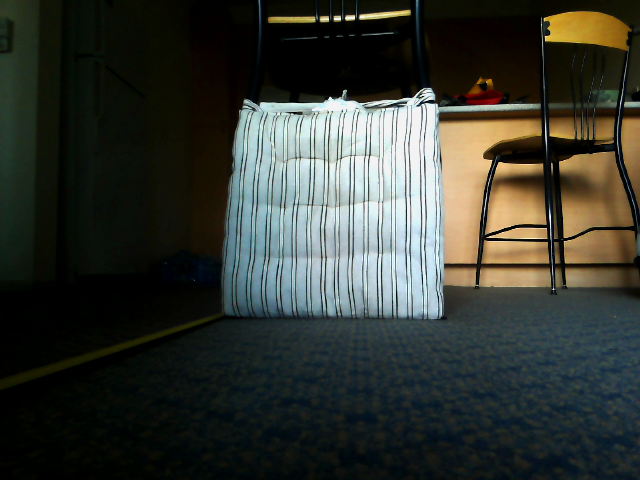
Calibration/right/R_3.png
