dotimothy/TheDoPro/Calibration/right/R_4.png

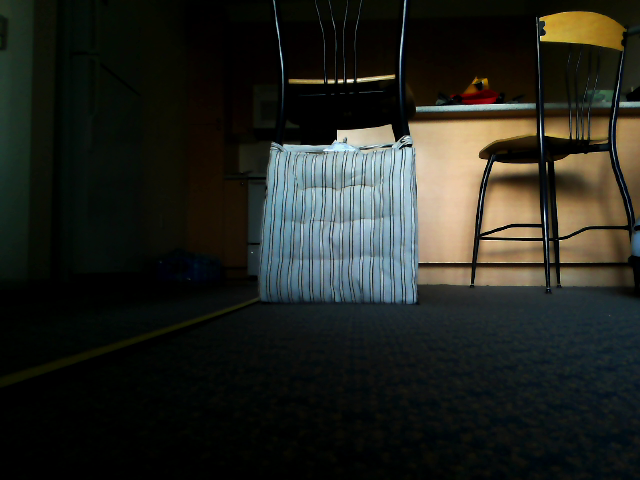
Calibration/right/R_4.png
