dotimothy/TheDoPro/Calibration/TestScenes/left/imageL0.png

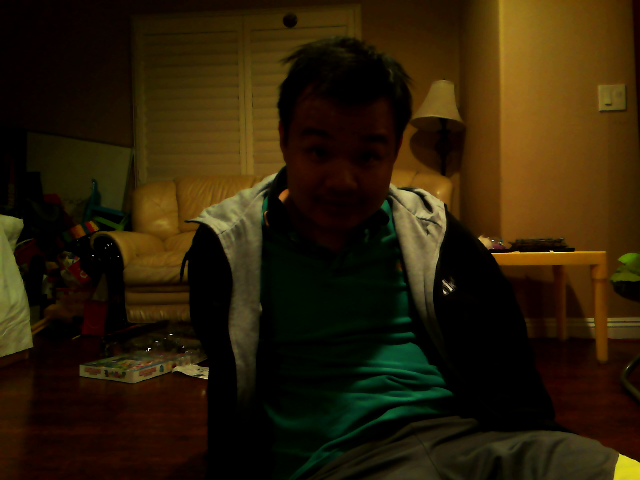
Calibration/TestScenes/left/imageL0.png
