dotimothy/TheDoPro/Calibration/TestScenes/left/imageL2.png

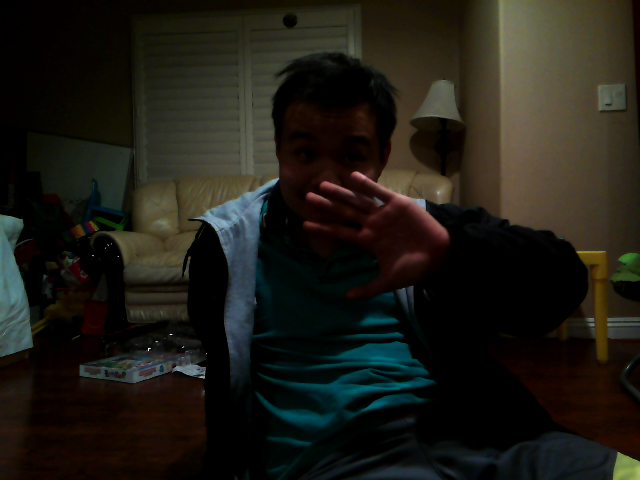
Calibration/TestScenes/left/imageL2.png
