dotimothy/TheDoPro/Calibration/TestScenes/left/imageL7.png

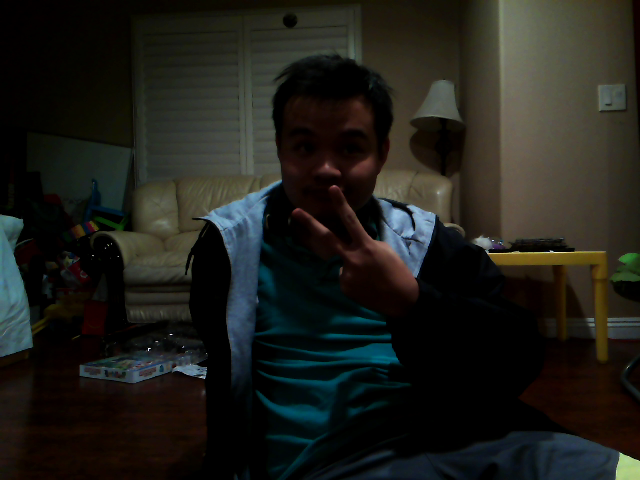
Calibration/TestScenes/left/imageL7.png
