dotimothy/TheDoPro/Calibration/TestScenes/left/imageL8.png

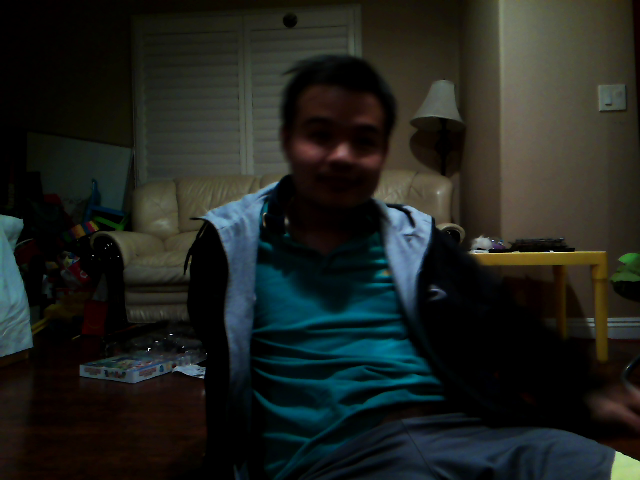
Calibration/TestScenes/left/imageL8.png
