dotimothy/TheDoPro/Calibration/TestScenes/left/imageL10.png

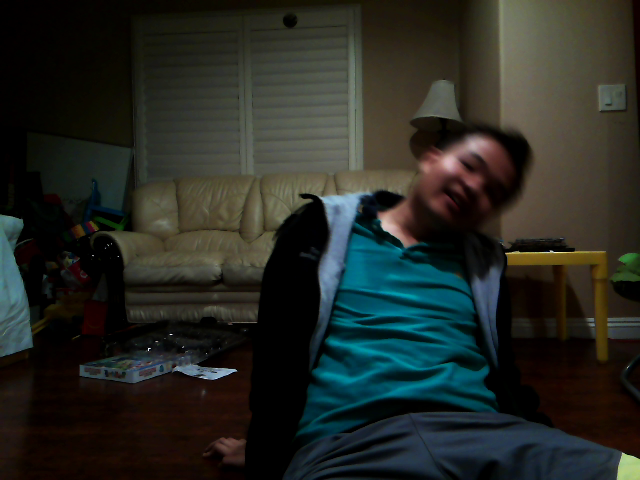
Calibration/TestScenes/left/imageL10.png
