dotimothy/TheDoPro/Calibration/TestScenes/left/imageL11.png

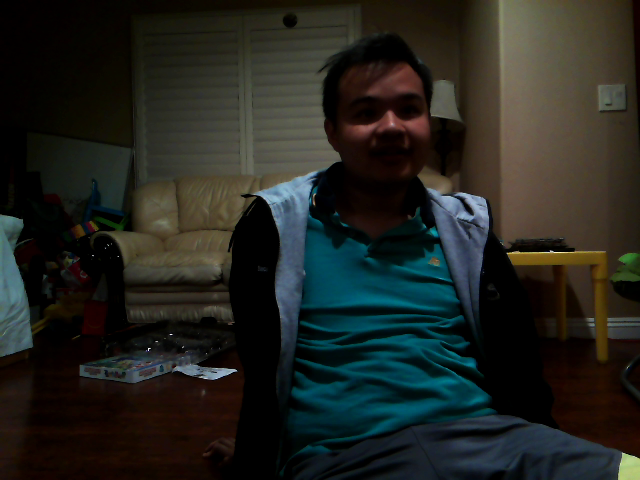
Calibration/TestScenes/left/imageL11.png
