dotimothy/TheDoPro/Calibration/TestScenes/left/imageL14.png

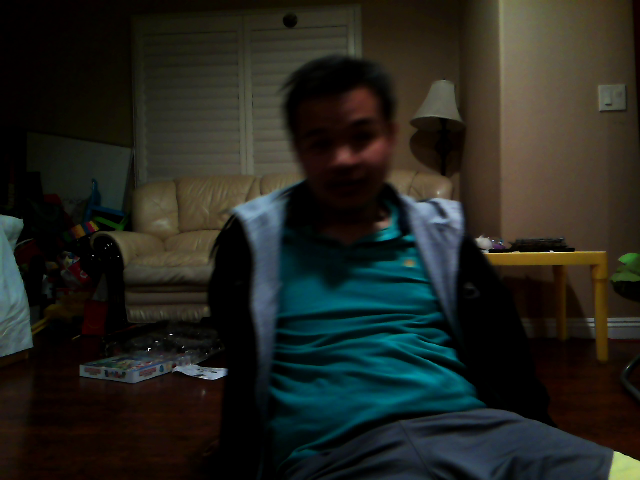
Calibration/TestScenes/left/imageL14.png
