dotimothy/TheDoPro/Calibration/TestScenes/right/imageR0.png

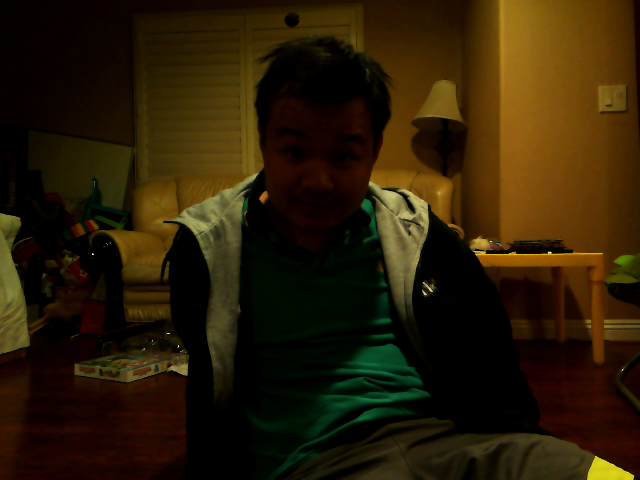
Calibration/TestScenes/right/imageR0.png
