dotimothy/TheDoPro/Calibration/TestScenes/right/imageR2.png

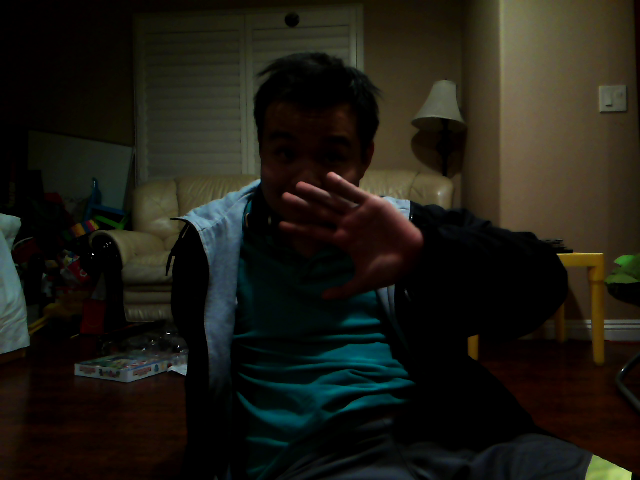
Calibration/TestScenes/right/imageR2.png
