dotimothy/TheDoPro/Calibration/TestScenes/right/imageR4.png

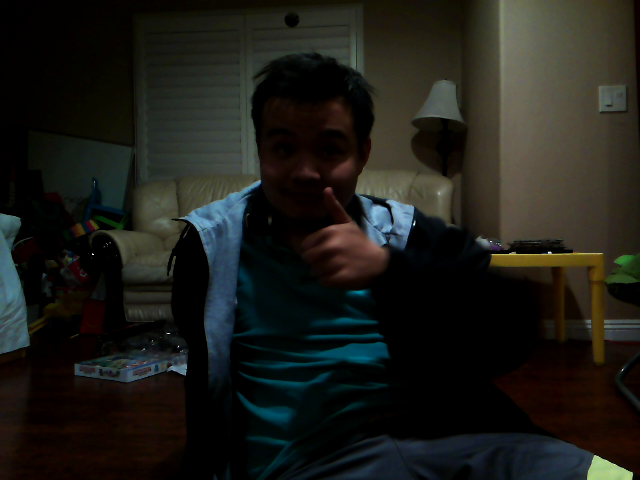
Calibration/TestScenes/right/imageR4.png
