dotimothy/TheDoPro/Calibration/TestScenes/right/imageR8.png

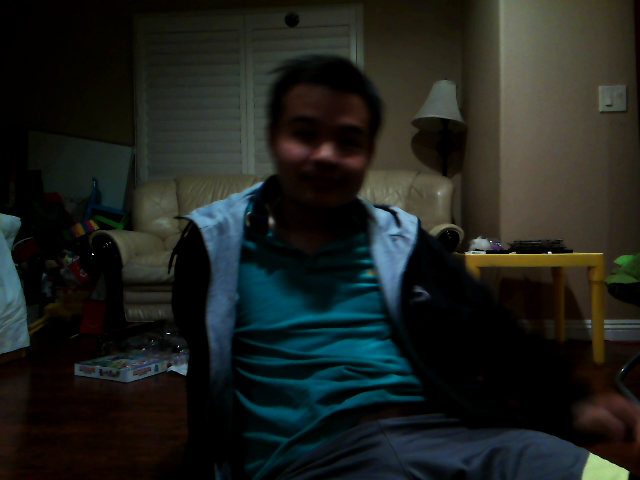
Calibration/TestScenes/right/imageR8.png
