dotimothy/TheDoPro/Calibration/TestScenes/right/imageR9.png

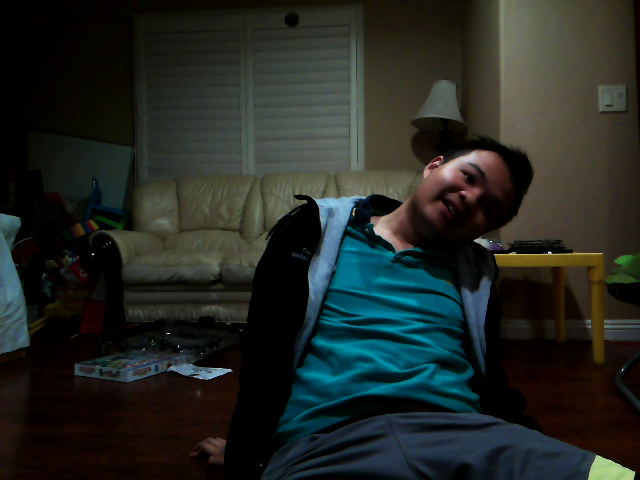
Calibration/TestScenes/right/imageR9.png
