dotimothy/TheDoPro/Vision/result2.jpg

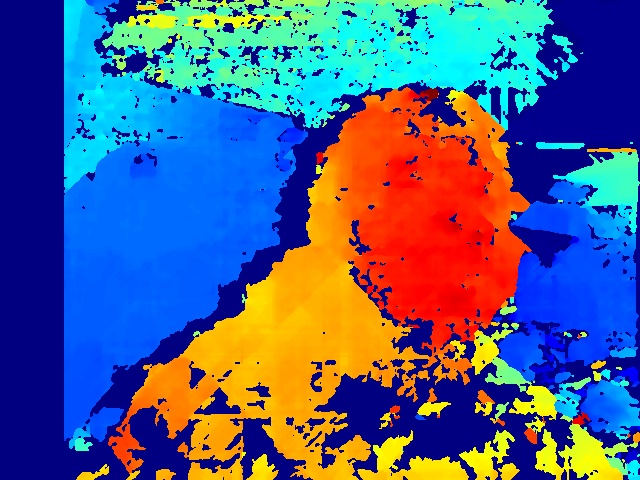
Vision/result2.jpg
