dotimothy/TheDoPro/Vision/result.png

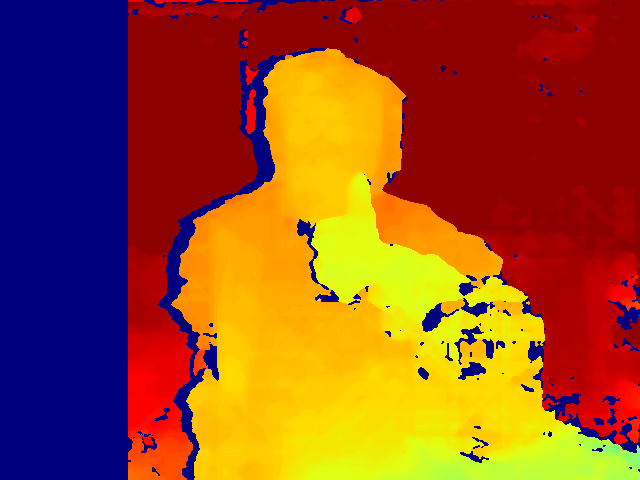
Vision/result.png
