dotimothy/TheDoPro/Vision/testScripts/result.png

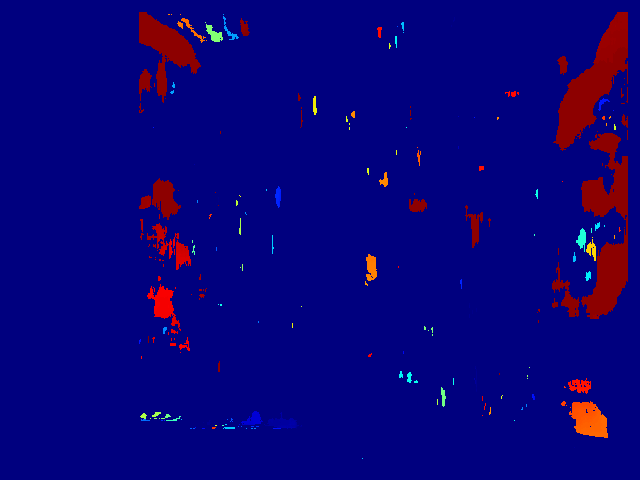
Vision/testScripts/result.png
